raznoglaz1y/enku/docs/runtime-state-machine.md

# ENKU Reader Runtime & State Machine

This document defines the baseline runtime behavior for opening books, navigating pages, changing reader settings, sleeping, waking and recovering from errors.

The goal is deterministic behavior: the same event in the same state should produce the same state transition and the same visible result.

## 1. Runtime principle

The Reader runtime is event-driven.

User input and system events update application state first. Rendering follows only when visible state changes.

Conceptually:

```text
Input/System Event
→ Event Queue
→ State Transition
→ Reader/Layout Work
→ Render Plan
→ Refresh Manager
→ Display
```

## 2. Top-level application states

ENKU uses a small set of product-level states:

- **Boot**
- **Library**
- **Book Opening**
- **Reading**
- **Reader Overlay**
- **Search**
- **Settings**
- **Import/Transfer**
- **Sleep**
- **Error/Recovery**

These are logical runtime states, not necessarily one-to-one UI screens.

## 3. Reader sub-state

When Reading is active, the runtime keeps:

- current `book_id`;
- current semantic reading position;
- current laid-out page;
- previous/next page anchors when available;
- effective typography;
- orientation;
- active bookmark state;
- visible reader chrome state;
- pending progress save state.

The displayed page is disposable. The semantic position is authoritative.

## 4. Opening a book

Canonical flow:

```text
Library
→ OpenBookRequested
→ Book Opening
→ loader validates Library/storage and opens ReaderSession
→ BookOpened
→ synchronize AppState from current Reader page
→ render first/current page
→ Reading
```

If book loading fails, `BookOpenFailed` closes any partial session and returns safely to Library with the requested book focused.

If no saved position exists, reading begins at the first valid content position.

If a saved anchor can no longer be resolved exactly, the Reader Engine should restore the nearest safe logical position.

## 5. Page Next

When the user requests Next:

1. ignore/reject duplicate input while the current page transition is not ready;
2. ask ReaderSession to advance using the current page's next semantic anchor;
3. reuse prefetched next page or ask Reader Engine to paginate it;
4. update current semantic position;
5. mark progress as dirty;
6. render the new page;
7. schedule persistence independently from display refresh.

The UI must not advance stored progress before a valid next page exists.

The first concrete implementation of this path is documented in [Reader Runtime Integration MVP](reader-runtime-mvp.md). It updates `AppState.reading_position` / `reading_progress`, marks `progress_dirty`, and emits a PageTurn `RefreshRequest` only after ReaderSession accepts the transition.

## 6. Page Previous

Previous returns to a deterministic prior logical page through ReaderSession.

The current MVP stores page-start semantic anchors actually visited during the session and keeps a disposable previous/current/next working set. If an adjacent page is not cached, it is rebuilt from the stored page-start anchor.

The runtime never approximates Previous by subtracting an arbitrary number of characters.

## 7. End of book

When no next readable content exists:

- do not wrap automatically to the beginning;
- expose the Finished state;
- allow the user to return to Library;
- preserve the final semantic position;
- mark the book Finished only through the defined completion behavior.

On EndOfBook, runtime marks the current book Finished, sets logical progress to 1.0, updates the Library summary and emits a visible status refresh. It does not wrap to the beginning.

Restarting a finished book changes its Library state back to Reading through an explicit product action.

## 8. Reader chrome / overlay

Normal Reading should remain content-first.

Opening Reader Menu or Quick Aa moves into a Reader Overlay state while preserving:

- book;
- semantic position;
- underlying page;
- orientation.

Closing the overlay returns to the exact underlying Reading state.

Opening/closing an overlay must not itself change reading progress.

## 9. Typography change

Canonical transition:

```text
Reading/Overlay
→ TypographyChanged
→ preserve semantic anchor
→ resolve effective settings
→ invalidate incompatible page cache
→ repaginate around anchor
→ render
→ return to Reading/Overlay
```

Manual typography changes switch the effective preset to Custom.

## 10. Orientation change

Canonical transition:

```text
Reading
→ OrientationChanged
→ preserve semantic anchor
→ update viewport
→ invalidate layout cache
→ repaginate
→ render full new layout
→ Reading
```

Pixel coordinates are not persisted.

## 11. Bookmark toggle

Bookmark creation stores:

- `book_id`;
- semantic position;
- optional section/chapter title;
- short text snippet;
- creation order/timestamp.

Toggling a bookmark updates state/persistence, but should only redraw a visible bookmark indicator if such an indicator is currently shown.

## 12. Table of contents navigation

Selecting a ToC entry:

1. resolve its semantic position;
2. preserve the current position as normal history/state;
3. paginate at the target;
4. update current reading position;
5. render;
6. return to Reading.

ToC navigation never depends on rendered page numbers.

## 13. Search flow

Canonical search flow:

```text
Reading
→ SearchOpen
→ query entry
→ normalized-text search
→ results list
→ result selected
→ resolve semantic position
→ paginate
→ highlight semantic match
→ Reading
```

The pre-search reading position should remain available so Back/Cancel can return the user to where search began.

Search highlighting is temporary UI state and does not alter book content.

## 14. Back behavior

Back is deterministic and context-sensitive.

When Back is pressed from Reading, runtime checkpoints dirty semantic position/progress before closing ReaderSession and returning to Library. If checkpointing fails, the Reader remains open so unsaved progress is not silently discarded.

Examples:

- Reading → Library;
- Reader Overlay → Reading;
- Search results → Search query/results context;
- Search canceled from reader → original Reading position;
- nested Settings → previous Settings level;
- recoverable error → previous safe state.

Back must never silently discard a destructive pending action without following the relevant confirmation rule.

## 15. Progress persistence

Progress saving should not block every page turn.

Recommended model:

- update in-memory semantic position immediately;
- mark progress dirty;
- persist after a short safe debounce, on important transitions, and before sleep/power-down where possible.

Important save points include:

- leaving the book;
- entering Sleep;
- explicit Power Off;
- application state checkpoint;
- selected periodic/debounced page progress.

The exact debounce interval remains an implementation detail.

## 16. Sleep

The detailed product/hardware split is defined in [Power, Sleep & Wake Model](power-model.md).

Canonical user-facing Sleep flow:

```text
active state
→ SleepRequested
→ finish/abort unsafe operation according to subsystem rules
→ persist dirty reader/app state
→ stop Wi-Fi / quiesce peripherals
→ prepare static sleep screen
→ final display update
→ e-paper sleep
→ enter verified system suspend mechanism
```

Panel-only sleep is not considered full ENKU Sleep.

No animation or live clock is maintained in Sleep.

Writes/imports/transfers may temporarily block automatic sleep.

## 17. Wake

Wake should restore the previous logical context when safe.

Typical flow:

```text
Sleep
→ Wake
→ restore application state
→ validate storage/book availability
→ restore current screen/book semantic position
→ repaginate if required
→ render
```

If the current book is unavailable, ENKU falls back to Library with a recoverable error notice rather than entering a broken Reading state.

## 18. Hard power-off / reboot recovery

Persistent state must be sufficient to recover without relying on the framebuffer.

After reboot:

- follow the staged startup sequence defined in [Boot & Startup Architecture](boot-model.md);
- validate settings/state version;
- recover or clean incomplete transactions;
- evaluate boot-loop / Recovery Mode before automatic restore;
- load Library index;
- restore last safe product state when appropriate;
- restore semantic reading position, not rendered page;
- regenerate any disposable layout/cache.

The exact hard power-off mechanism remains hardware-dependent.

## 19. Import/transfer interaction

Reading and Library state must remain logically independent from transfer progress.

During an active write/import:

- automatic sleep is suspended;
- destructive storage actions are serialized;
- display updates for progress are throttled;
- failed import does not alter existing valid books.

Manual reading may remain available only if storage access can be safely coordinated; this is an implementation choice to verify on hardware.

## 20. Error model

Errors are divided into:

- **recoverable** — user can return to the previous safe state;
- **book-specific** — one book cannot open/render;
- **storage-specific** — media unavailable or inconsistent;
- **system-level** — critical runtime failure.

Examples:

- corrupt book → Library remains available;
- missing current book after wake → return to Library;
- parser/layout failure → preserve last valid semantic position;
- failed import → existing Library remains unchanged.

Raw diagnostics belong in logs, not as primary user-facing copy.

The full error classification, logging and Recovery/Safe Mode behavior is defined in [Errors, Logging & Diagnostics](diagnostics-model.md).

## 21. Input locking and repeated actions

Physical controls can generate repeated or rapid events.

The runtime should:

- debounce hardware input;
- avoid overlapping page-layout operations;
- coalesce redundant navigation where safe;
- never start two display refreshes concurrently;
- prevent double activation of destructive actions.

Long-press behavior is defined at the input/action layer, not separately inside every screen.

## 22. State history

ENKU should keep only the navigation history needed for predictable Back behavior.

History is logical, not framebuffer-based.

It may include:

- previous screen/context;
- pre-search reading anchor;
- overlay parent;
- focused Library item;
- relevant scroll/focus state.

It should not grow without bound.

## 23. Persistence vs transient state

Persistent examples:

- current book;
- semantic reading position;
- Library view/filter/sort;
- reading settings;
- bookmarks;
- selected language;
- orientation;
- trusted Wi-Fi information.

Transient examples:

- active render plan;
- dirty rectangles;
- current display list;
- temporary search highlight;
- open animation-equivalent transition state;
- page cache.

Transient state can be rebuilt after reboot.

## 24. State transition table

| Current state | Event | Next state | Key action |
| --- | --- | --- | --- |
| Library | OpenBook | Book Opening | Resolve metadata/state and paginate |
| Book Opening | Success | Reading | Render first/current page |
| Book Opening | Failure | Error/Recovery | Return safely to Library |
| Reading | Next | Reading | Paginate next semantic position |
| Reading | Previous | Reading | Resolve deterministic previous page |
| Reading | OpenMenu | Reader Overlay | Preserve underlying page |
| Reader Overlay | Close | Reading | Restore underlying page |
| Reading | Search | Search | Preserve pre-search anchor |
| Search | OpenResult | Reading | Jump to semantic match |
| Reading | OrientationChanged | Reading | Repaginate around anchor |
| Reading | TypographyChanged | Reading | Repaginate around anchor |
| Any safe state | SleepRequested | Sleep | Persist state and sleep |
| Sleep | Wake | Previous safe state | Rebuild transient layout |
| Any | RecoverableError | Error/Recovery | Preserve valid state |
| Error/Recovery | Back/Recover | Previous safe state | Resume without corruption |

## 25. Decisions fixed by this document

- Reader runtime is event-driven.
- Semantic position is authoritative at every transition.
- Page turns update progress only after valid layout exists.
- Back behavior is deterministic and context-aware.
- Reader overlays do not alter reading position.
- Search preserves the pre-search reading position.
- Sleep persists state before entering low power where possible.
- Wake reconstructs transient layout rather than restoring framebuffer state.
- Progress writes are debounced/checkpointed rather than blocking every page turn.
- Display/layout work is serialized.
- Errors must return to a safe usable state without corrupting book/library data.

## Refresh back-pressure

The detailed refresh queue and e-paper update policy are defined in [Refresh Manager & E-Paper Update Policy](refresh-model.md).

Runtime rules:

- only one physical display update executes at a time;
- stale queued render work may be discarded when newer full-screen state supersedes it;
- page-turn input cannot create an unbounded refresh queue;
- display failure does not roll back authoritative AppState;
- hidden state changes do not produce display work.

## 26. Persisted safe runtime context

Successful transition into Reading persists `Reading + book_id` through `AppContextService`.

Back from Reading persists `Library` before destroying the active ReaderSession. If that context write fails, Back is aborted so the previously safe Reading state is not silently discarded.

At cold boot, `BootRestoreCoordinator` reuses the ordinary `OpenBookRequested` runtime path rather than creating a second special-purpose reader-opening implementation. Therefore automatic restore uses the same Library lookup, checkpoint restore, parser, ReaderSession and failure behavior as a user-initiated open.

## 27. Sleep and fast Wake

`SleepWakeCoordinator` owns the product-level Sleep transition without embedding hardware-specific PMU/deep-sleep logic in ReaderRuntime.

When Sleeping from Reading, the semantic position is checkpointed even if the normal page-turn debounce has not fired yet. This makes Sleep an explicit persistence boundary.

Fast Wake does not create a special reader-opening path. It calls the same persisted-context restore logic used by cold boot, which in turn uses `OpenBookRequested`, checkpoint restore and `ReaderBookLoader`. The difference is that Wake skips the full storage transaction scan when the suspended runtime still has mounted/valid storage.

## 28. Graceful Power Off

Power Off is a separate runtime lifecycle from Sleep.

`PowerOffCoordinator` treats shutdown as a persistence boundary: Reading position, Library summary and last-safe app context must commit before `PowerService::requestPowerOff()` is called. Network is disconnected only after those writes succeed.

The next boot restores through the normal cold-boot path, so a powered-off device does not depend on retained RAM or framebuffer state.

## 29. Library and import runtime

The first concrete Library controller is now `LibraryRuntimeController`.

Canonical Library path:

```text
LibraryRefreshRequested
→ LibraryService::query()
→ bounded LibraryPage
→ normalize focus by book_id
→ RefreshService
```

Filter, sort and search events update typed `AppState.library` query state before re-running the query.

Opening a focused item does not duplicate Reader logic:

```text
OpenFocusedBookRequested
→ focused book_id
→ ReaderRuntimeController(OpenBookRequested)
→ normal Reader open/checkpoint/context flow
```

Import path:

```text
ImportRequested
→ import_active = true
→ StagedBookImportService
→ success / duplicate / failure
→ import_active = false
→ on success reload Library + focus imported book
```

This connects the import activity flag already consumed by Sleep and Power Off policy to a real runtime operation rather than leaving it as a passive field.

## 30. Delete focused book

Library runtime now accepts `DeleteFocusedBookRequested` only while the Library screen is active and no import transaction is running.

```text
DeleteFocusedBookRequested
→ BookDeleteService
→ remove Library/source/checkpoint/context safely
→ re-run active Library query
→ normalize focus by book_id
→ refresh Library
```

A failed delete returns `LibraryRuntimeResult::DeleteFailed` and does not masquerade as an empty Library or successful removal.

## 31. Physical input dispatch

Input now has three explicit layers:

```text
ESP-IDF GPIO polling
→ PhysicalInputEvent
→ InputActionMapper
→ LogicalAction
→ InputDispatcher
→ Library / Reader / Sleep-Wake / Power-Off runtime
```

This prevents board GPIO semantics from leaking into application controllers and makes the same runtime path testable with synthetic physical events on the host.

## 32. Concrete e-paper refresh service

The first physical `RefreshService` implementation is now `EpaperRefreshService`.

Its input remains the framework-neutral `RefreshRequest`.

Policy:

```text
RefreshClass::Full
→ true SSD1677 full refresh

RefreshClass::Region + valid small dirty_region + established base frame
→ partial refresh

RefreshClass::Region + missing/invalid/large dirty_region
→ escalate to fast full-screen refresh

RefreshClass::Deferred
→ fast full-screen refresh
```

A region larger than one third of the panel area is currently escalated.

The service also tracks:

- total requests;
- region refreshes;
- full-screen refreshes;
- escalations;
- coalesced generations;
- obsolete generations;
- failures.

`cancelObsolete(min_generation)` does not interrupt an in-flight physical panel transaction; it prevents older queued/subsequent requests from being applied.

## 33. Mono framebuffer boundary

`MonoFramebufferSource` separates rendering from display transport.

The e-paper service only knows:

- framebuffer dimensions;
- full 1-bit buffer;
- extraction of a dirty region.

`OwnedMonoFramebuffer` is the first concrete implementation and supports byte-aligned region extraction for SSD1677 partial windows.

The eventual Library/Reader renderer can write into this buffer without depending on ESP-IDF or SSD1677 APIs.

## 34. Application storage runtime composition

`ApplicationStorageRuntime` is now the first framework-neutral application composition layer above a pair of filesystem adapters.

It owns:

```text
AppState
CborSettingsService
SettingsRuntimeController
CborLibraryService
BookImportService
StagedBookImportService
CborReaderCheckpointService
CborAppContextService
CborBootLoopService
BookDeleteService
StoredBookSourceService
StorageStartupCoordinator
```

Construction requires only:

```text
StateFileStore
BookFileStore
```

This means the same composition is exercised with POSIX stores in host tests and with the ESP-IDF SD/FAT stores on the real board target.

The Reader controller graph is intentionally not owned here yet. Its remaining concrete dependency is a real `TextMeasurer`/render pipeline; introducing a fake device-side measurer would hide the actual integration work still required.

## 35. Real Reader font measurement and rasterization

The ESP-IDF target now has a concrete `FreeTypeTextRenderer`.

It serves two roles from the same Noto Sans face:

```text
TextMeasurer
→ exact FreeType advance/kerning metrics for pagination

Page renderer
→ FreeType monochrome glyph rasterization into OwnedMonoFramebuffer
```

The default Reader font path is:

```text
/sdcard/system/fonts/NotoSans-Regular.ttf
```

The font is intentionally loaded from the FAT filesystem rather than hidden behind a compile-time substitute. If the file is missing, initialization returns `FontNotFound`; ENKU does not silently replace Noto Sans with a different typeface.

Measurements support UTF-8 code points and FreeType kerning. Line height uses the face's actual size metrics multiplied by the current Reader line-spacing setting.

Rendering uses `FT_RENDER_MODE_MONO` and writes the resulting 1-bit glyph bitmaps directly into the existing 1-bit ENKU framebuffer.

This aligns pagination and rendering: the same font engine and size determine both where lines wrap and where glyphs are drawn.

## 36. Application Reader runtime composition

`ApplicationReaderRuntime` now composes the first complete Library/Reader controller graph above `ApplicationStorageRuntime`.

It owns:

```text
ReaderBookLoader
ReaderRuntimeController
LibraryRuntimeController
BootRestoreCoordinator
```

Dependencies are explicit:

```text
ApplicationStorageRuntime
RefreshService
TextMeasurer
ReaderPageRenderer
LibraryPageRenderer
TypographySettings
Viewport
```

On ESP-IDF, one `FreeTypeTextRenderer` supplies all three text/render roles: measurement, Reader page rendering and Library rendering.

## 37. Render-before-refresh contract

Both Reading and Library now update the framebuffer before submitting a physical refresh.

Reader:

```text
ReaderSession page transition
→ update semantic state
→ ReaderPageRenderer
→ RefreshService
```

Library:

```text
query/focus/view state change
→ LibraryPageRenderer
→ RefreshService
```

A renderer failure is surfaced explicitly (`RenderFailed`) rather than allowing runtime state to claim that an unrendered frame became visible.

The first ESP-IDF Library renderer is intentionally simple but real: Noto Sans header, title/author/progress rows and a focus outline.

## 38. ESP-IDF DeviceRuntime

`EspIdfDeviceRuntime` is the first board-specific application composition root above `EspIdfPlatform`.

It connects:

```text
EspIdfPlatform
→ ApplicationStorageRuntime
→ FreeTypeTextRenderer
→ ApplicationReaderRuntime
→ SleepWakeCoordinator
→ PowerOffCoordinator
→ InputDispatcher
```

Boot sequence:

```text
platform begin
→ font availability / FreeType init
→ storage/settings/library startup
→ boot-loop/context restore
→ restore Reading or settle Library
→ apply Wi-Fi policy
→ synchronize network/power state
→ render initial Library when needed
→ enter application loop
```

A missing Noto Sans asset is treated as a provisioning state, not silently substituted with another font.

## 39. Persistent application loop

The normal ESP-IDF execution path no longer ends after a finite input smoke test.

After successful DeviceRuntime initialization, firmware continuously polls the board controls at the configured 5 ms cadence and dispatches events through the real application graph.

Hardware smoke tests remain available behind `CONFIG_ENKU_BRINGUP_SMOKE_TESTS` while physical validation is in progress.

The current persistent loop is intentionally synchronous: page layout, rendering and e-paper refresh complete before the next visible transition is accepted. This favors deterministic e-paper behavior over premature concurrency; later profiling may introduce task separation where measured benefit justifies it.

## 40. Orientation-aware pagination and rendering

Orientation is now a real layout/rendering input rather than a persisted flag only.

The Reader derives the logical viewport from the native panel geometry:

```text
Portrait  = short side × long side
Landscape = long side × short side
```

For the current 800×480 panel:

```text
Portrait  = 480×800
Landscape = 800×480
```

Reader pagination always works in logical coordinates.

The ESP-IDF FreeType renderer then maps logical pixels into the controller-native 800×480 framebuffer. Portrait currently uses a clockwise 90° transform; the exact physical rotation direction remains easy to swap after enclosure/orientation validation without changing Reader pagination semantics.

### Live orientation reflow

`ApplicationReaderRuntime::applyOrientation()` now performs a durable, live orientation transition.

While Reading:

```text
save new Orientation setting
→ preserve current semantic page anchor
→ derive new logical viewport
→ ReaderSession::invalidateLayout()
→ repaginate from the same semantic position
→ render in the new orientation
→ full visible refresh
```

The semantic text offset remains authoritative and is preserved across the reflow.

While Library is visible, the same operation persists the setting and re-renders the Library in the new logical geometry.

If runtime application of the new orientation fails after persistence, ENKU performs a best-effort rollback to the previous durable setting and previous layout.

## Library return-state preservation

Library navigation state is intentionally preserved in-memory while opening and closing a book:

- current query offset remains unchanged;
- the focused book remains selected;
- Grid/List view remains controlled by persisted GlobalSettings;
- returning from Reading refreshes the same Library window instead of resetting to offset 0;
- changing orientation while Library is visible re-renders the current window without resetting offset or focus.

This applies to ordinary Library browsing and keeps the same runtime position across Reader open → Back transitions.

## Library query-state rules

Library query transitions use deterministic navigation rules:

- changing Filter switches to Browse mode, clears active search text, resets offset to 0, and preserves the focused book only when it remains present in the new first window; otherwise focus moves to the first valid item;
- changing Sort or sort direction preserves Browse/Search mode and current search text, resets offset to 0, and keeps the focused book only when it is present in the new first window;
- changing Grid/List view does not change offset, focused book, active search text, or query mode;
- orientation changes redraw/reload the current Library window without resetting offset or focus.

## Library mutation pagination rules

Library mutations keep pagination valid and deterministic:

- deleting the last visible book on the last query window clamps offset to the last valid window and focuses a valid remaining book;
- deleting the final book in the Library leaves an empty page with no focused book;
- successful import exits Search mode and clears the active search text;
- after import, the runtime reveals and focuses the imported book in whatever query window contains it, including Recently Added with ascending order;
- import reveal respects the current page limit and sort direction instead of assuming the imported book is in the first window.

## Book Details runtime

Book Details is a dedicated runtime screen opened for the currently focused Library book.

Semantic content is identical in portrait and landscape; orientation changes layout only.

Primary action is derived from canonical reading state:

- New -> Start;
- Reading -> Continue;
- Finished -> Read again.

Read again always enters the approved restart confirmation first. Confirmation defaults to Cancel. A confirmed restart erases the saved reading checkpoint, resets summary progress to 0, transitions the book to Reading, preserves the source book and other per-book domains, then opens the book from the beginning.

Delete Book enters a separate destructive confirmation with Cancel as the default focus. Confirmed deletion uses the transactional BookDeleteService and returns to Library with pagination/focus normalized.

Back from a confirmation cancels the confirmation without changing book data. Back from Book Details returns to the same Library context.
