raznoglaz1y/enku/docs/screens.md

# Screen inventory

This file indexes the screen assets currently stored in the repository.

The **Figma design system is the current visual source of truth** for active UI work. Existing RU PNG boards remain valuable historical/reference material, while EN boards in the repository may be drafts or incomplete until they pass the review workflow.

Current design-state rules:

- English is the canonical/source UI language.
- Approved final review boards are PNG.
- Temporary EN SVG screen compositions are intermediate artifacts only.
- Figma component work currently includes Foundations, Statusbar, Header and Primary Button; Universal Row is in progress.
- A board is not implementation-ready merely because a historical file exists in this index.
- Implementation readiness is defined by [UI audit](ui-audit.md), [UI specification](ui-spec.md) and [UI revision plan](ui-revision-plan.md).

The table below is therefore an **asset inventory**, not a statement that each listed board is current or approved.

| Board | Available file | English |
| --- | --- | --- |
| ENKU_about_device | [PNG](../design/screens/ru/ENKU_about_device_v1.png) | pending |
| ENKU_add_book | [PNG](../design/screens/ru/ENKU_add_book_v1.png) | pending |
| ENKU_book_details | [PNG](../design/screens/ru/ENKU_book_details_v1.png) | pending |
| ENKU_book_error | [PNG](../design/screens/ru/ENKU_book_error_v2.png) | pending |
| ENKU_book_finished | [PNG](../design/screens/ru/ENKU_book_finished_v1.png) | pending |
| ENKU_book_validation | [PNG](../design/screens/ru/ENKU_book_validation_v1.png) | pending |
| ENKU_cancel_transfer | [PNG](../design/screens/ru/ENKU_cancel_transfer_v1.png) | pending |
| ENKU_contents_bookmarks | [PNG](../design/screens/ru/ENKU_contents_bookmarks_v3.png) | pending |
| ENKU_delete_book | [PNG](../design/screens/ru/ENKU_delete_book_v2.png) | pending |
| ENKU_display_settings | [PNG](../design/screens/ru/ENKU_display_settings_v1.png) | pending |
| ENKU_empty_bookmarks | [PNG](../design/screens/ru/ENKU_empty_bookmarks_v1.png) | pending |
| ENKU_empty_filter | [PNG](../design/screens/ru/ENKU_empty_filter_v1.png) | pending |
| ENKU_empty_library | [PNG](../design/screens/ru/ENKU_empty_library_v1.png) | pending |
| ENKU_empty_networks | [PNG](../design/screens/ru/ENKU_empty_networks_v1.png) | pending |
| ENKU_english_check | [PNG](../design/screens/en/ENKU_english_check_v1.png) | sample only |
| ENKU_file_browser | [PNG](../design/screens/ru/ENKU_file_browser_v1.png) | pending |
| ENKU_filter_sort | [PNG](../design/screens/ru/ENKU_filter_sort_v1.png) | pending |
| ENKU_first_start_controls | [PNG](../design/screens/ru/ENKU_first_start_controls_v1.png) | pending |
| ENKU_first_start_language | [PNG](../design/screens/ru/ENKU_first_start_language_v1.png) | pending |
| ENKU_first_start_orientation | [PNG](../design/screens/ru/ENKU_first_start_orientation_v1.png) | pending |
| ENKU_focus_states | [PNG](../design/screens/ru/ENKU_focus_states_v1.png) | pending |
| ENKU_forget_network | [PNG](../design/screens/ru/ENKU_forget_network_v1.png) | pending |
| ENKU_import_complete | [PNG](../design/screens/ru/ENKU_import_complete_v1.png) | pending |
| ENKU_import_methods | [PNG](../design/screens/ru/ENKU_import_methods_v1.png) | pending |
| ENKU_import_summary | [PNG](../design/screens/ru/ENKU_import_summary_v1.png) | pending |
| ENKU_language | [PNG](../design/screens/ru/ENKU_language_v1.png) | pending |
| ENKU_library | [PNG](../design/screens/ru/ENKU_library_v1.png) | pending |
| ENKU_library_list | [PNG](../design/screens/ru/ENKU_library_list_v1.png) | pending |
| ENKU_library_search | [PNG](../design/screens/ru/ENKU_library_search_v1.png) | pending |
| ENKU_long_text_check | [PNG](../design/screens/ru/ENKU_long_text_check_v1.png) | pending |
| ENKU_low_battery | [PNG](../design/screens/ru/ENKU_low_battery_v1.png) | pending |
| ENKU_memory_card_error | [PNG](../design/screens/ru/ENKU_memory_card_error_v1.png) | pending |
| ENKU_navigation_status | [PNG](../design/screens/ru/ENKU_navigation_status_v2.png) | pending |
| ENKU_no_contents | [PNG](../design/screens/ru/ENKU_no_contents_v1.png) | pending |
| ENKU_no_memory_card | [PNG](../design/screens/ru/ENKU_no_memory_card_v1.png) | pending |
| ENKU_no_search_results | [PNG](../design/screens/ru/ENKU_no_search_results_v1.png) | pending |
| ENKU_not_enough_space | [PNG](../design/screens/ru/ENKU_not_enough_space_v1.png) | pending |
| ENKU_portrait_orientation | [PNG](../design/screens/ru/ENKU_portrait_orientation_v2.png) | pending |
| ENKU_power_off | [PNG](../design/screens/ru/ENKU_power_off_v1.png) | pending |
| ENKU_quick_aa_preview | [PNG](../design/screens/ru/ENKU_quick_aa_preview_v3.png) | pending |
| ENKU_reading_menu | [PNG](../design/screens/ru/ENKU_reading_menu_v2.png) | pending |
| ENKU_replace_book | [PNG](../design/screens/ru/ENKU_replace_book_v1.png) | pending |
| ENKU_restart_reading | [PNG](../design/screens/ru/ENKU_restart_reading_v1.png) | pending |
| ENKU_saved_networks | [PNG](../design/screens/ru/ENKU_saved_networks_v1.png) | pending |
| ENKU_search_in_book | [PNG](../design/screens/ru/ENKU_search_in_book_v1.png) | pending |
| ENKU_search_match | [PNG](../design/screens/ru/ENKU_search_match_v1.png) | pending |
| ENKU_settings | [PNG](../design/screens/ru/ENKU_settings_v1.png) | pending |
| ENKU_sleep_cover | [PNG](../design/screens/ru/ENKU_sleep_cover_v1.png) | pending |
| ENKU_sleep_screen | [PNG](../design/screens/ru/ENKU_sleep_screen_v1.png) | pending |
| ENKU_sleep_settings | [PNG](../design/screens/ru/ENKU_sleep_settings_v1.png) | pending |
| ENKU_storage_import | [PNG](../design/screens/ru/ENKU_storage_import_v1.png) | pending |
| ENKU_transfer_interrupted | [PNG](../design/screens/ru/ENKU_transfer_interrupted_v1.png) | pending |
| ENKU_transfer_progress | [PNG](../design/screens/ru/ENKU_transfer_progress_v2.png) | pending |
| ENKU_typography | [PNG](../design/screens/ru/ENKU_typography_v1.png) | pending |
| ENKU_ui_kit_core | [PNG](../design/screens/ru/ENKU_ui_kit_core_v1.png) | pending |
| ENKU_usb_transfer | [PNG](../design/screens/ru/ENKU_usb_transfer_v2.png) | pending |
| ENKU_wifi | [PNG](../design/screens/ru/ENKU_wifi_v1.png) | pending |
| ENKU_wifi_password | [PNG](../design/screens/ru/ENKU_wifi_password_v3.png) | pending |
| ENKU_wifi_transfer | [PNG](../design/screens/ru/ENKU_wifi_transfer_v1.png) | pending |
