raznoglaz1y/enku/design/screens/ru/ENKU_about_device_v1.png

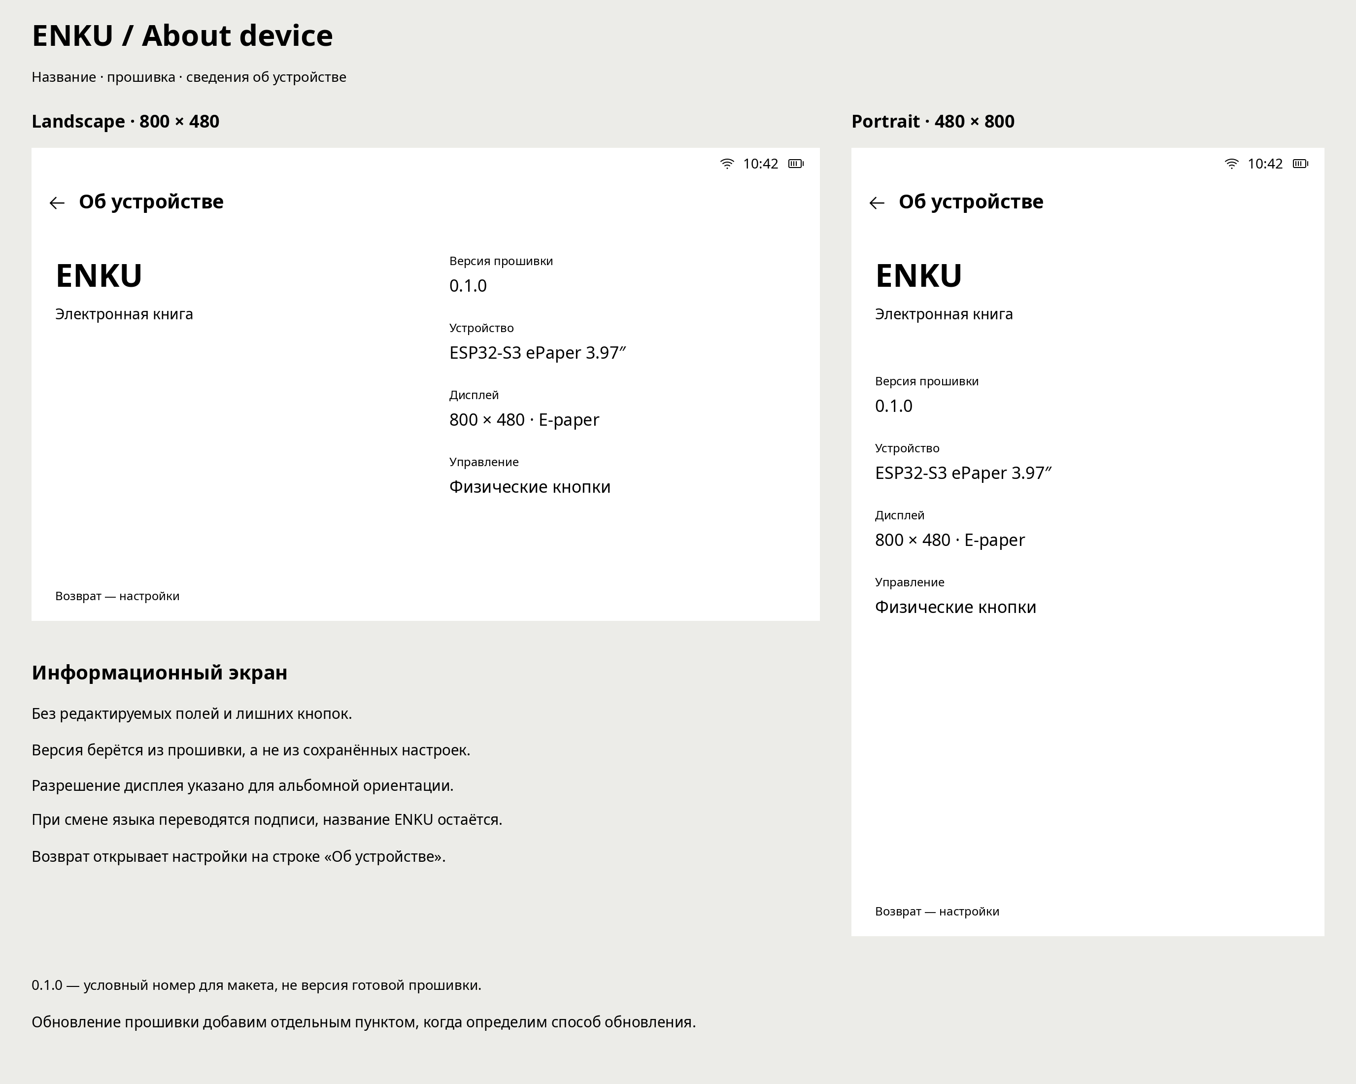
design/screens/ru/ENKU_about_device_v1.png
