raznoglaz1y/enku/design/screens/ru/ENKU_add_book_v1.png

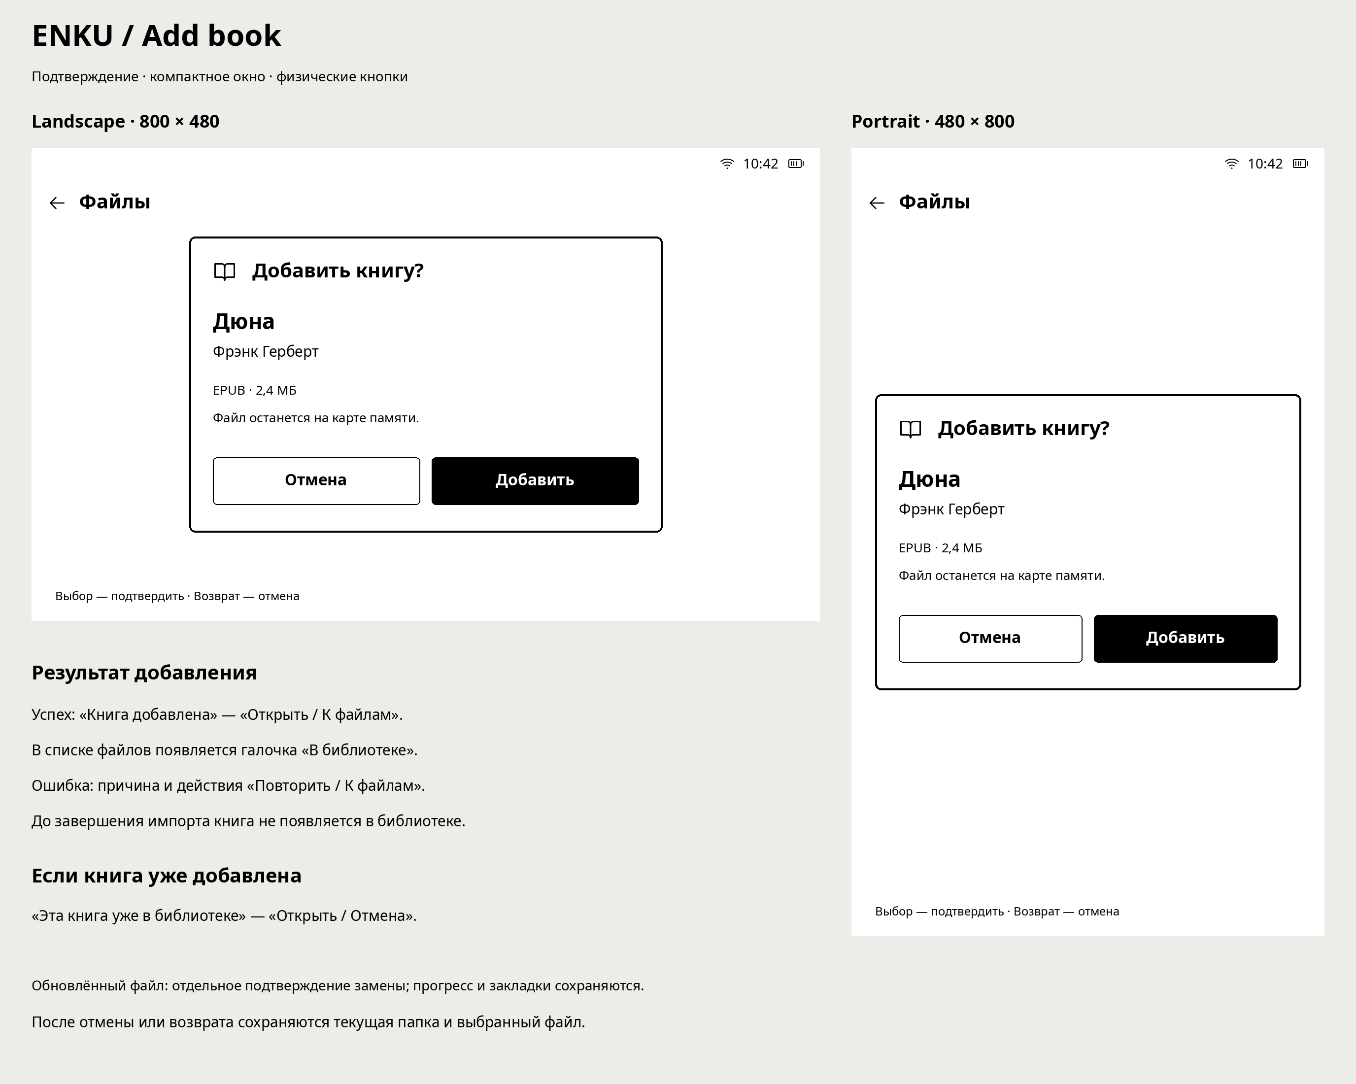
design/screens/ru/ENKU_add_book_v1.png
