raznoglaz1y/enku/design/screens/ru/ENKU_book_details_v1.png

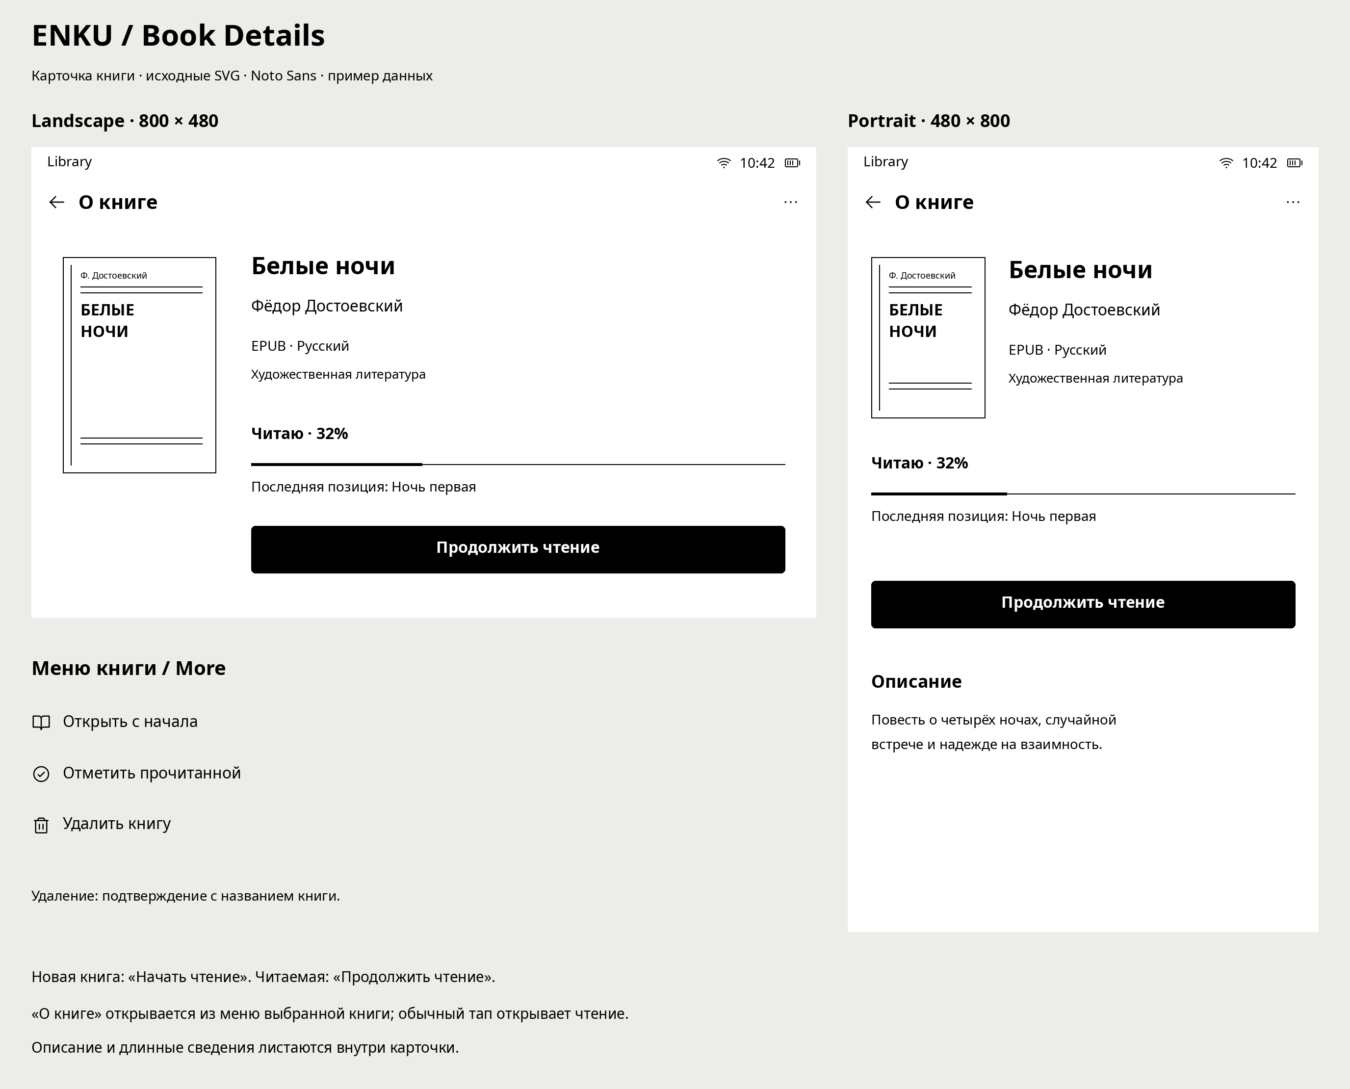
design/screens/ru/ENKU_book_details_v1.png
