raznoglaz1y/enku/design/screens/ru/ENKU_book_error_v2.png

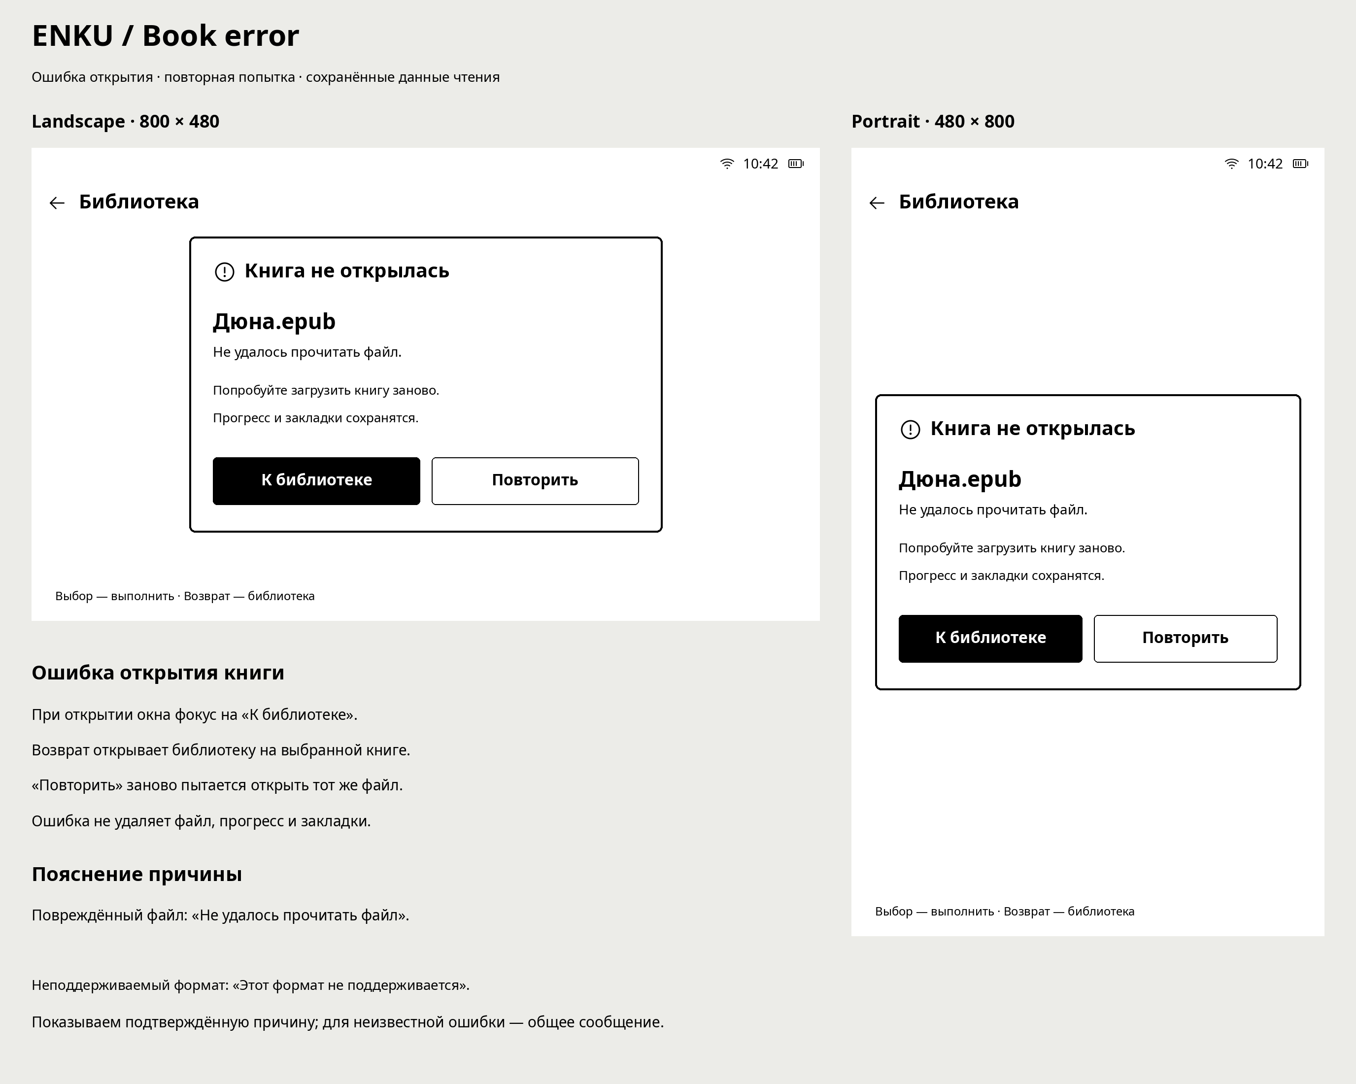
design/screens/ru/ENKU_book_error_v2.png
