raznoglaz1y/enku/design/screens/ru/ENKU_book_finished_v1.png

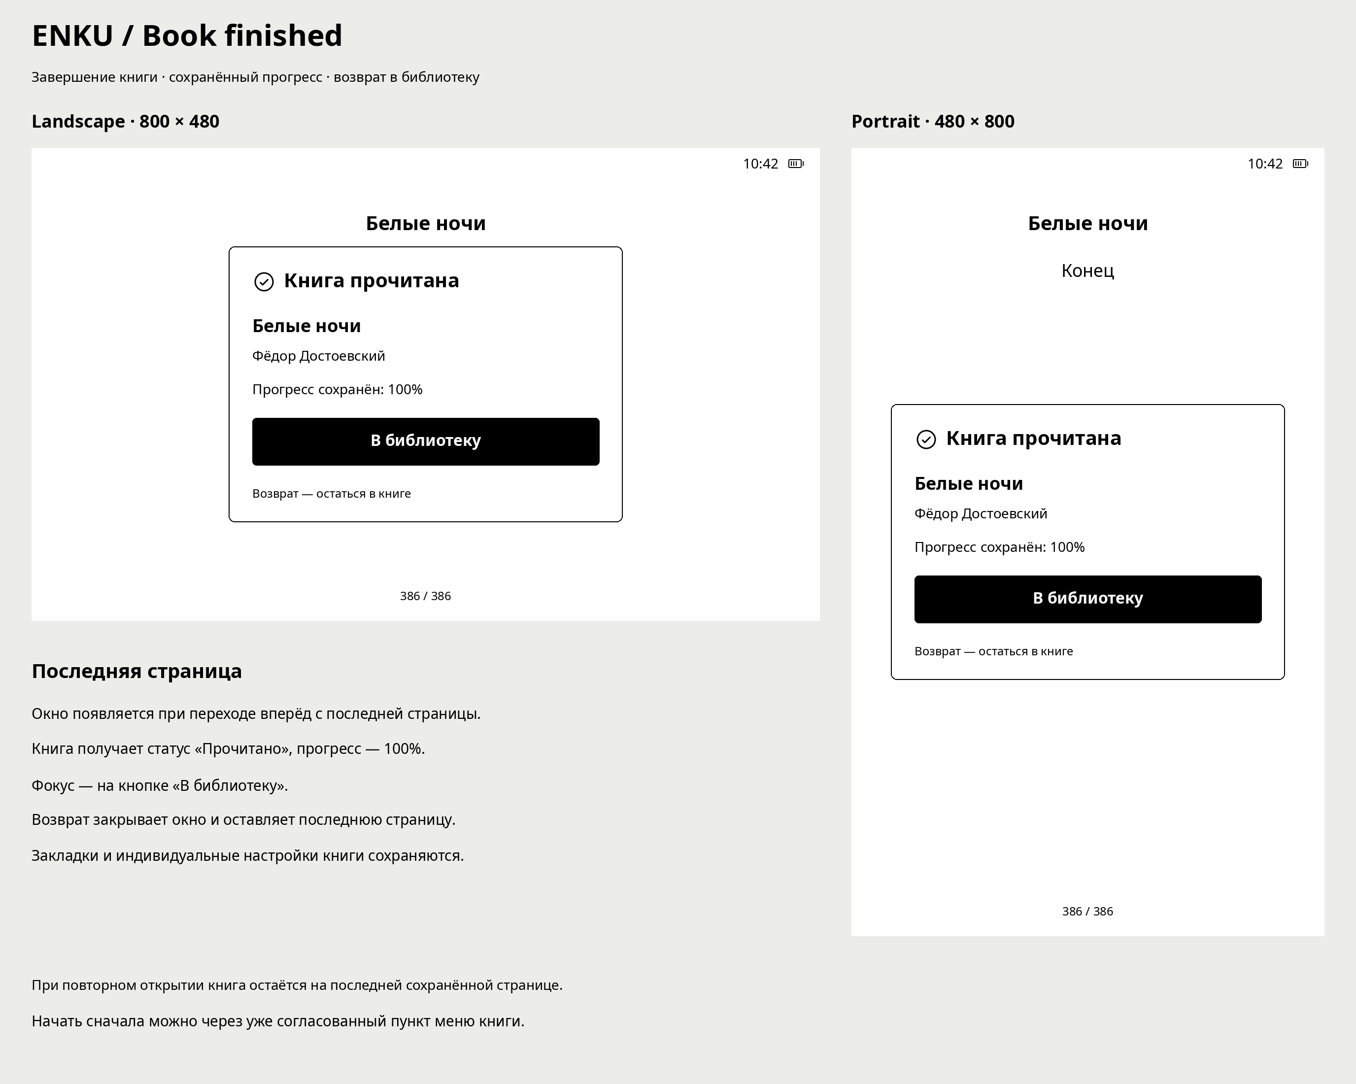
design/screens/ru/ENKU_book_finished_v1.png
