raznoglaz1y/enku/design/screens/ru/ENKU_cancel_transfer_v1.png

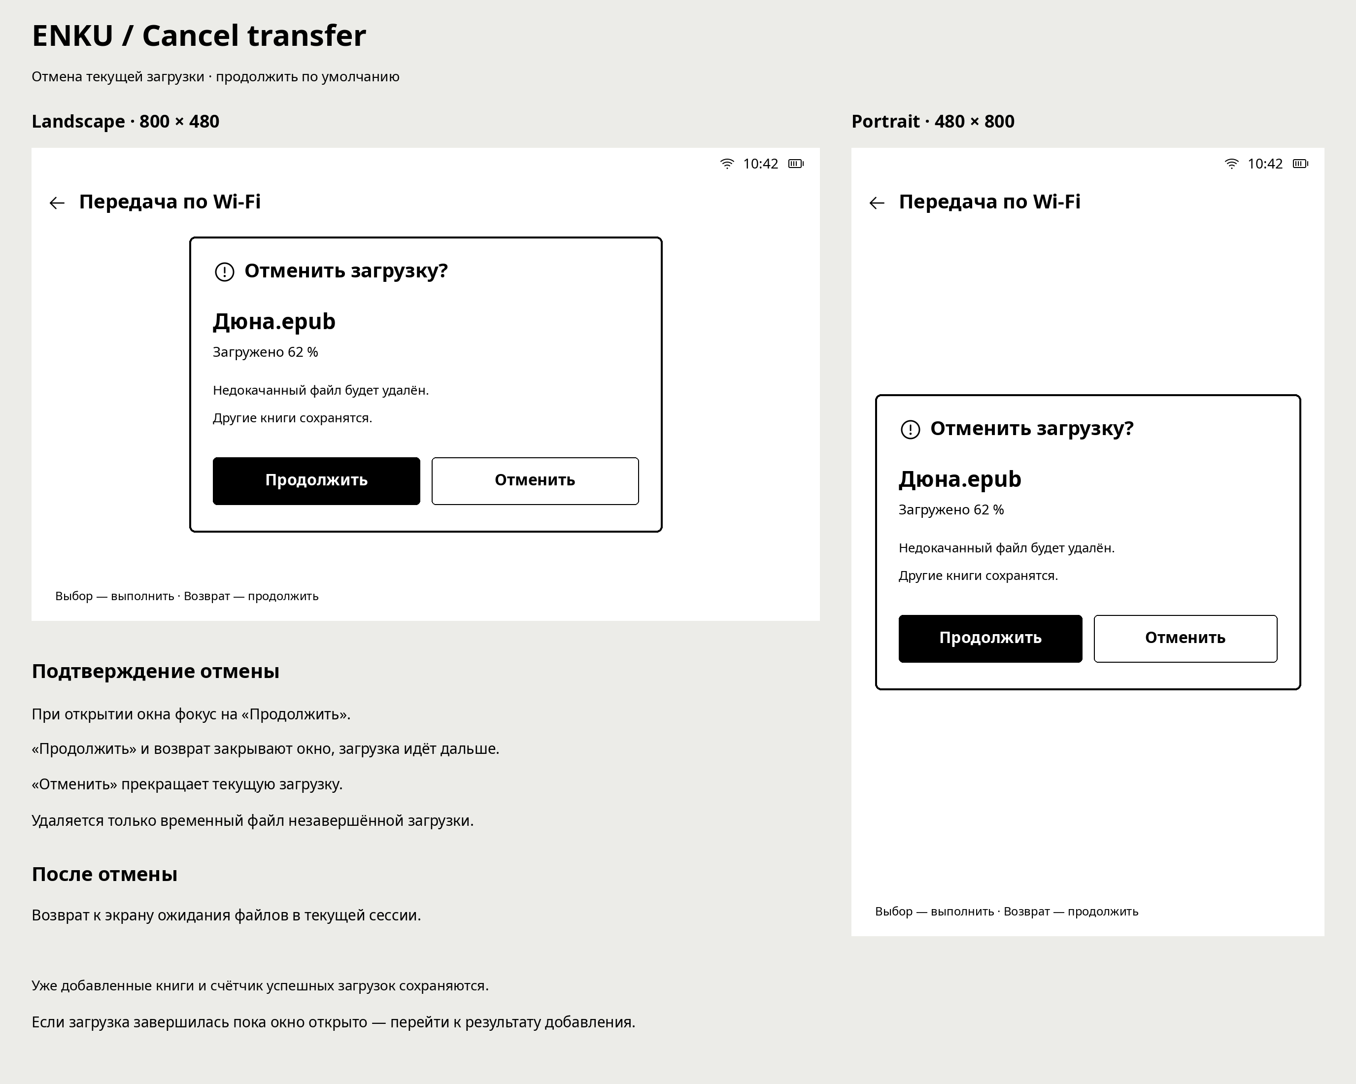
design/screens/ru/ENKU_cancel_transfer_v1.png
