raznoglaz1y/enku/design/screens/ru/ENKU_contents_bookmarks_v3.png

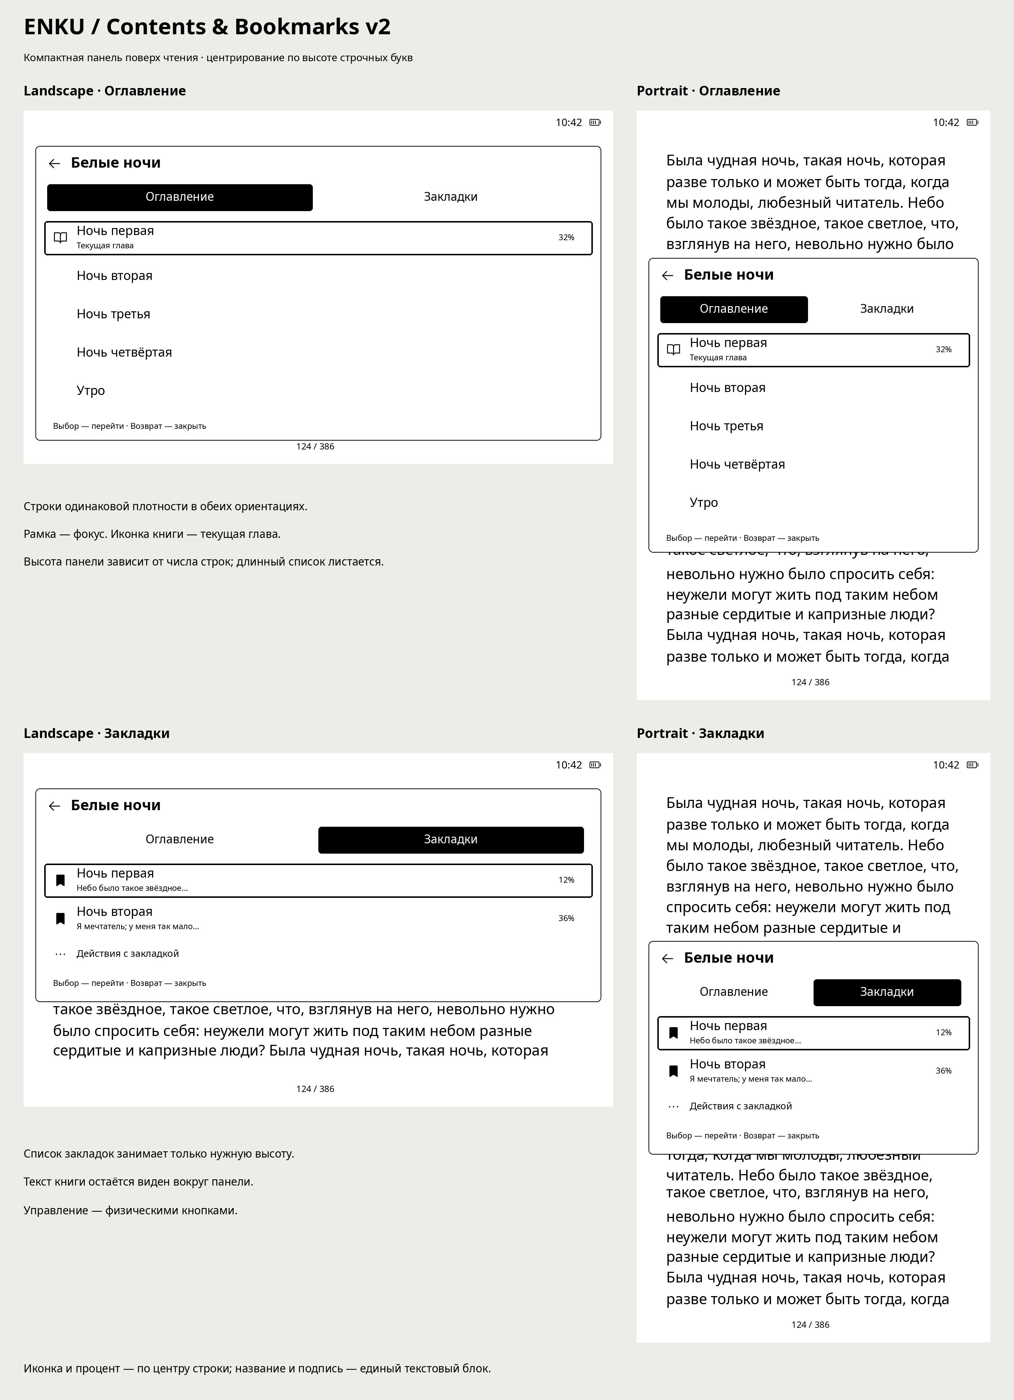
design/screens/ru/ENKU_contents_bookmarks_v3.png
