raznoglaz1y/enku/design/screens/ru/ENKU_delete_book_v2.png

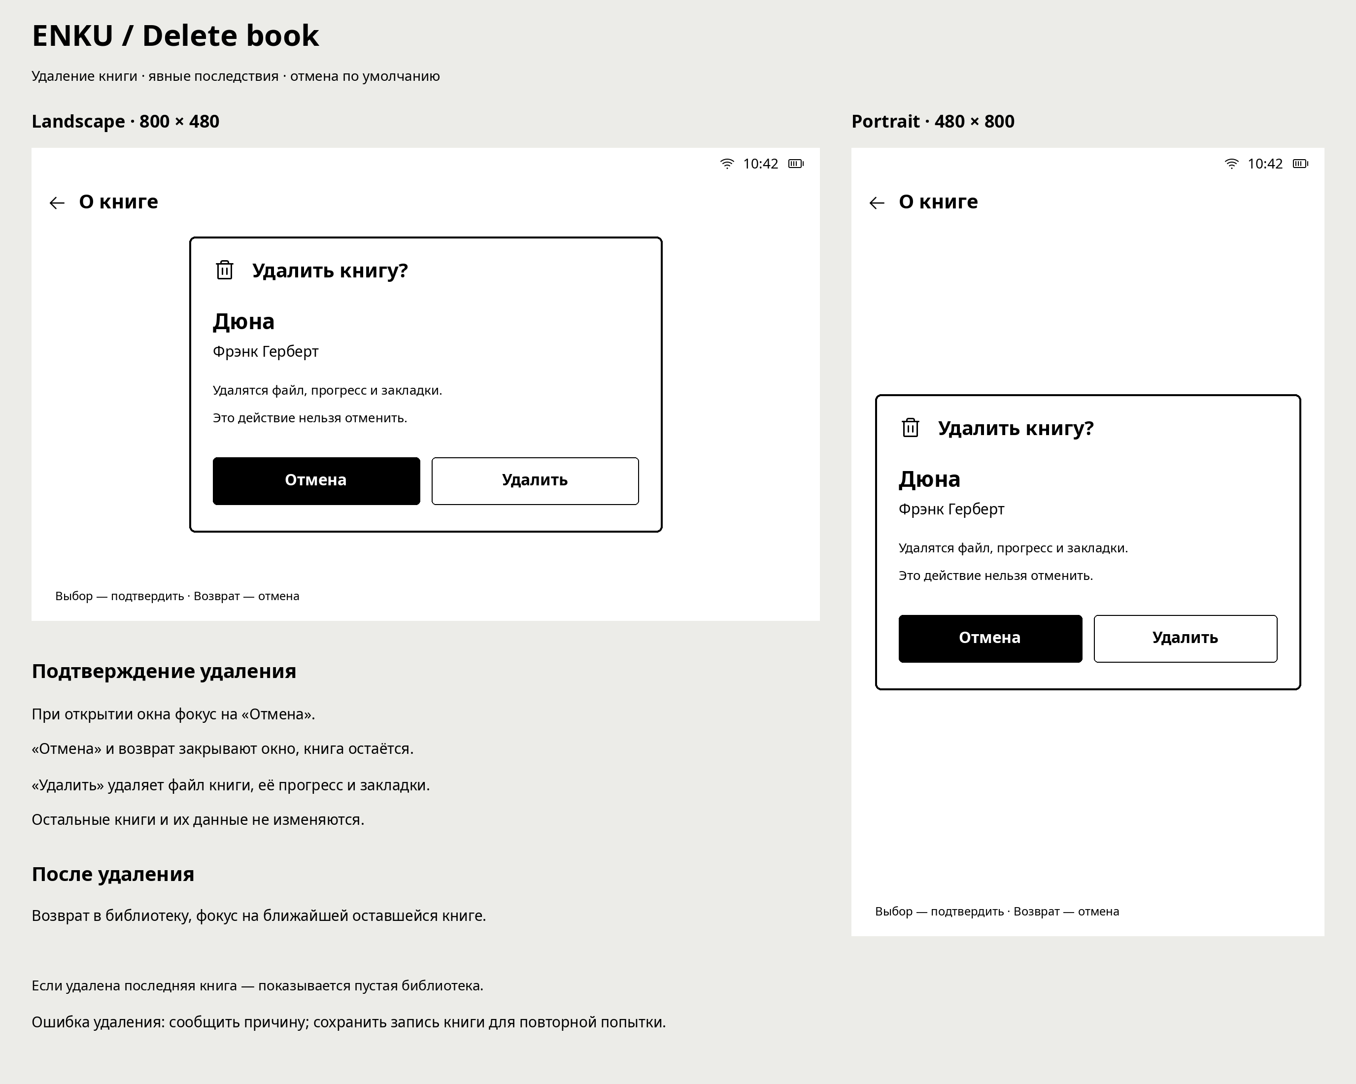
design/screens/ru/ENKU_delete_book_v2.png
