raznoglaz1y/enku/design/screens/ru/ENKU_display_settings_v1.png

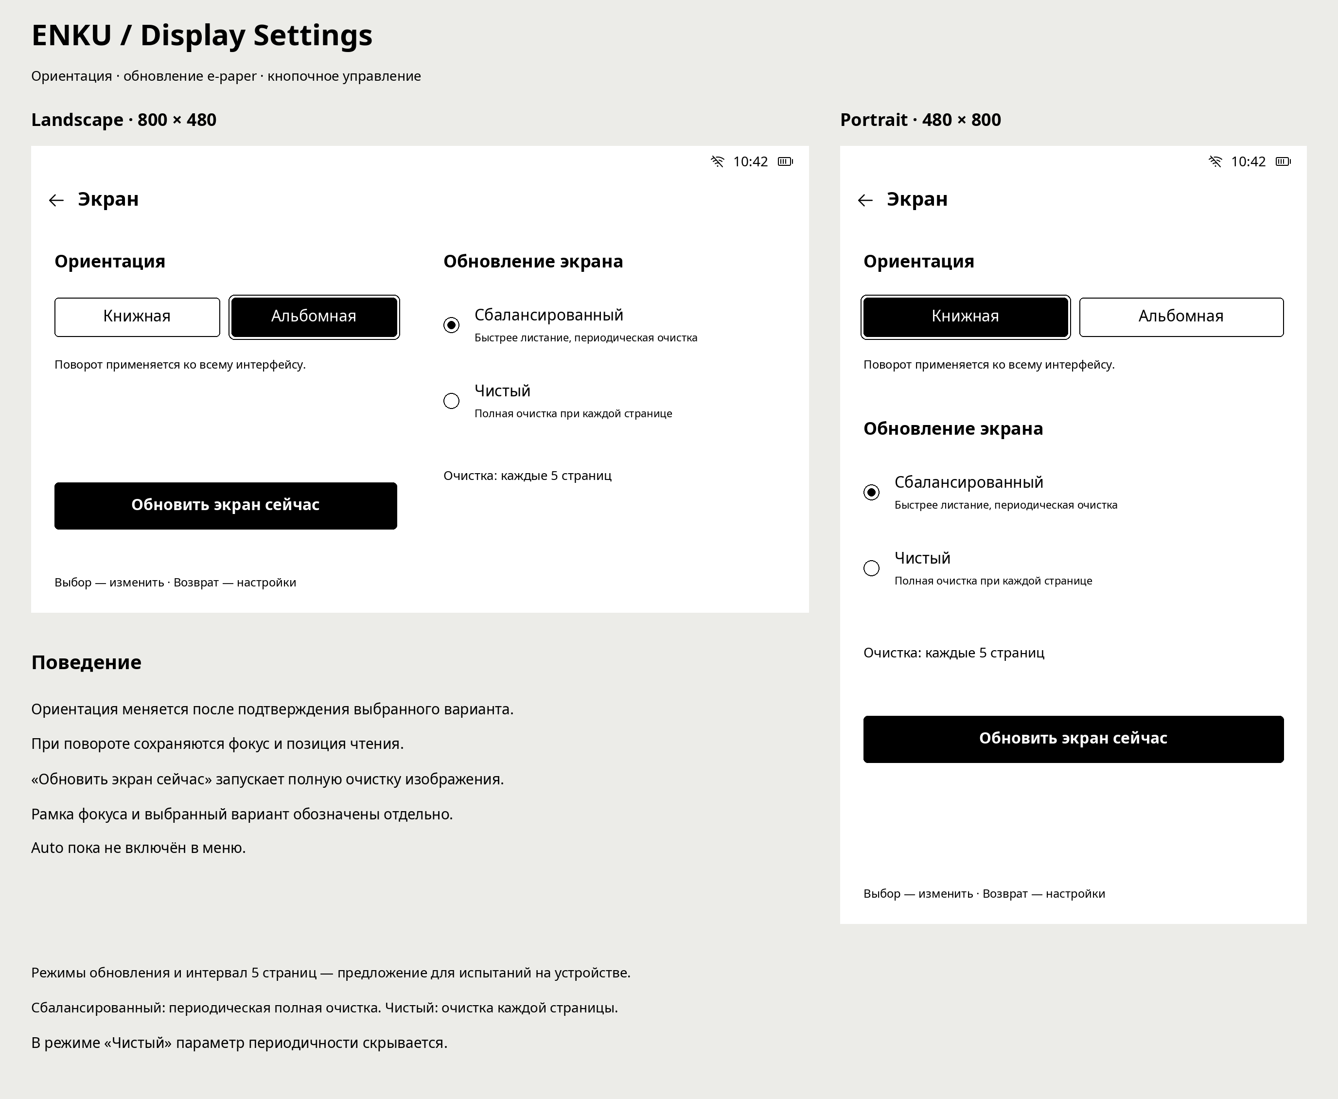
design/screens/ru/ENKU_display_settings_v1.png
