raznoglaz1y/enku/design/screens/ru/ENKU_empty_bookmarks_v1.png

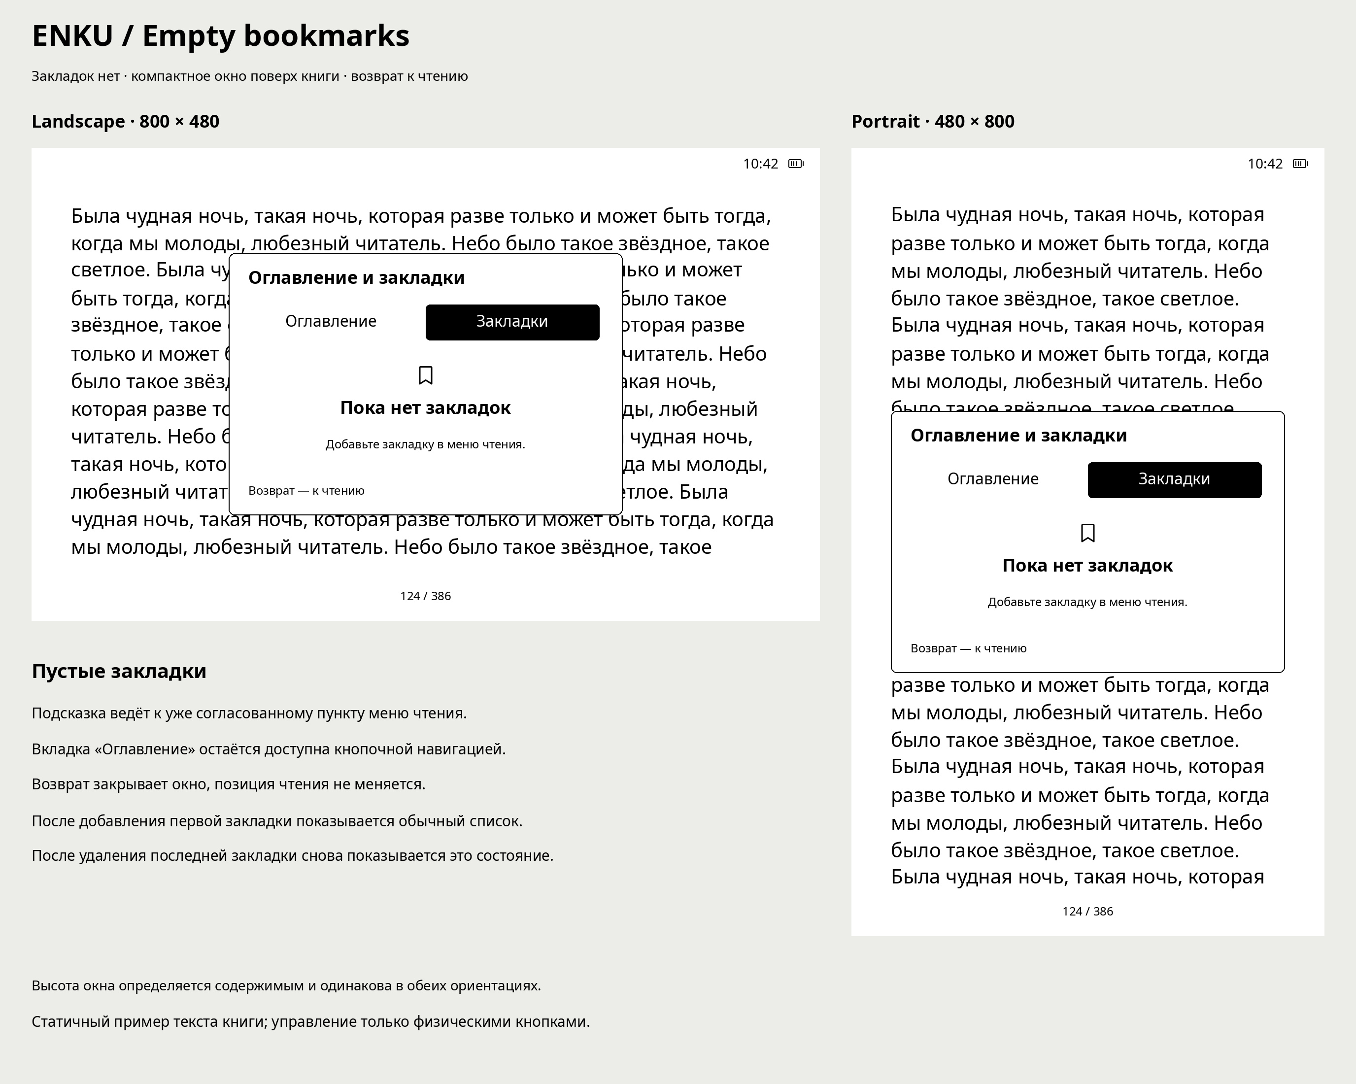
design/screens/ru/ENKU_empty_bookmarks_v1.png
