raznoglaz1y/enku/design/screens/ru/ENKU_file_browser_v1.png

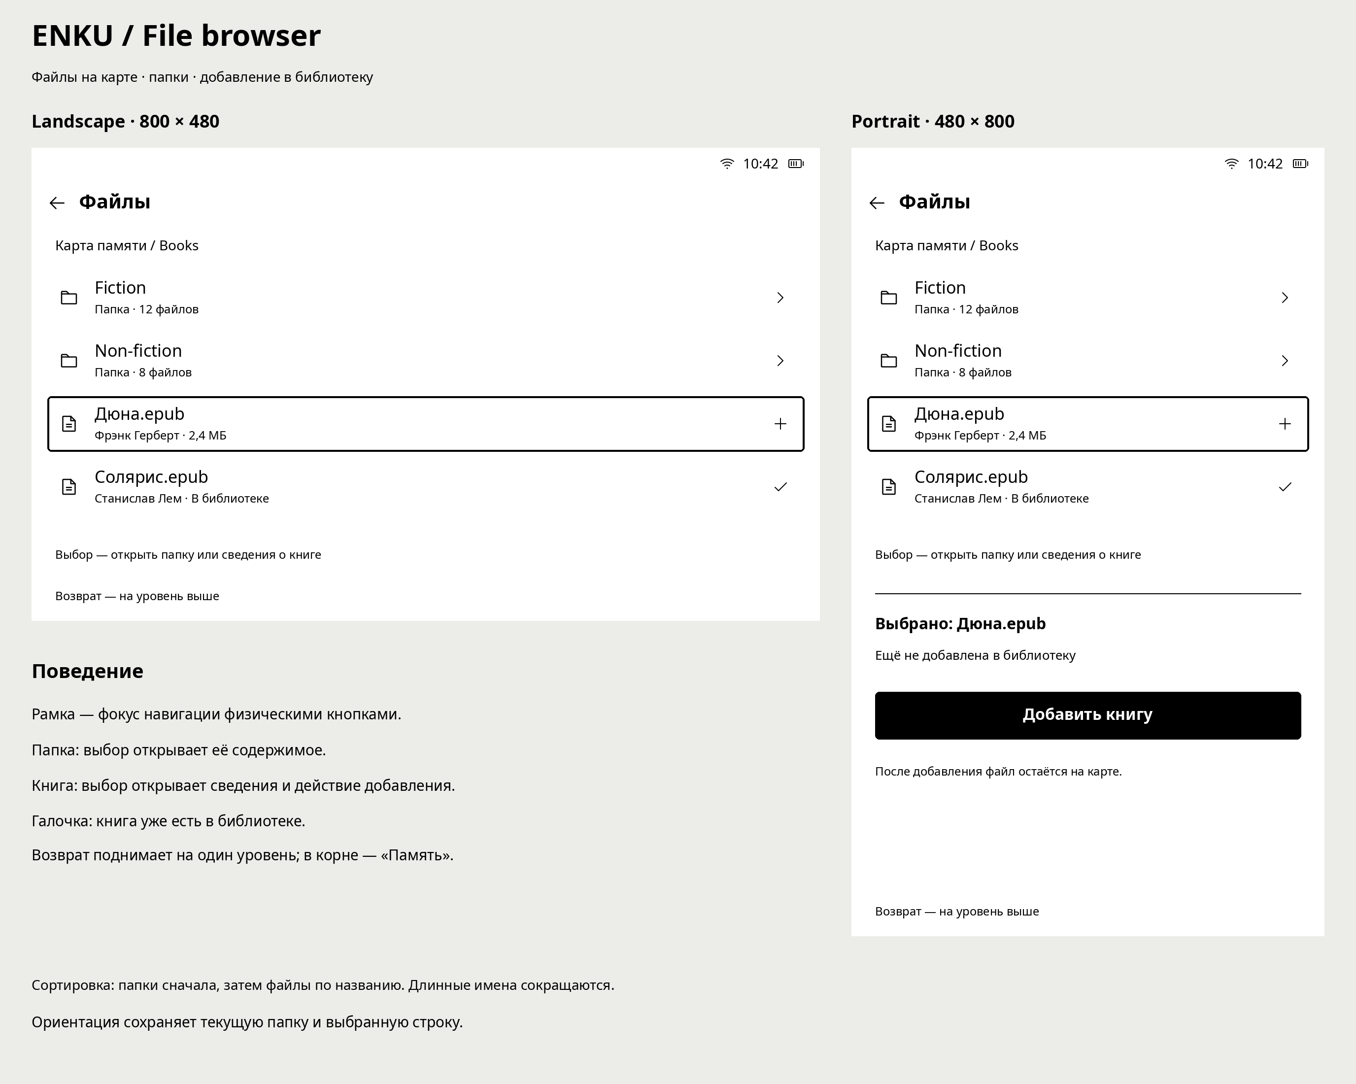
design/screens/ru/ENKU_file_browser_v1.png
