raznoglaz1y/enku/design/screens/ru/ENKU_filter_sort_v1.png

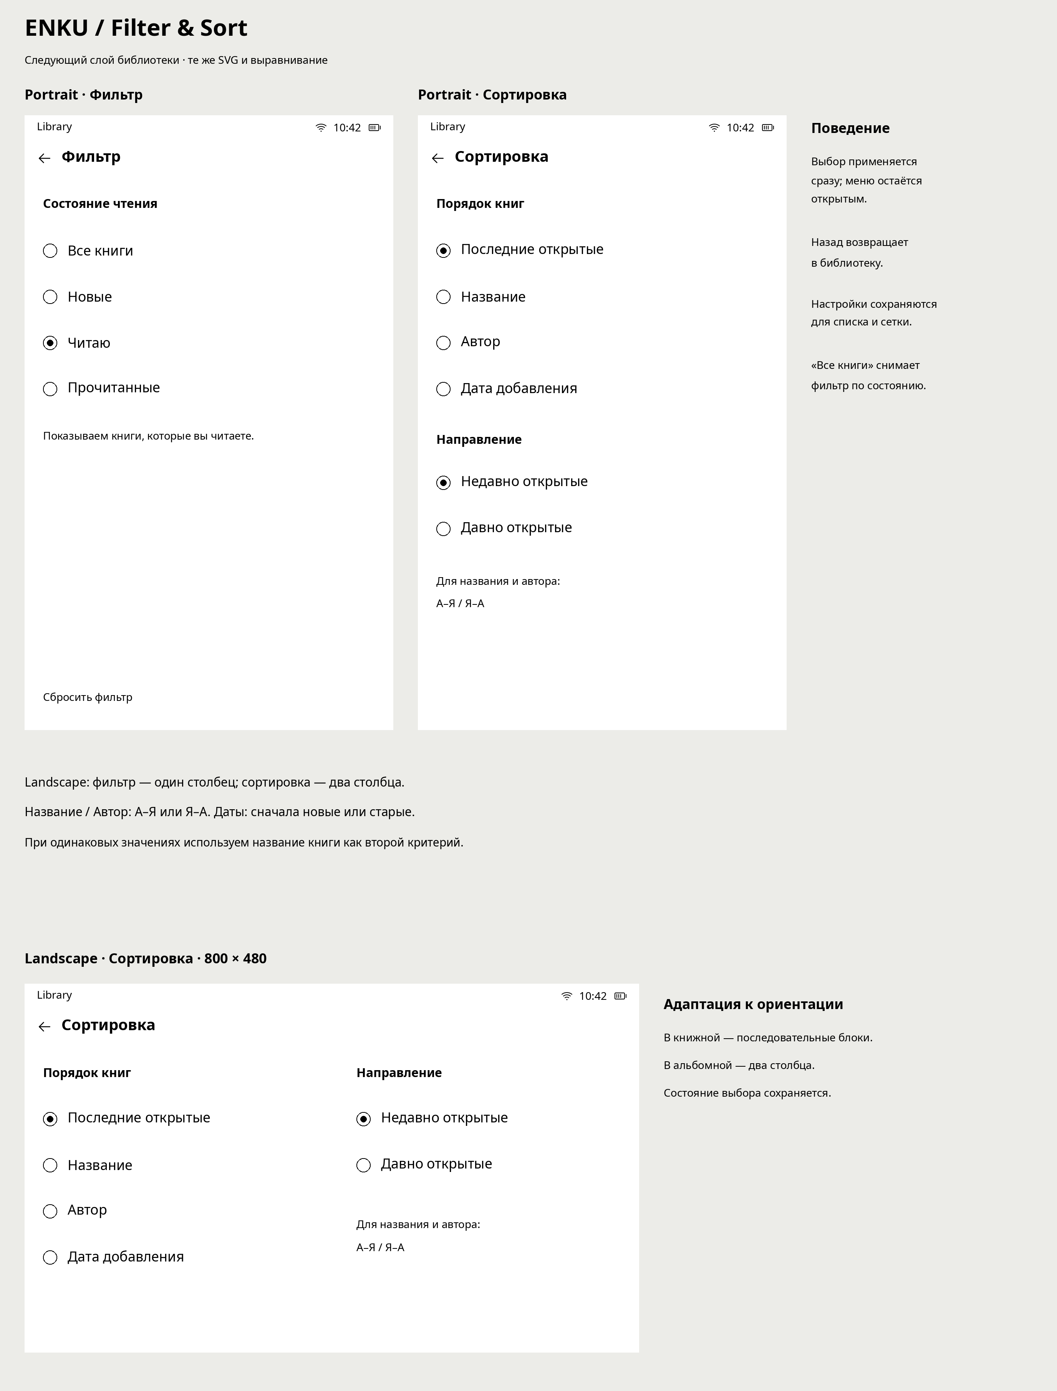
design/screens/ru/ENKU_filter_sort_v1.png
