raznoglaz1y/enku/design/screens/ru/ENKU_first_start_controls_v1.png

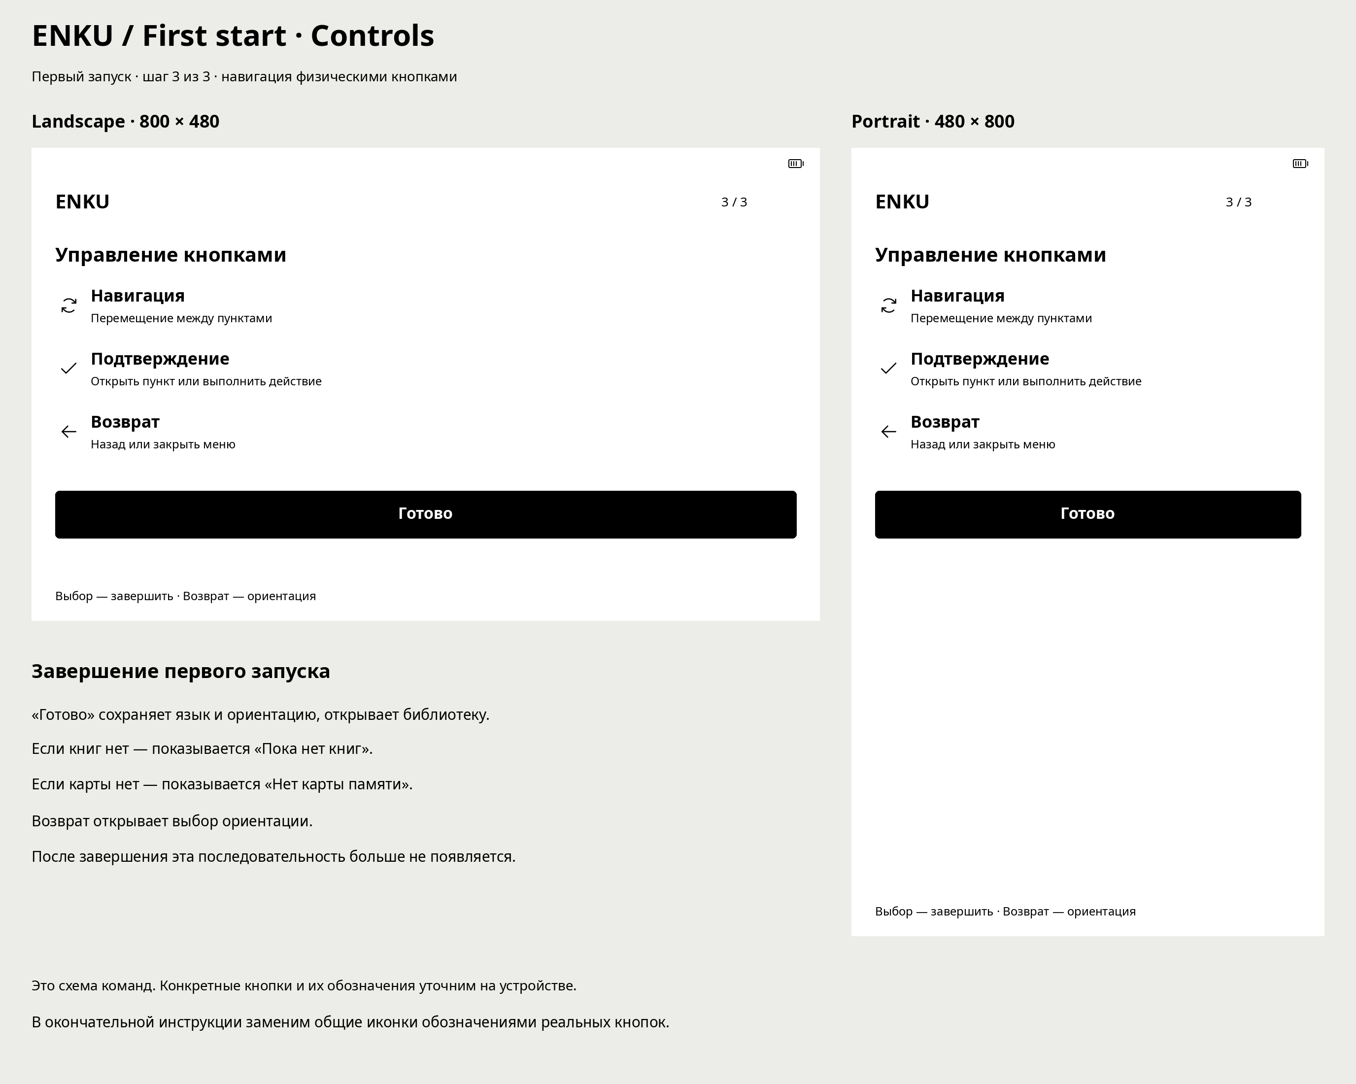
design/screens/ru/ENKU_first_start_controls_v1.png
