raznoglaz1y/enku/design/screens/ru/ENKU_first_start_language_v1.png

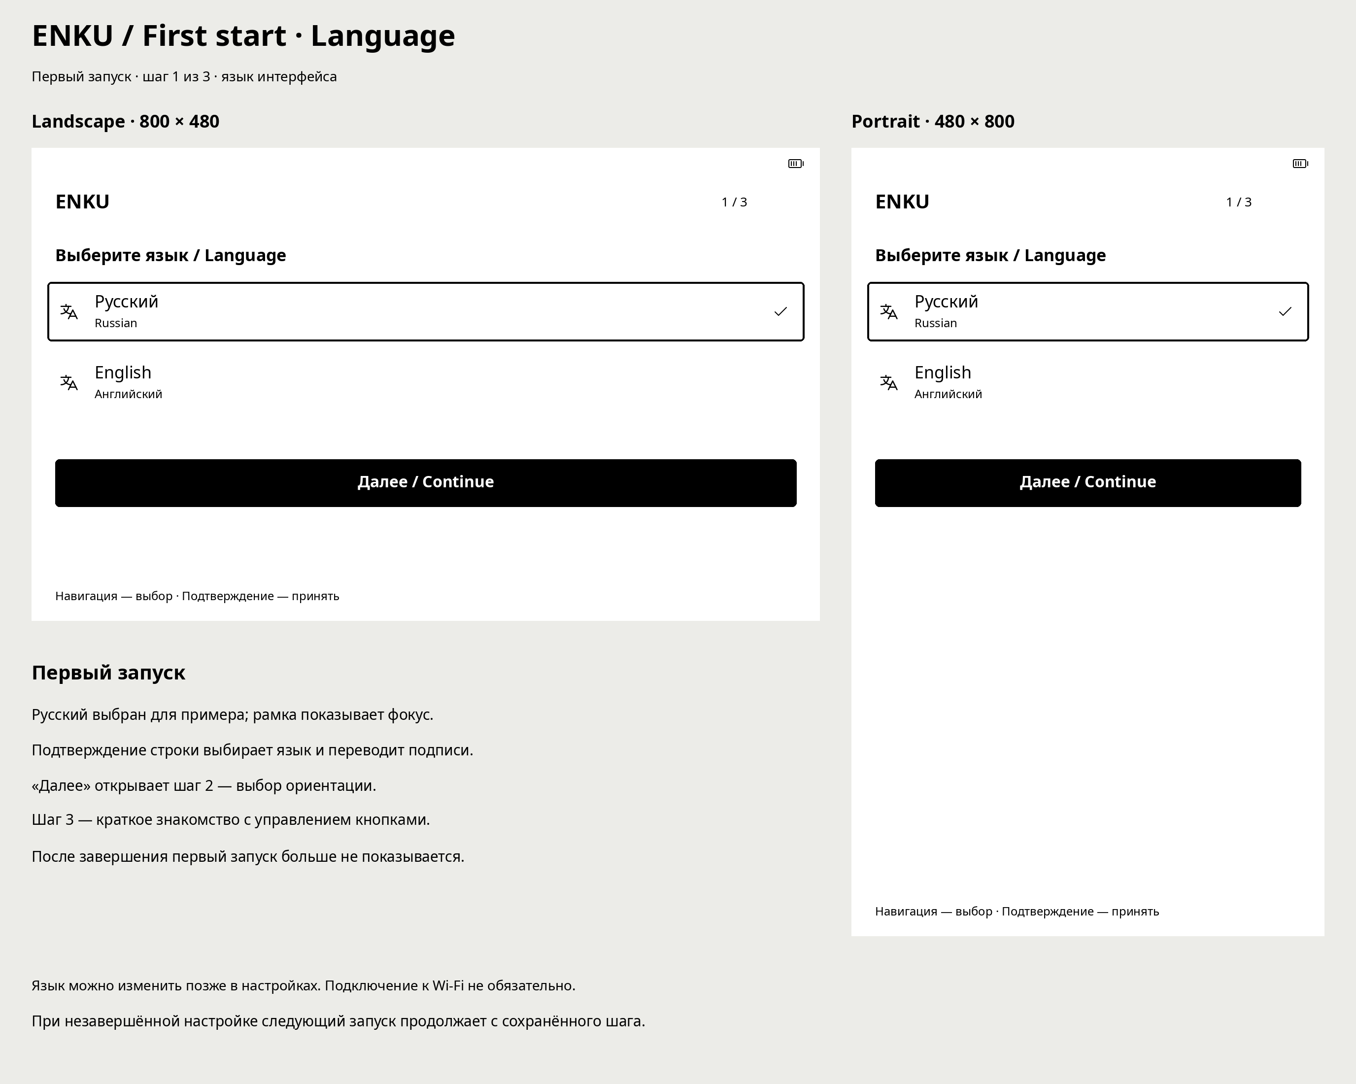
design/screens/ru/ENKU_first_start_language_v1.png
