raznoglaz1y/enku/design/screens/ru/ENKU_focus_states_v1.png

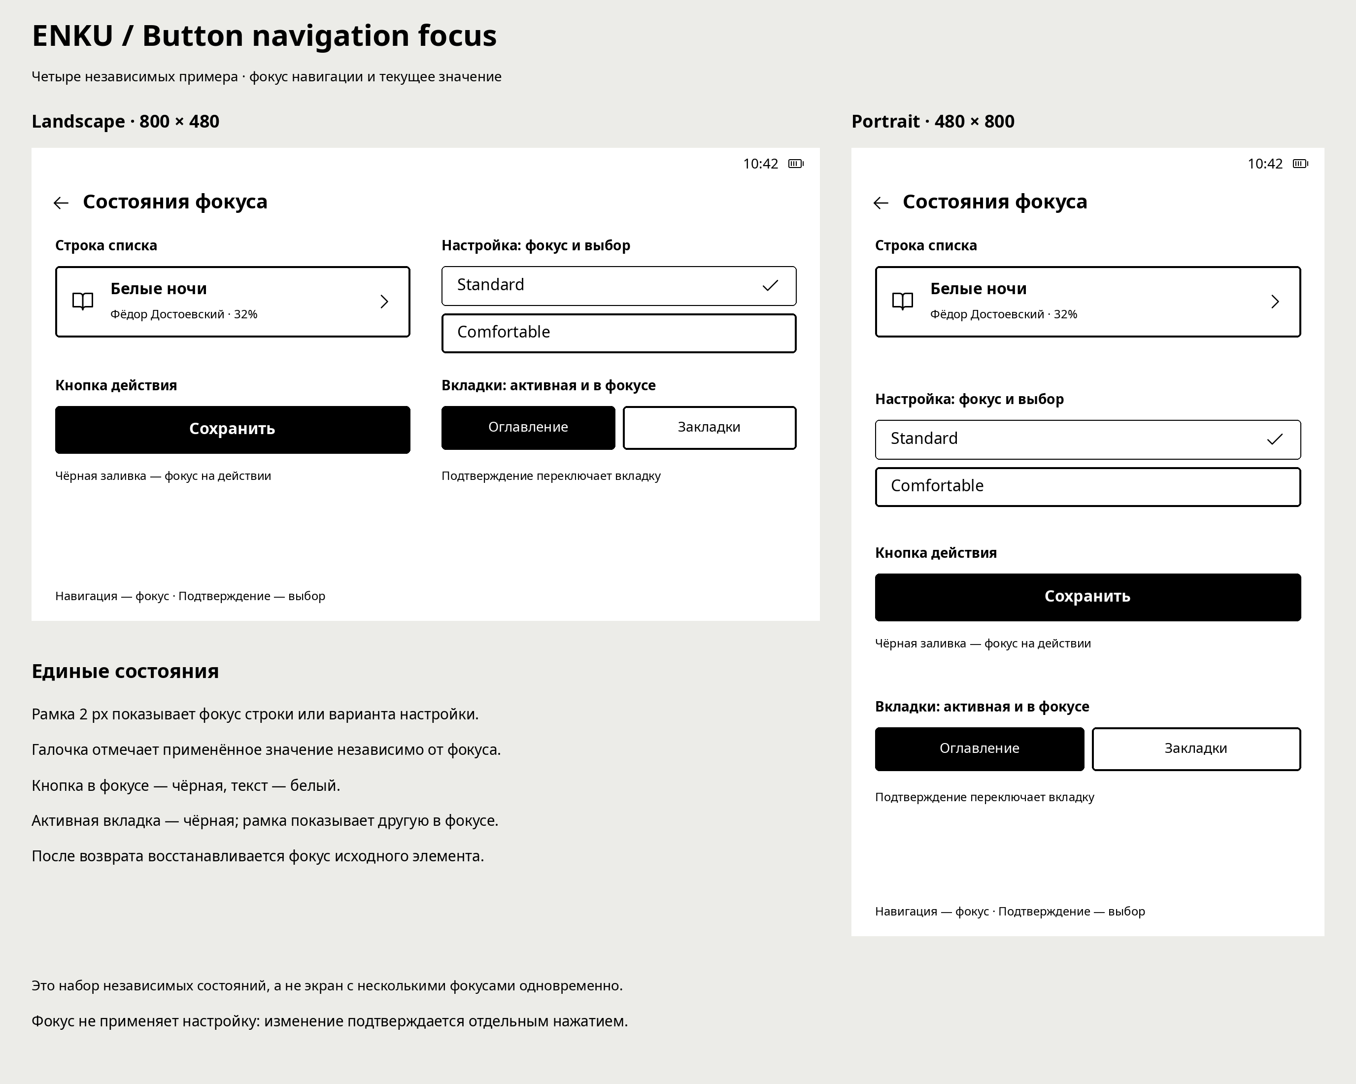
design/screens/ru/ENKU_focus_states_v1.png
