raznoglaz1y/enku/design/screens/ru/ENKU_forget_network_v1.png

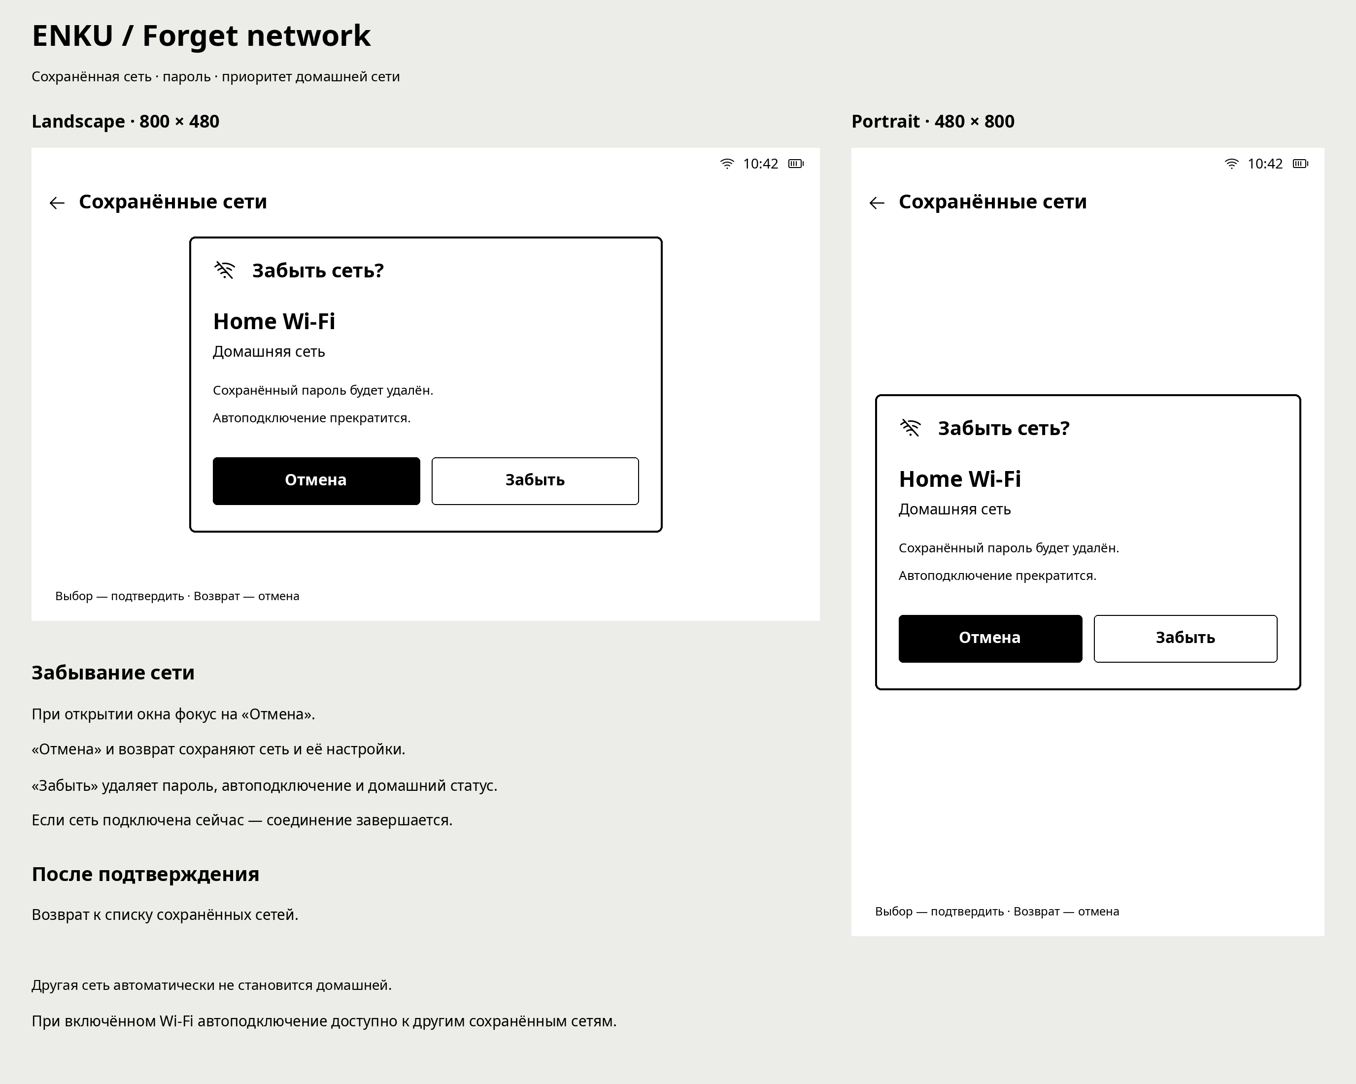
design/screens/ru/ENKU_forget_network_v1.png
