raznoglaz1y/enku/design/screens/ru/ENKU_import_methods_v1.png

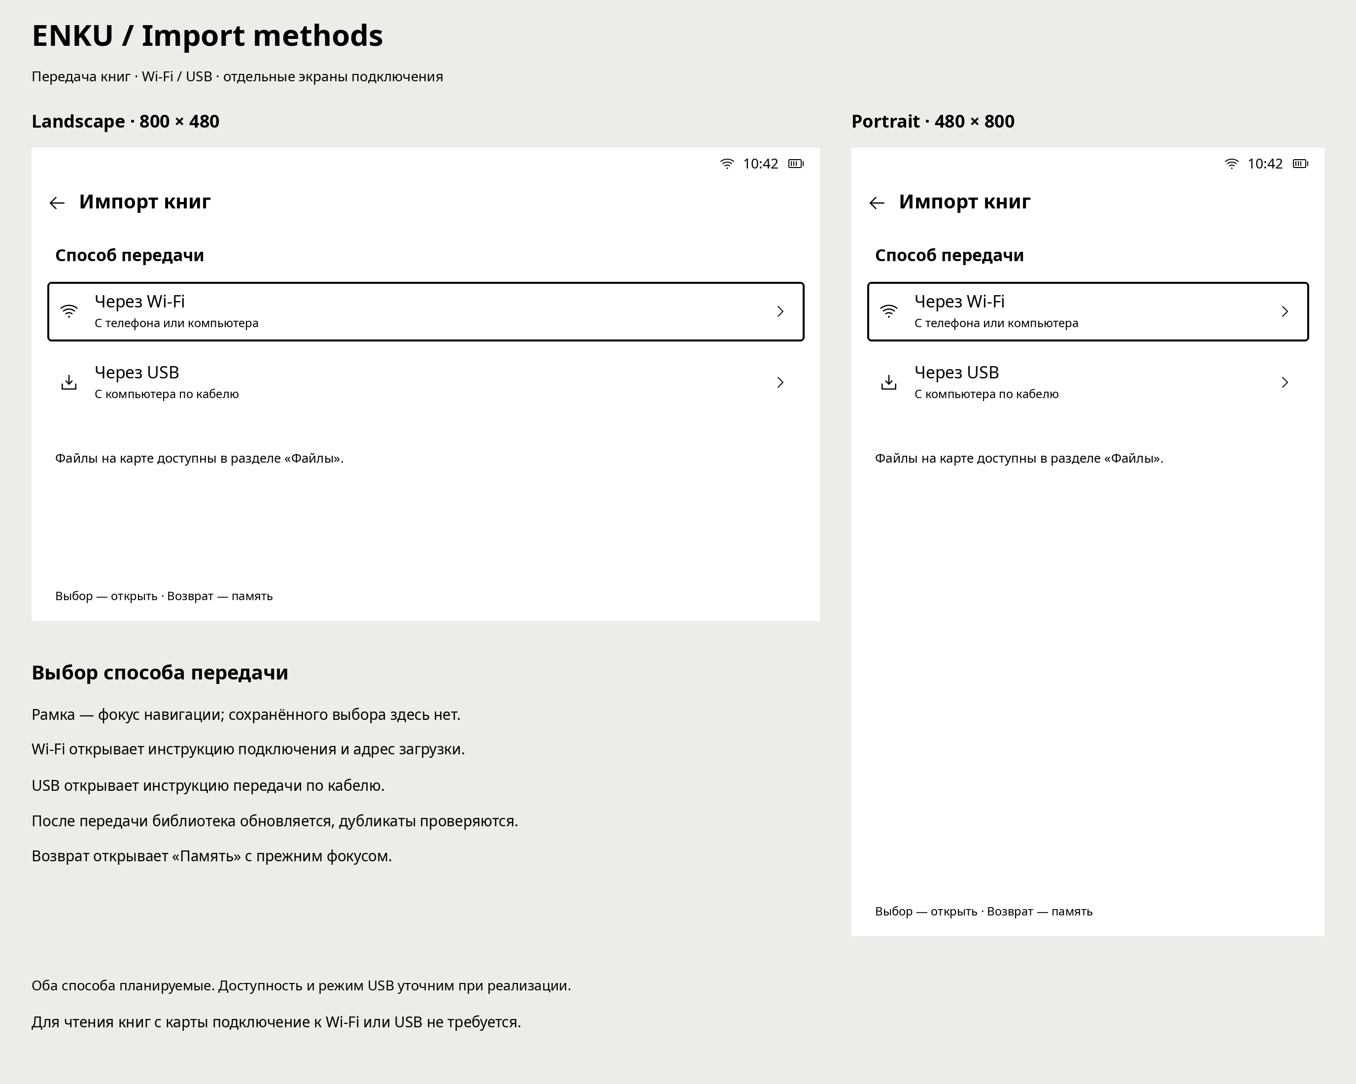
design/screens/ru/ENKU_import_methods_v1.png
