raznoglaz1y/enku/design/screens/ru/ENKU_library_search_v1.png

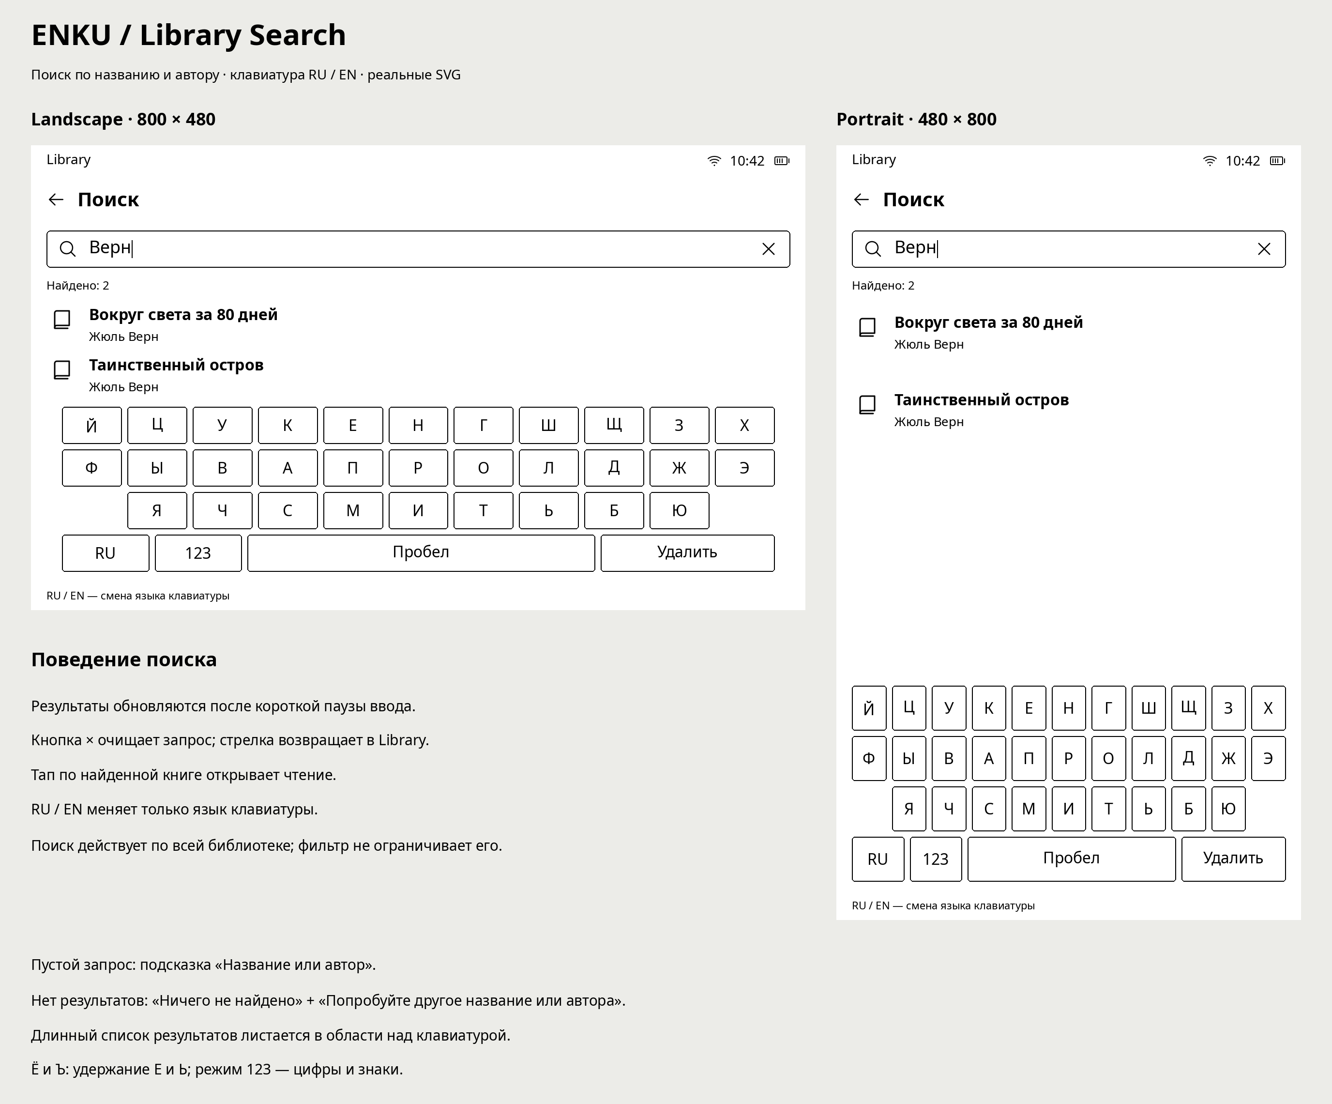
design/screens/ru/ENKU_library_search_v1.png
