raznoglaz1y/enku/design/screens/ru/ENKU_library_v1.png

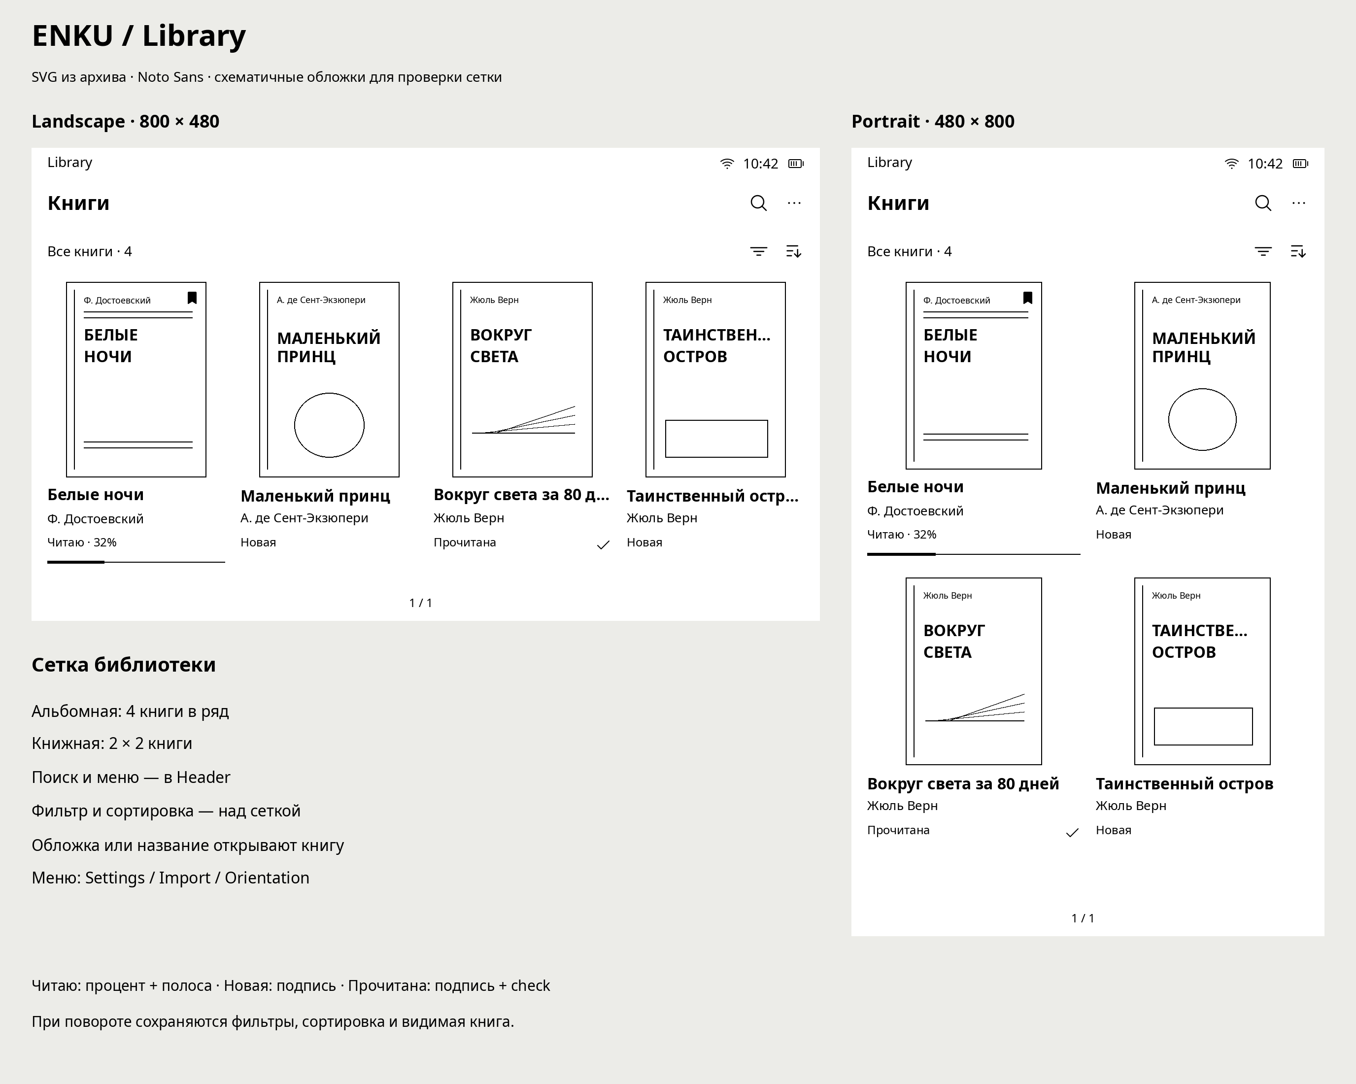
design/screens/ru/ENKU_library_v1.png
