raznoglaz1y/enku/design/screens/ru/ENKU_long_text_check_v1.png

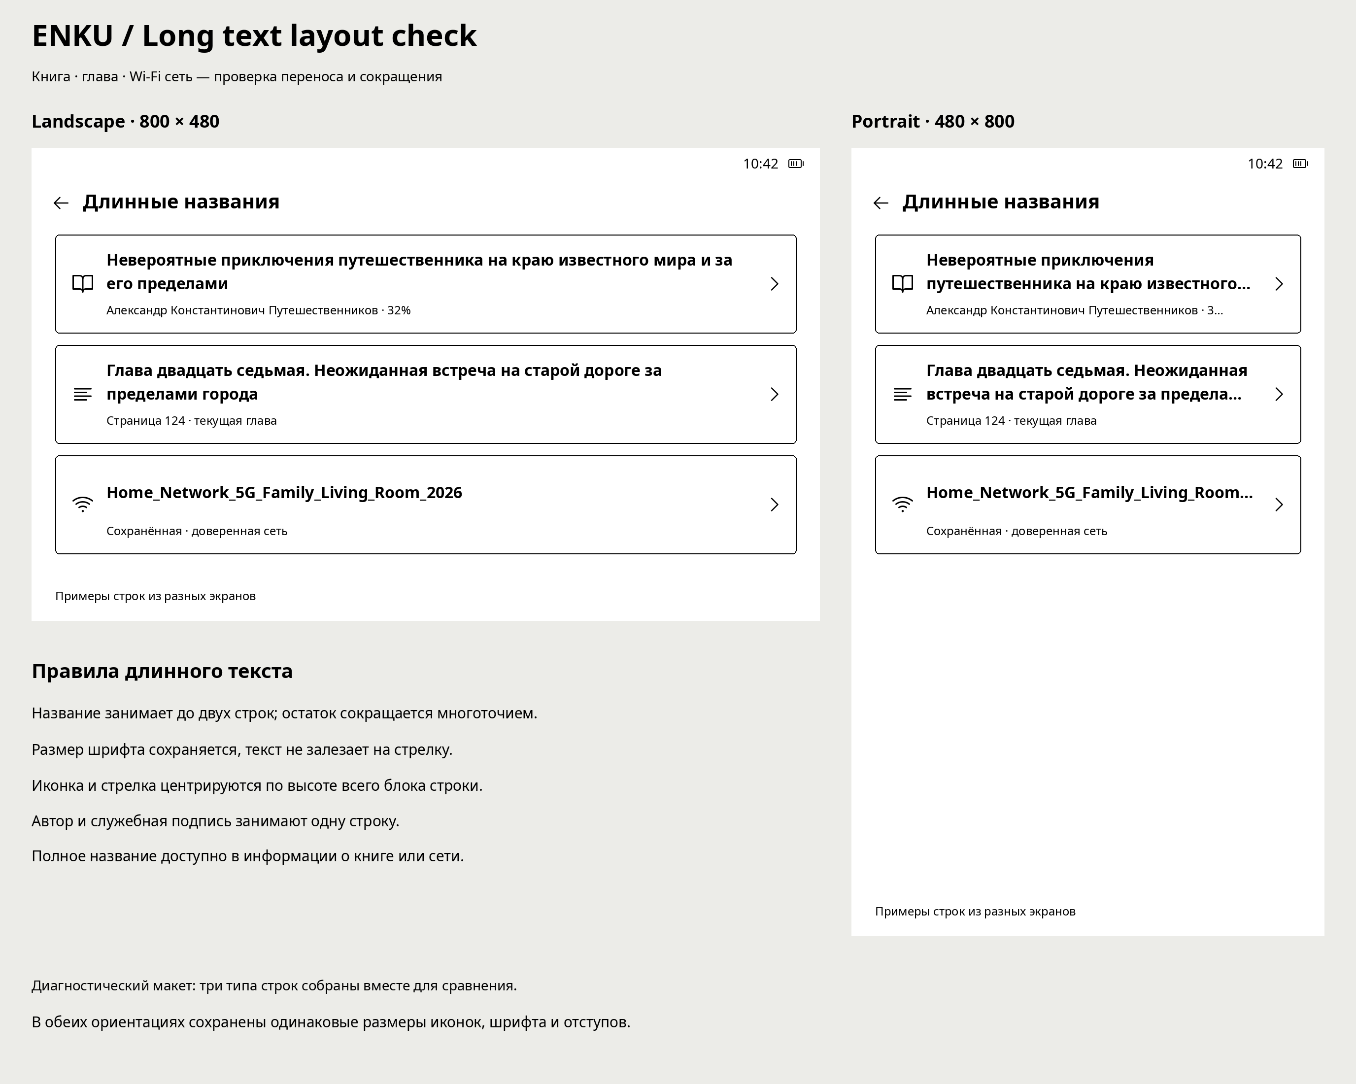
design/screens/ru/ENKU_long_text_check_v1.png
