raznoglaz1y/enku/design/screens/ru/ENKU_navigation_status_v2.png

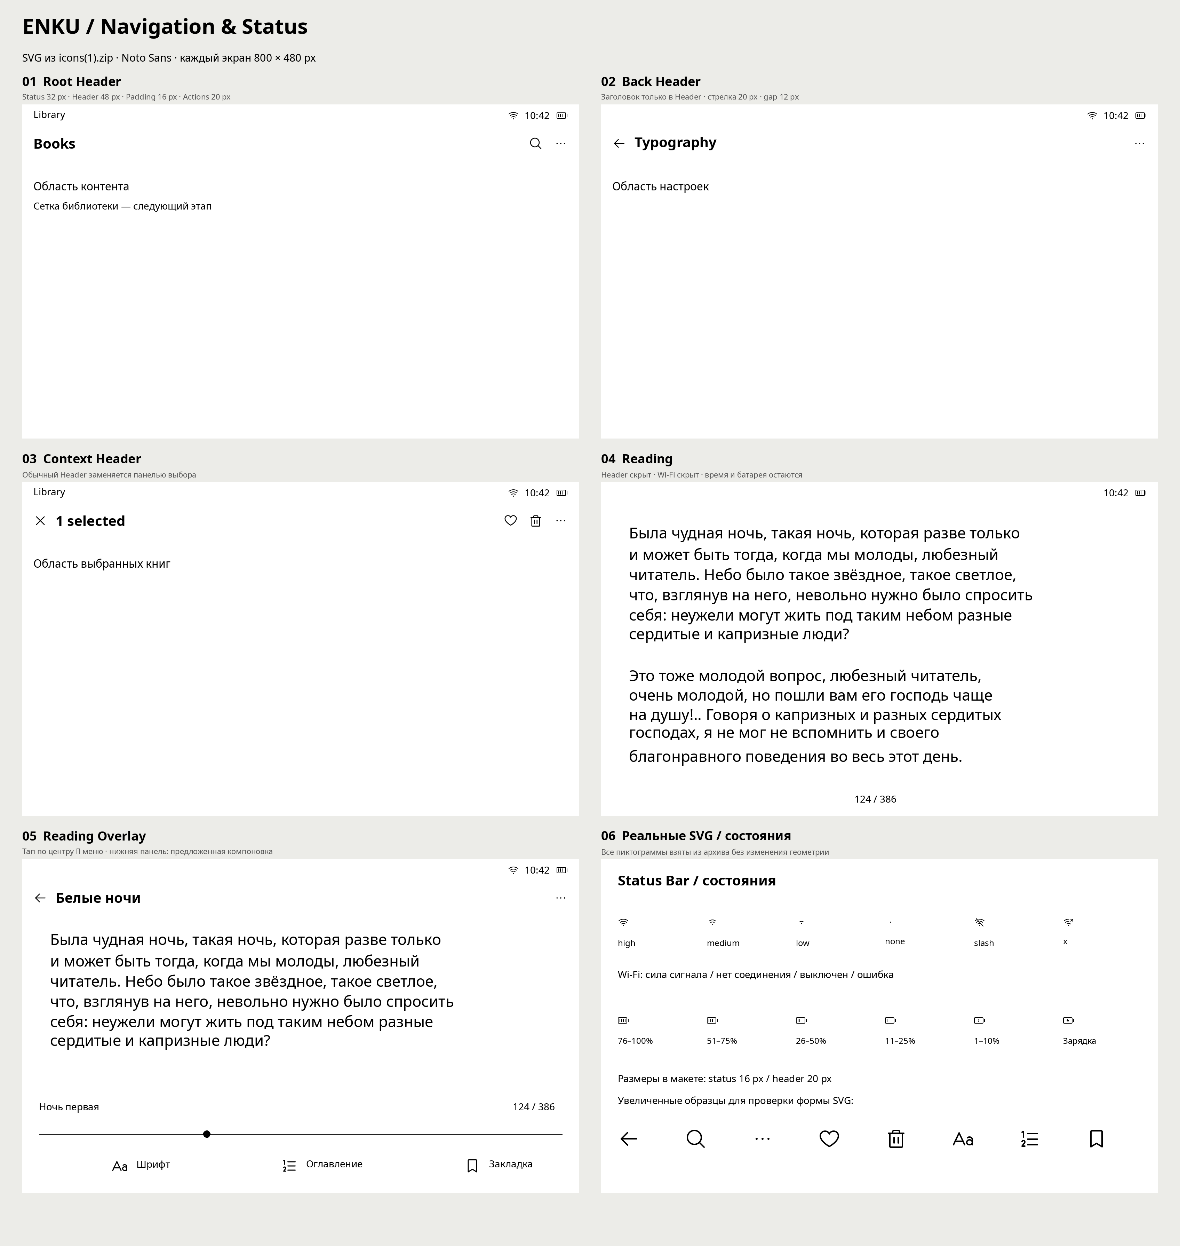
design/screens/ru/ENKU_navigation_status_v2.png
