raznoglaz1y/enku/design/screens/ru/ENKU_no_contents_v1.png

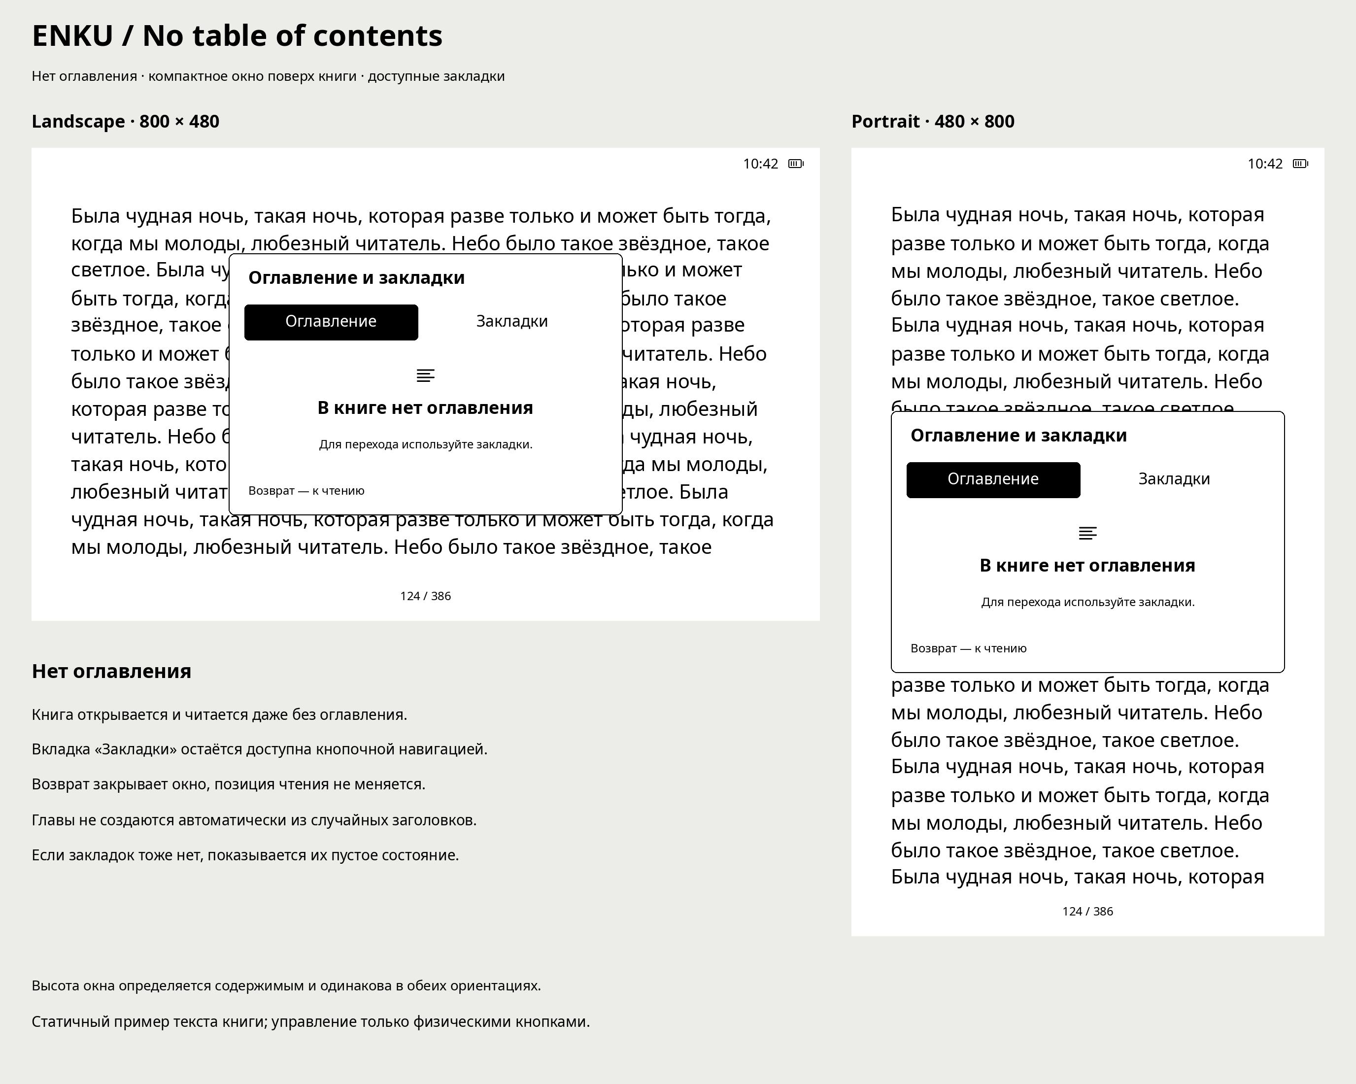
design/screens/ru/ENKU_no_contents_v1.png
