raznoglaz1y/enku/design/screens/ru/ENKU_not_enough_space_v1.png

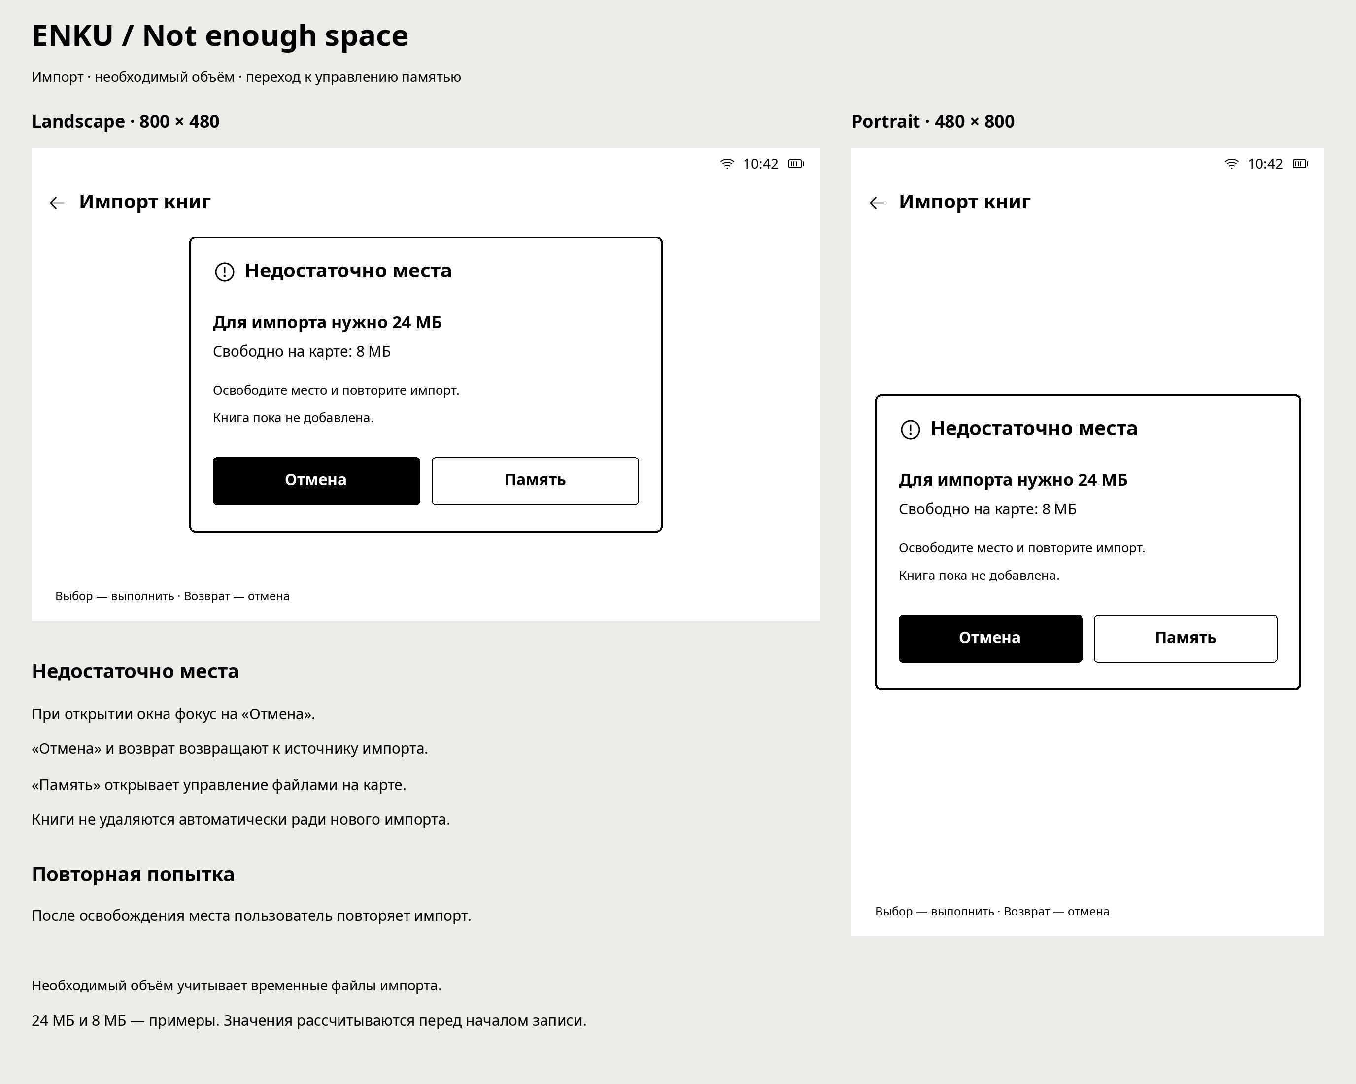
design/screens/ru/ENKU_not_enough_space_v1.png
