raznoglaz1y/enku/design/screens/ru/ENKU_portrait_orientation_v2.png

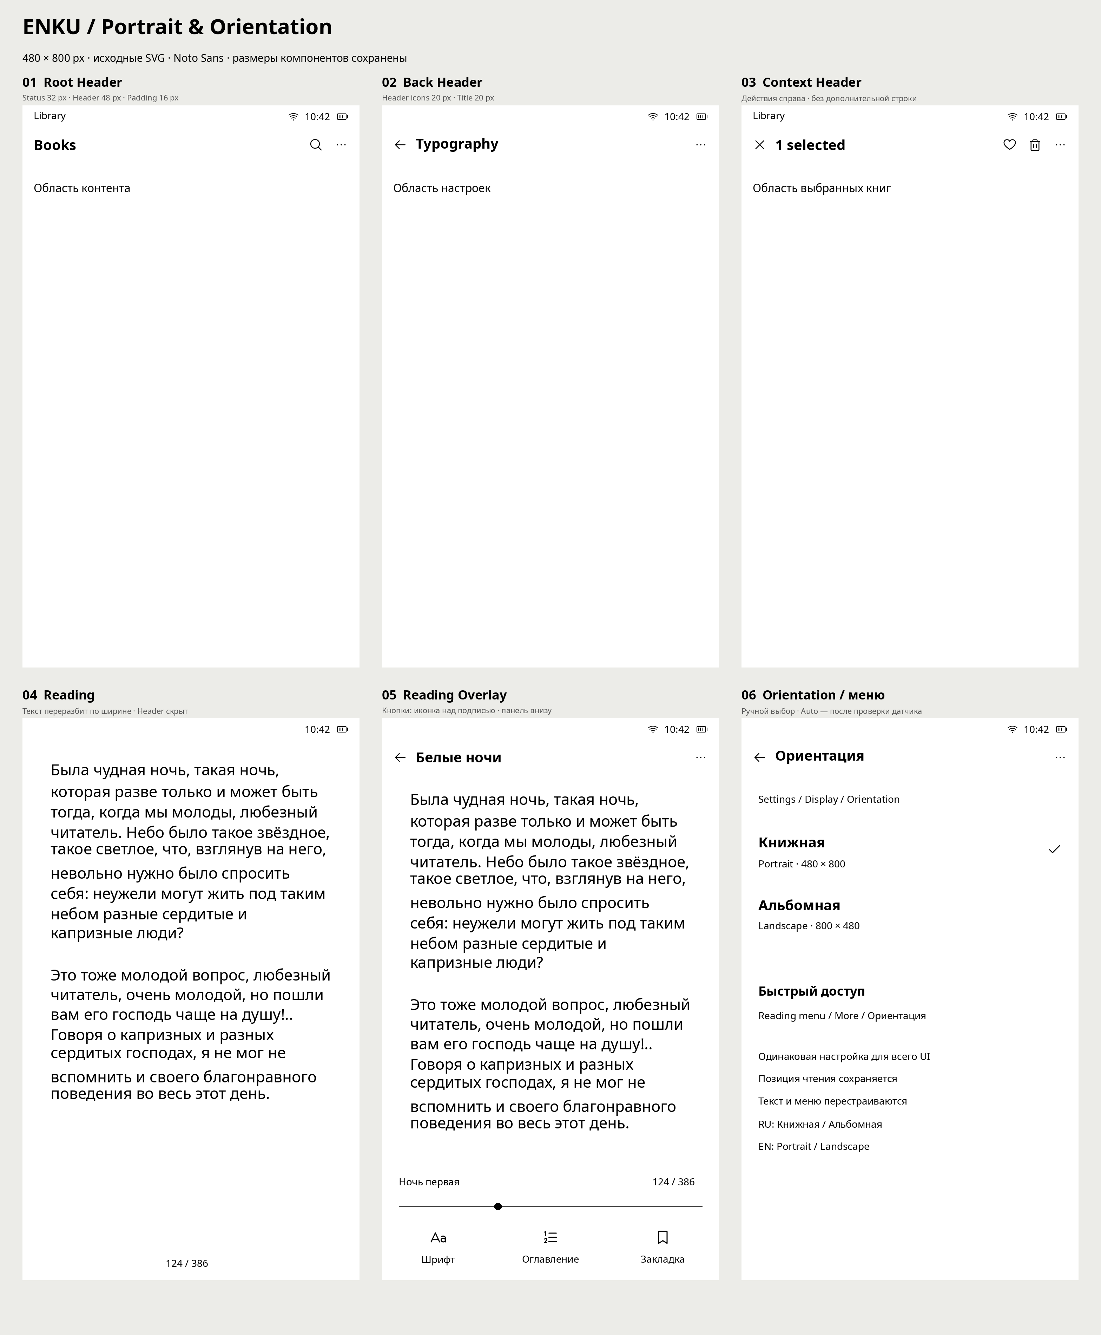
design/screens/ru/ENKU_portrait_orientation_v2.png
