raznoglaz1y/enku/design/screens/ru/ENKU_quick_aa_preview_v3.png

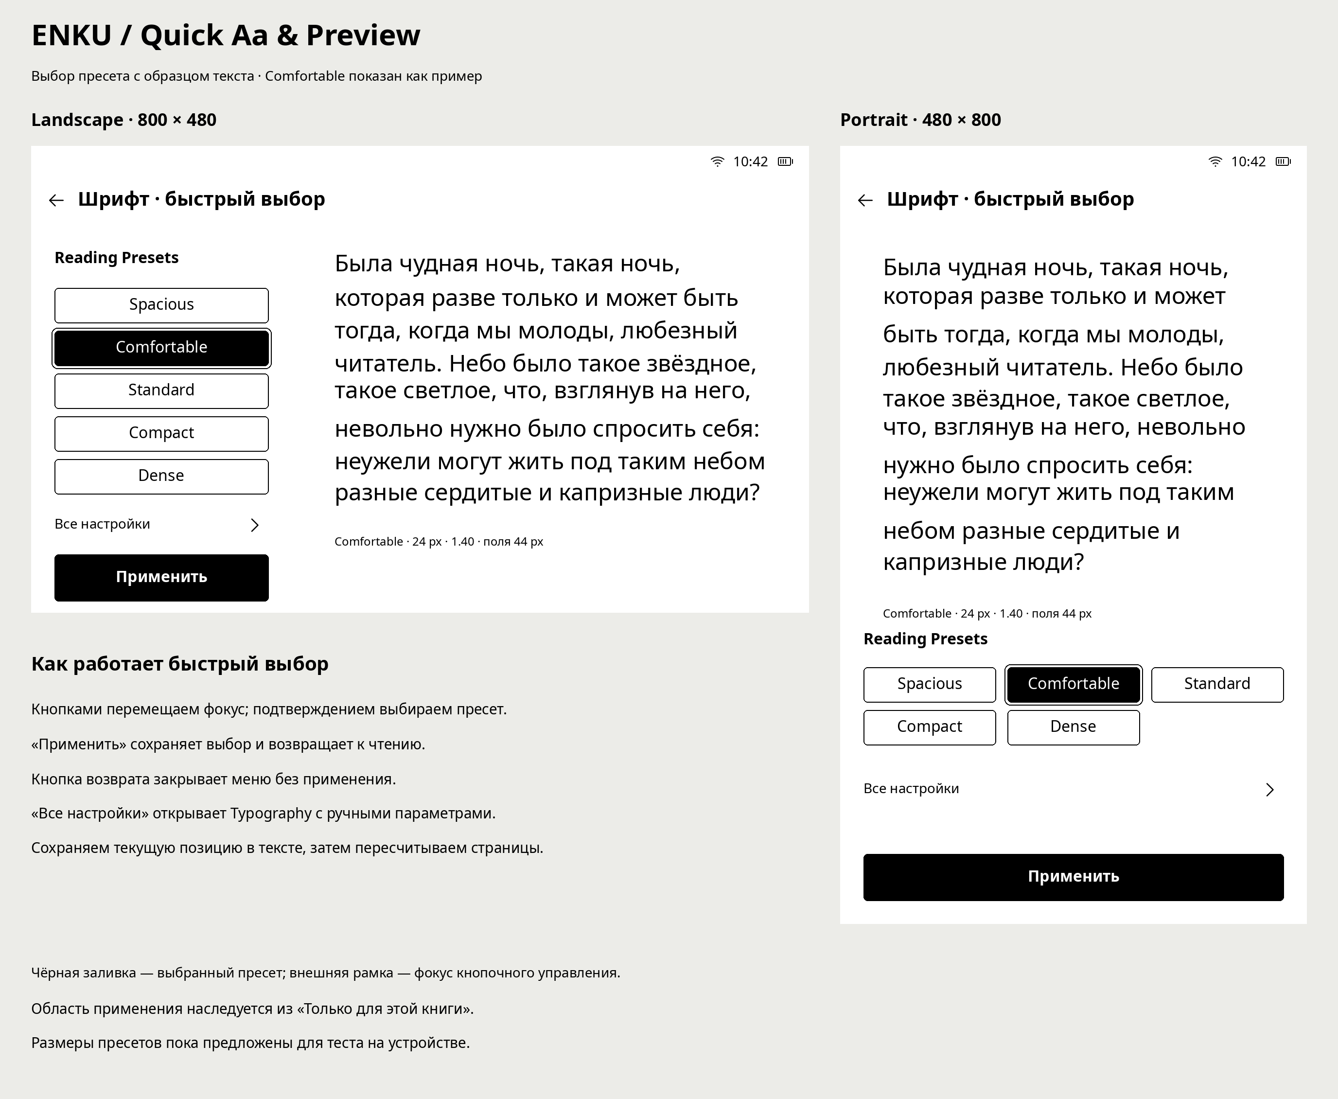
design/screens/ru/ENKU_quick_aa_preview_v3.png
