raznoglaz1y/enku/design/screens/ru/ENKU_restart_reading_v1.png

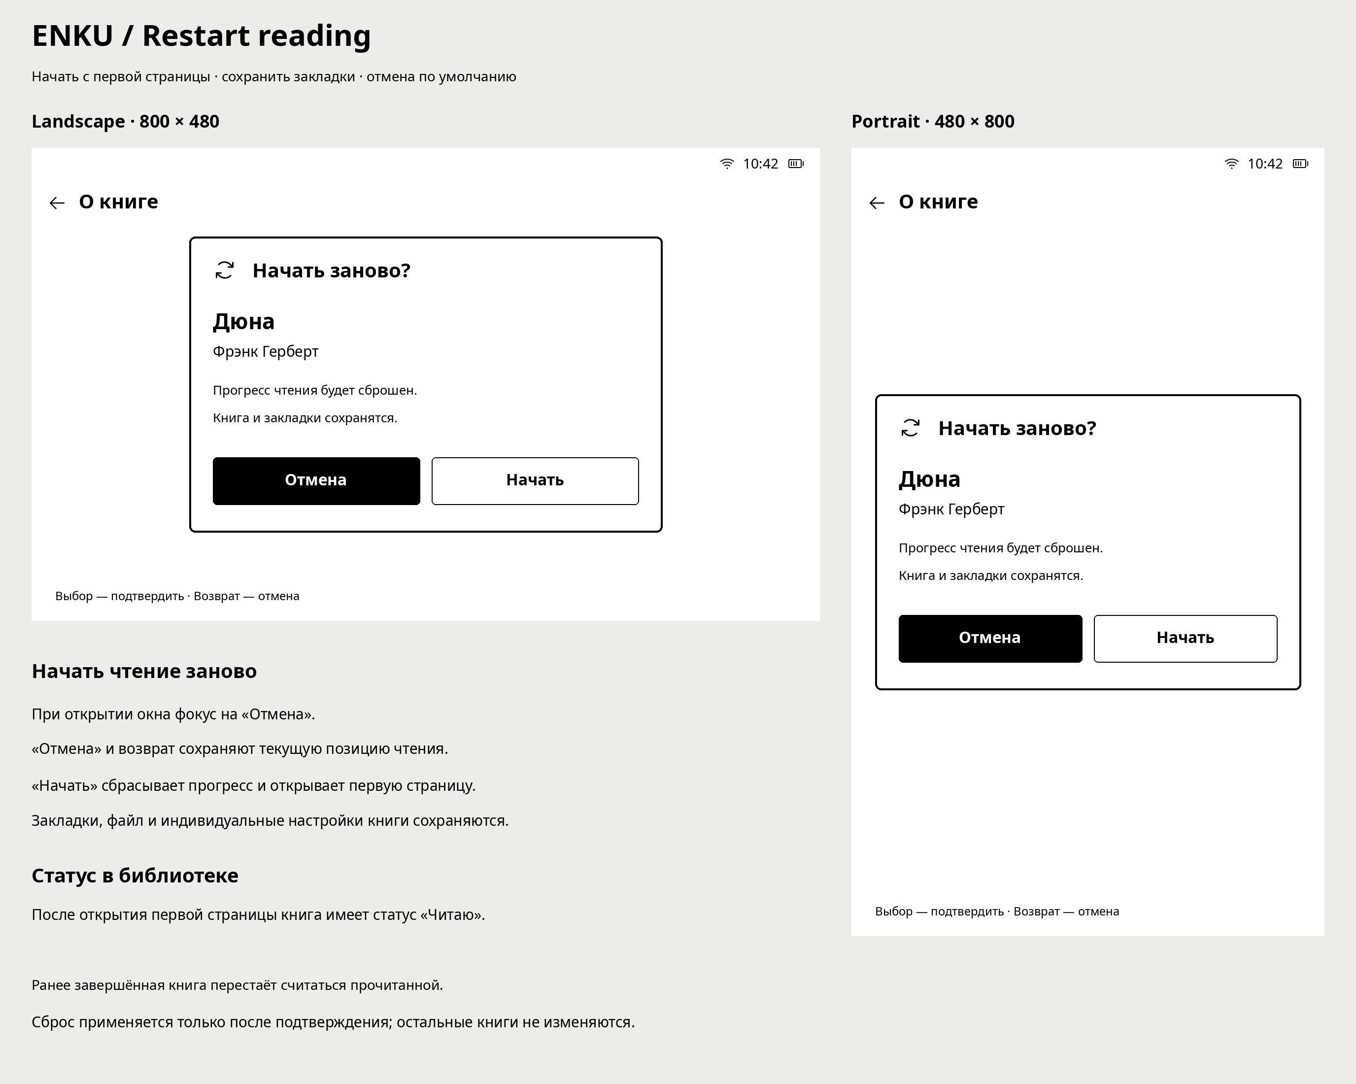
design/screens/ru/ENKU_restart_reading_v1.png
