raznoglaz1y/enku/design/screens/ru/ENKU_saved_networks_v1.png

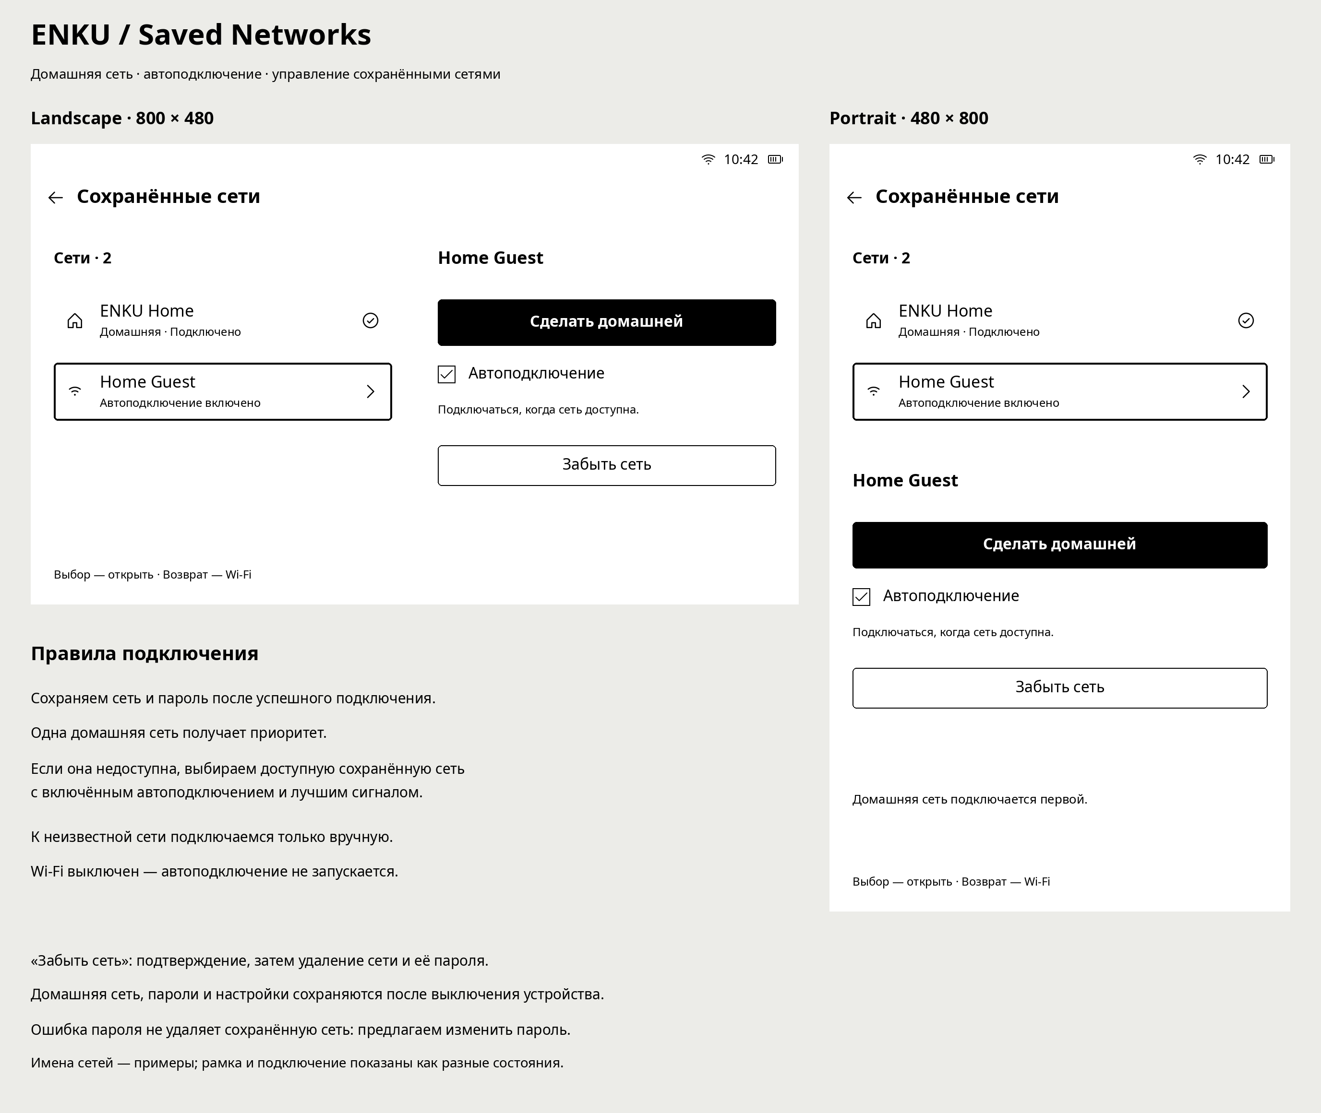
design/screens/ru/ENKU_saved_networks_v1.png
