raznoglaz1y/enku/design/screens/ru/ENKU_search_in_book_v1.png

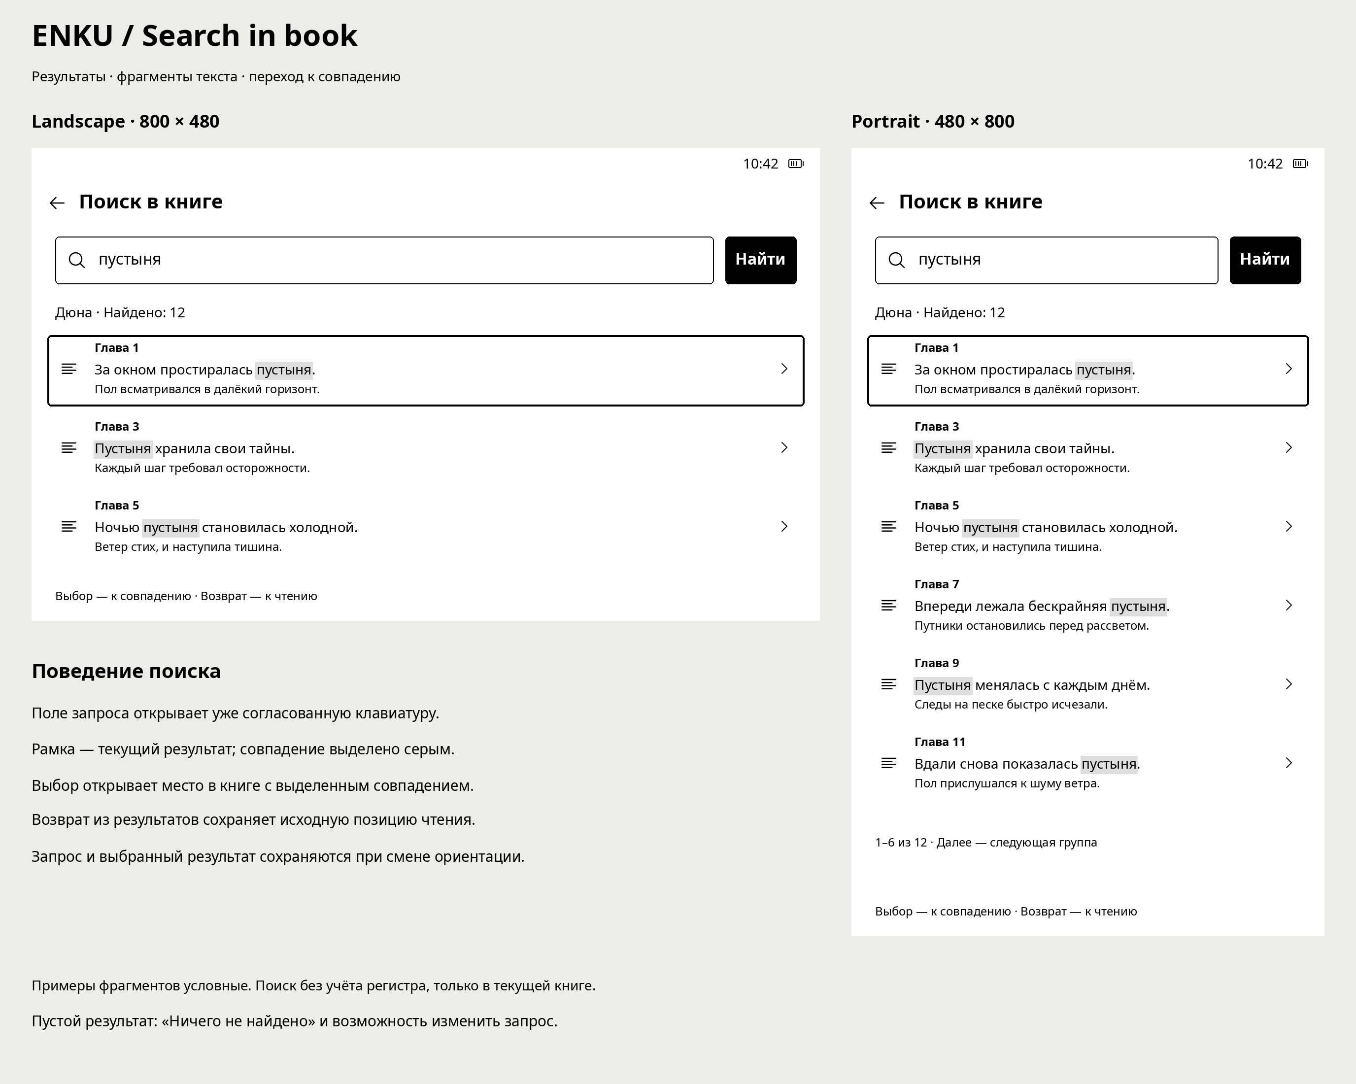
design/screens/ru/ENKU_search_in_book_v1.png
