raznoglaz1y/enku/design/screens/ru/ENKU_search_match_v1.png

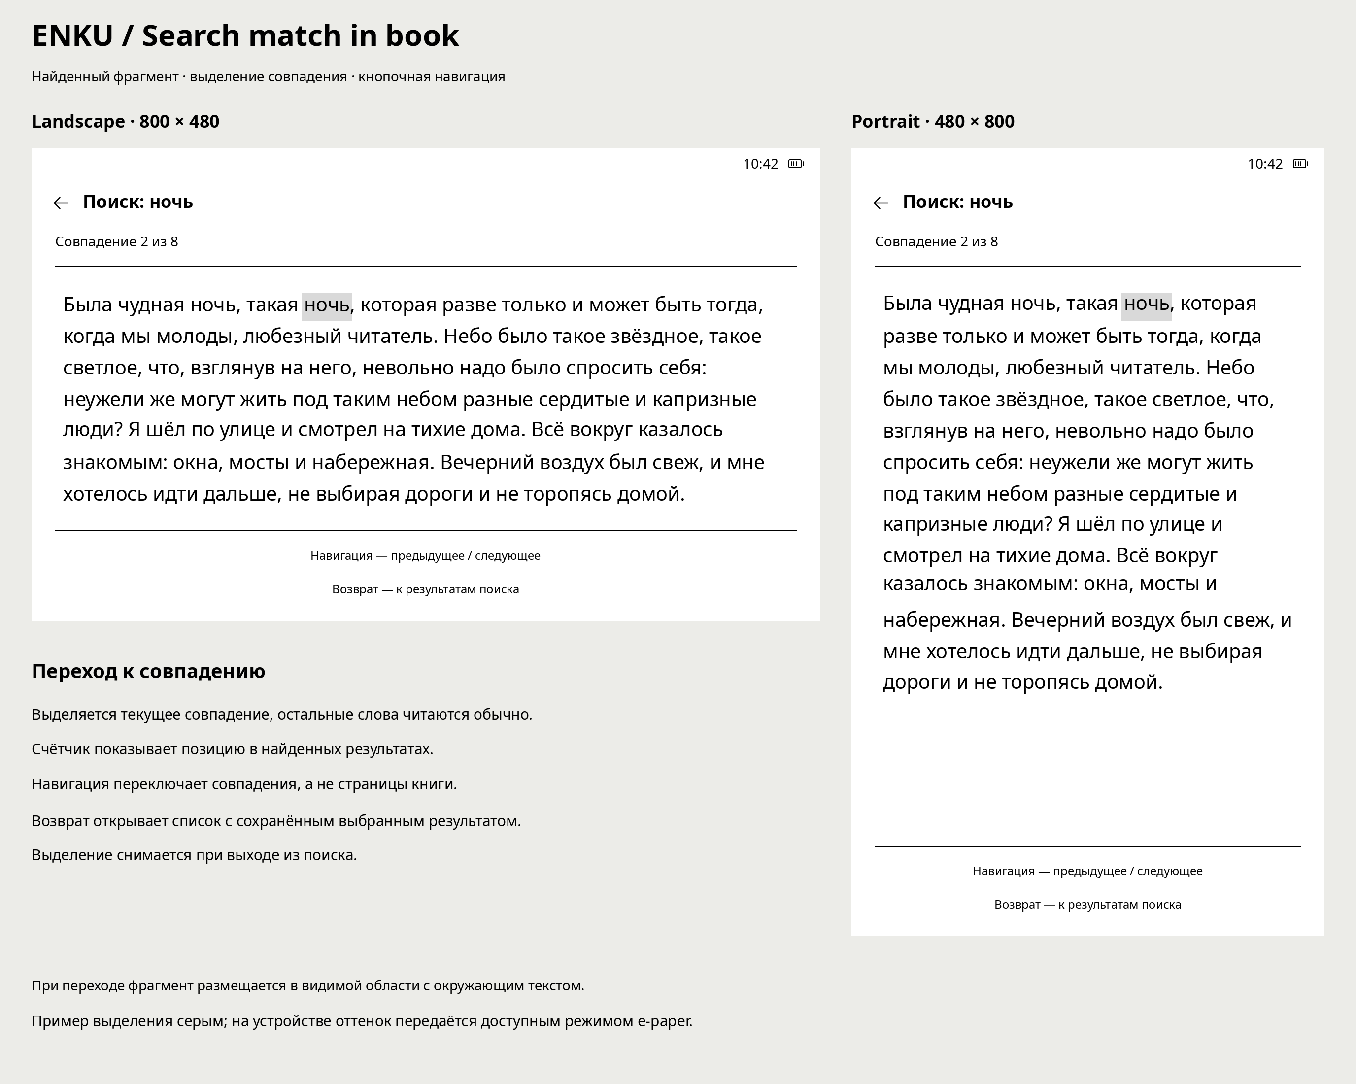
design/screens/ru/ENKU_search_match_v1.png
