raznoglaz1y/enku/design/screens/ru/ENKU_sleep_cover_v1.png

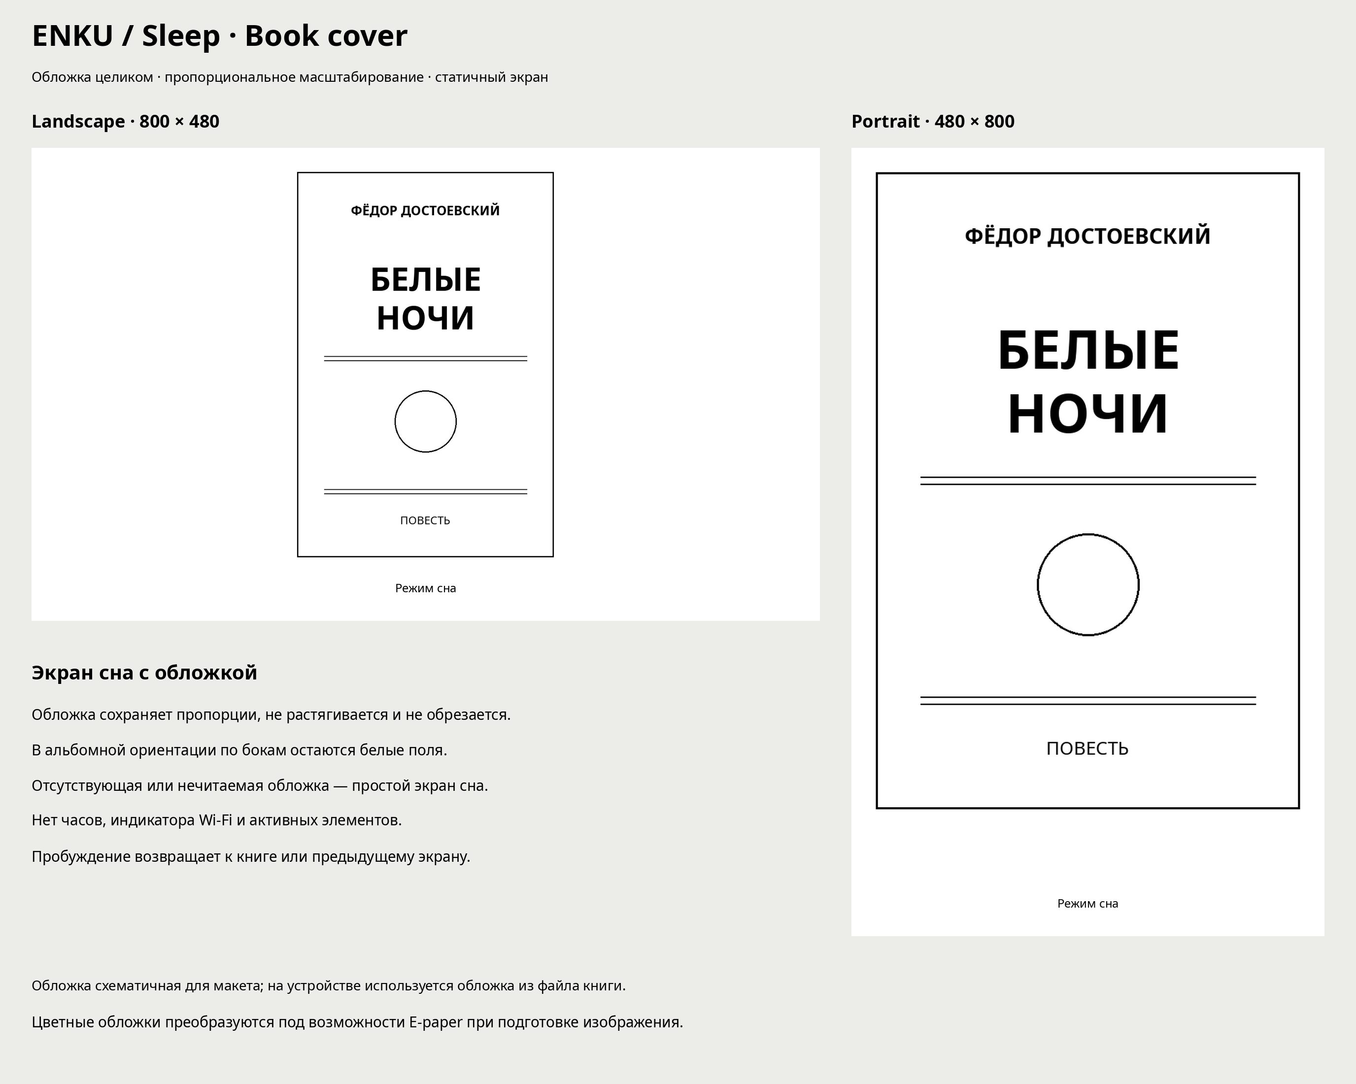
design/screens/ru/ENKU_sleep_cover_v1.png
