raznoglaz1y/enku/design/screens/ru/ENKU_storage_import_v1.png

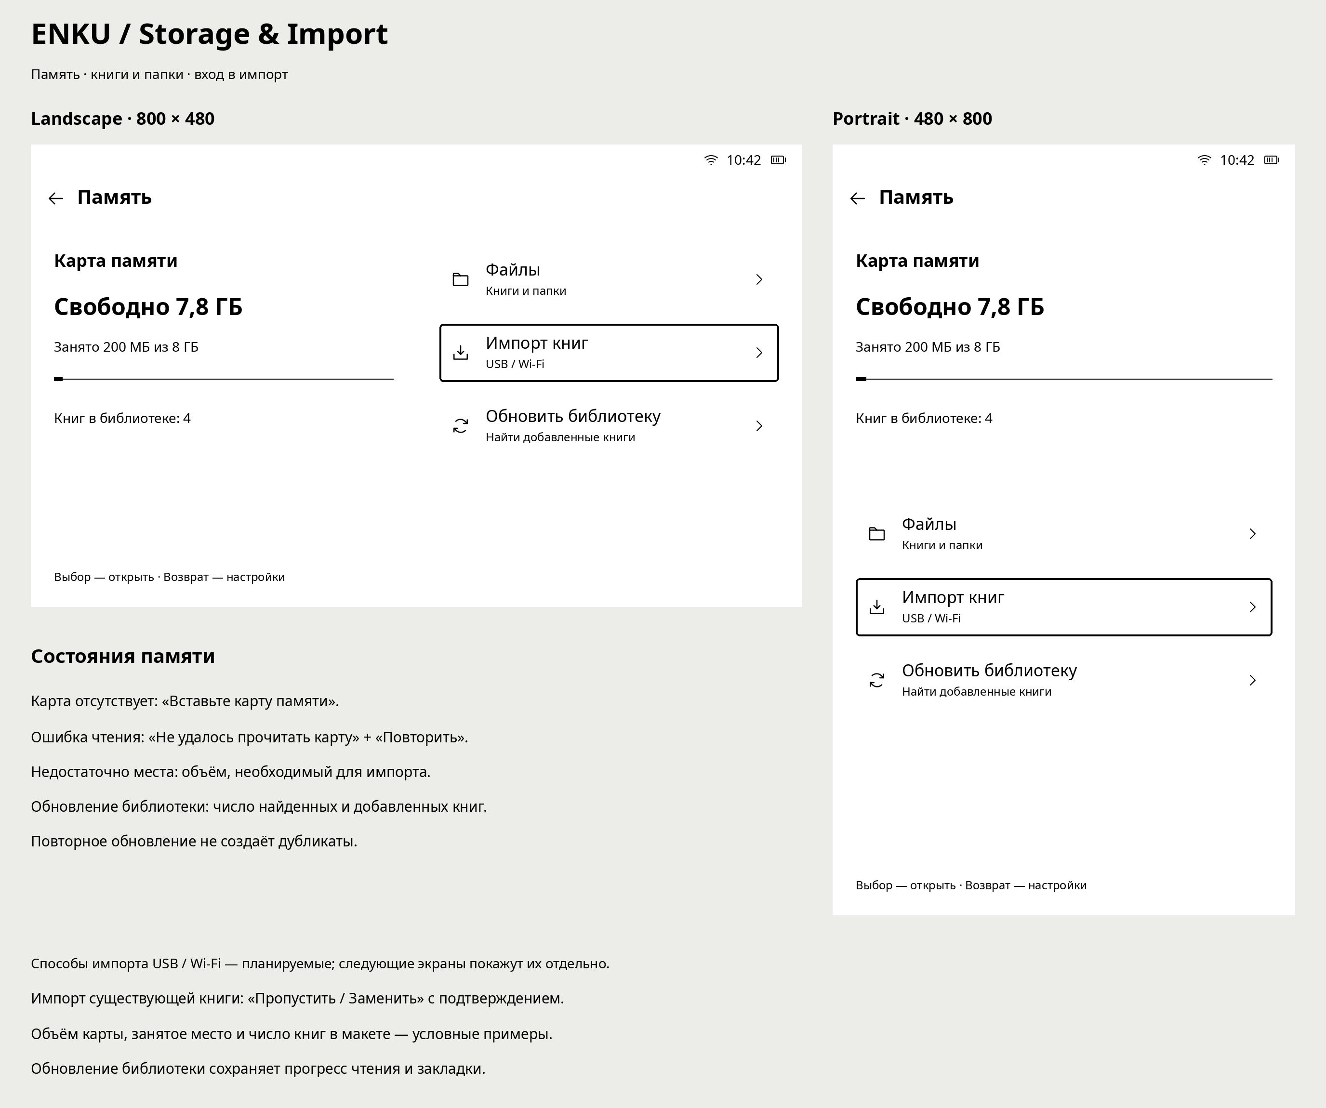
design/screens/ru/ENKU_storage_import_v1.png
