raznoglaz1y/enku/design/screens/ru/ENKU_transfer_progress_v2.png

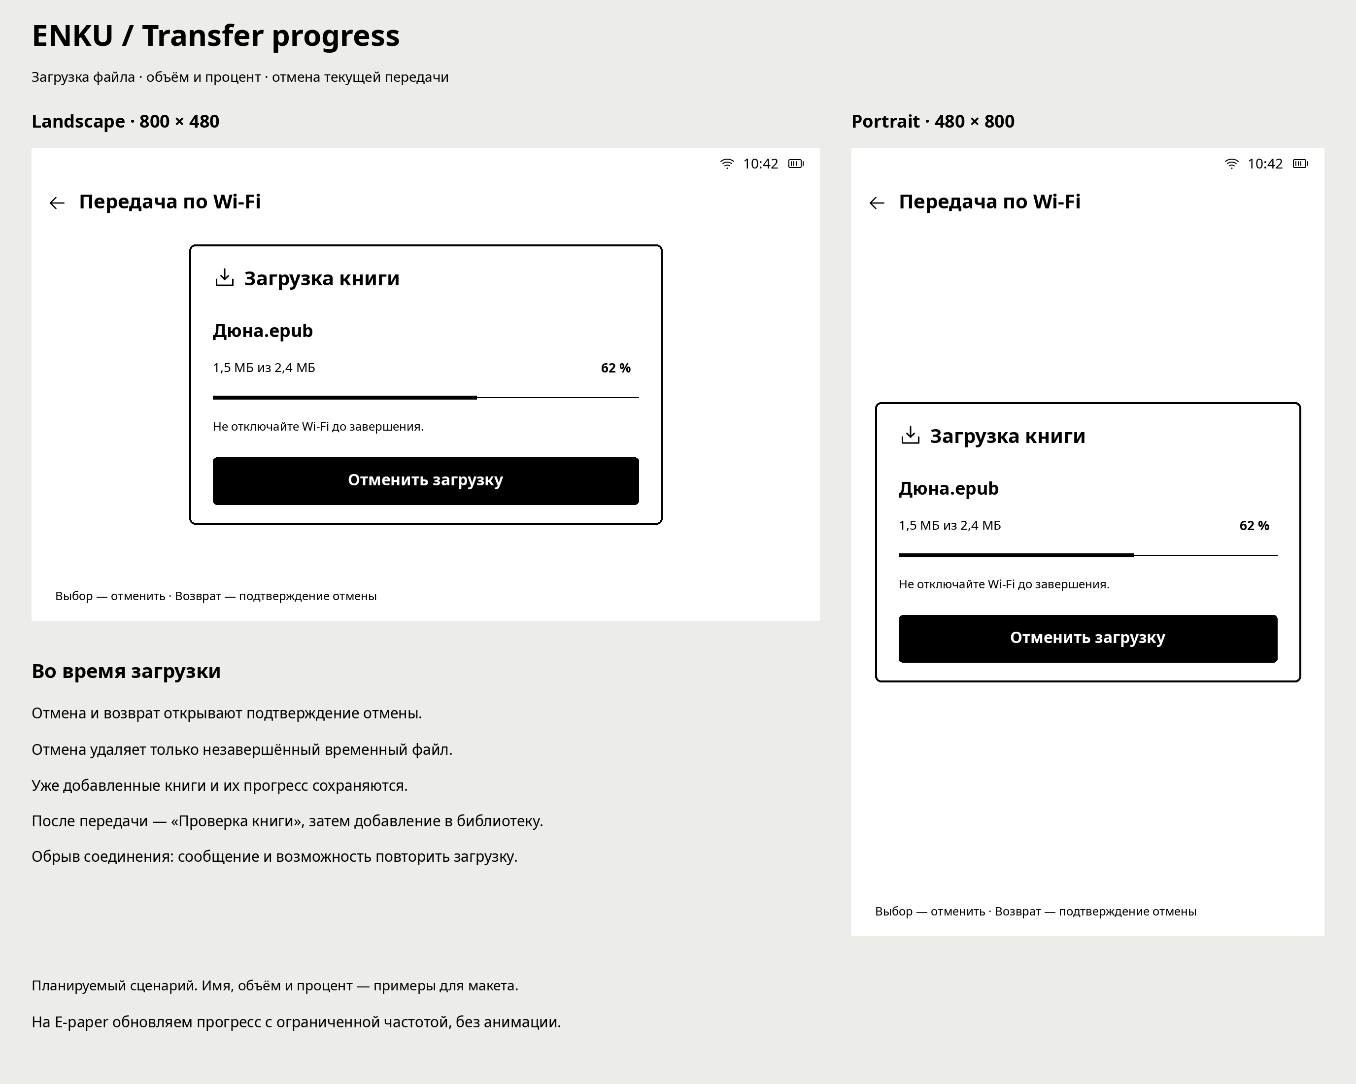
design/screens/ru/ENKU_transfer_progress_v2.png
