raznoglaz1y/enku/design/screens/ru/ENKU_typography_v1.png

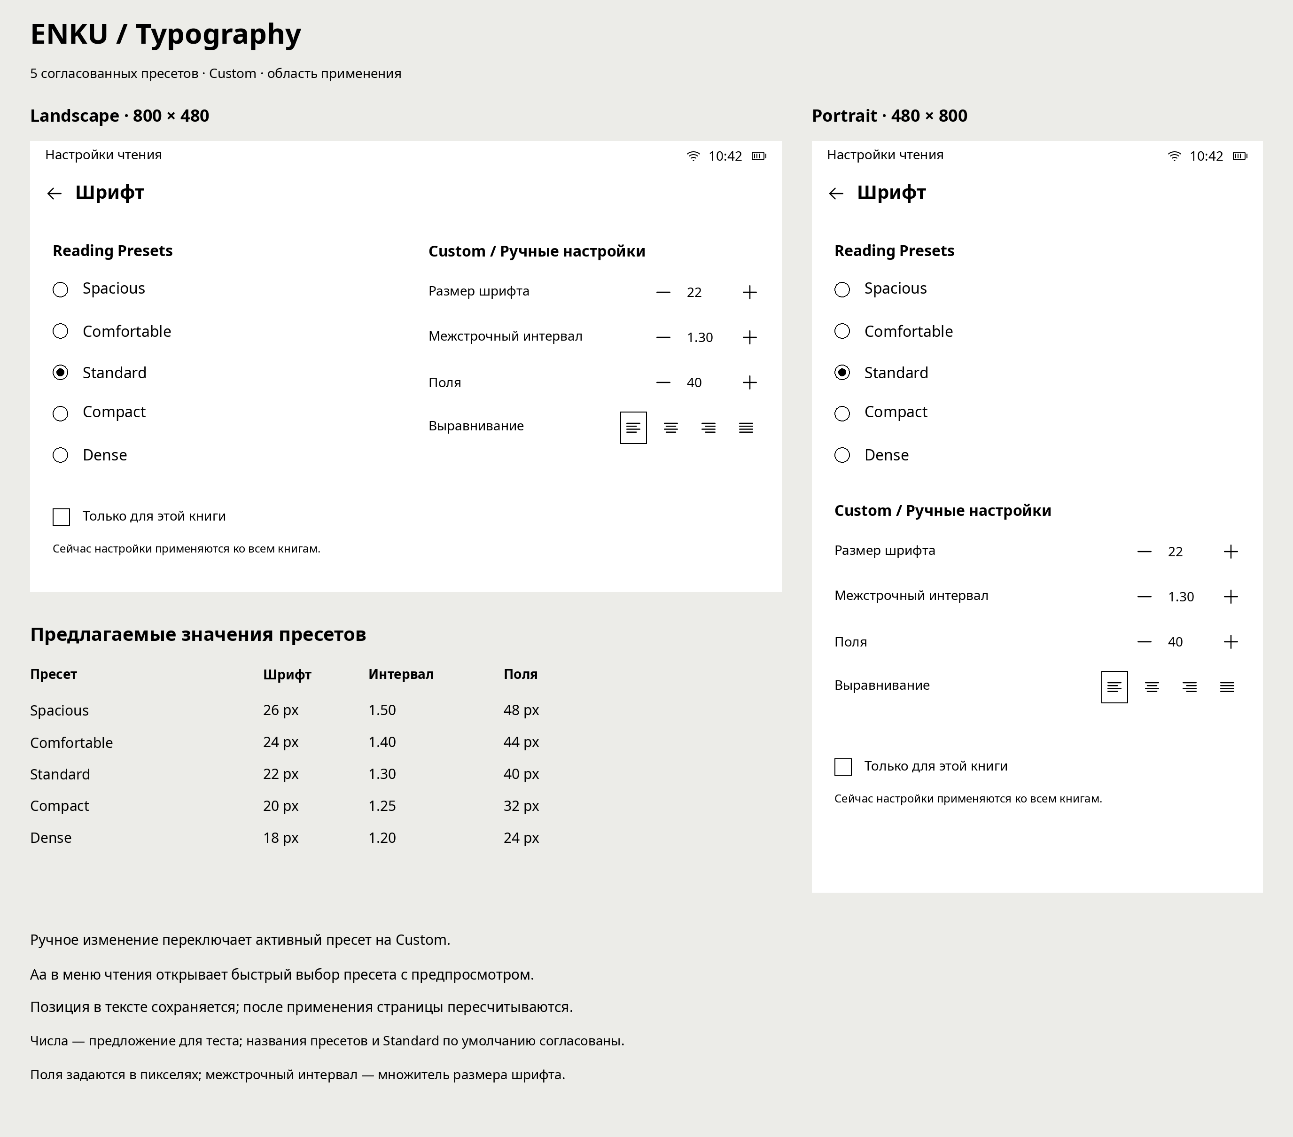
design/screens/ru/ENKU_typography_v1.png
