raznoglaz1y/enku/design/screens/ru/ENKU_ui_kit_core_v1.png

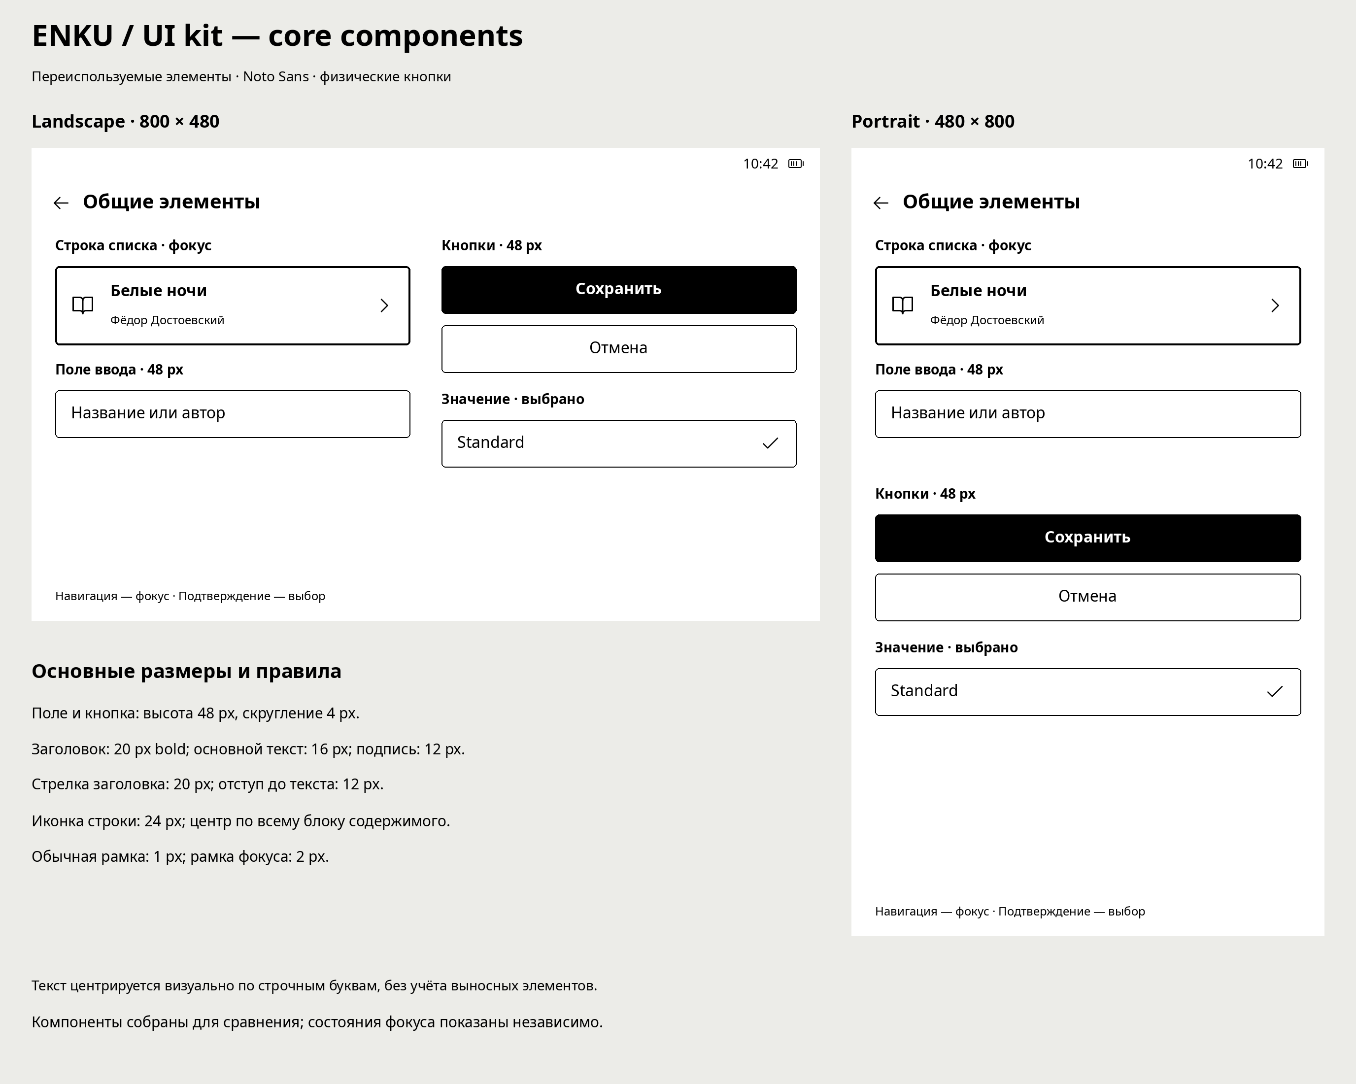
design/screens/ru/ENKU_ui_kit_core_v1.png
