raznoglaz1y/enku/design/screens/ru/ENKU_usb_transfer_v2.png

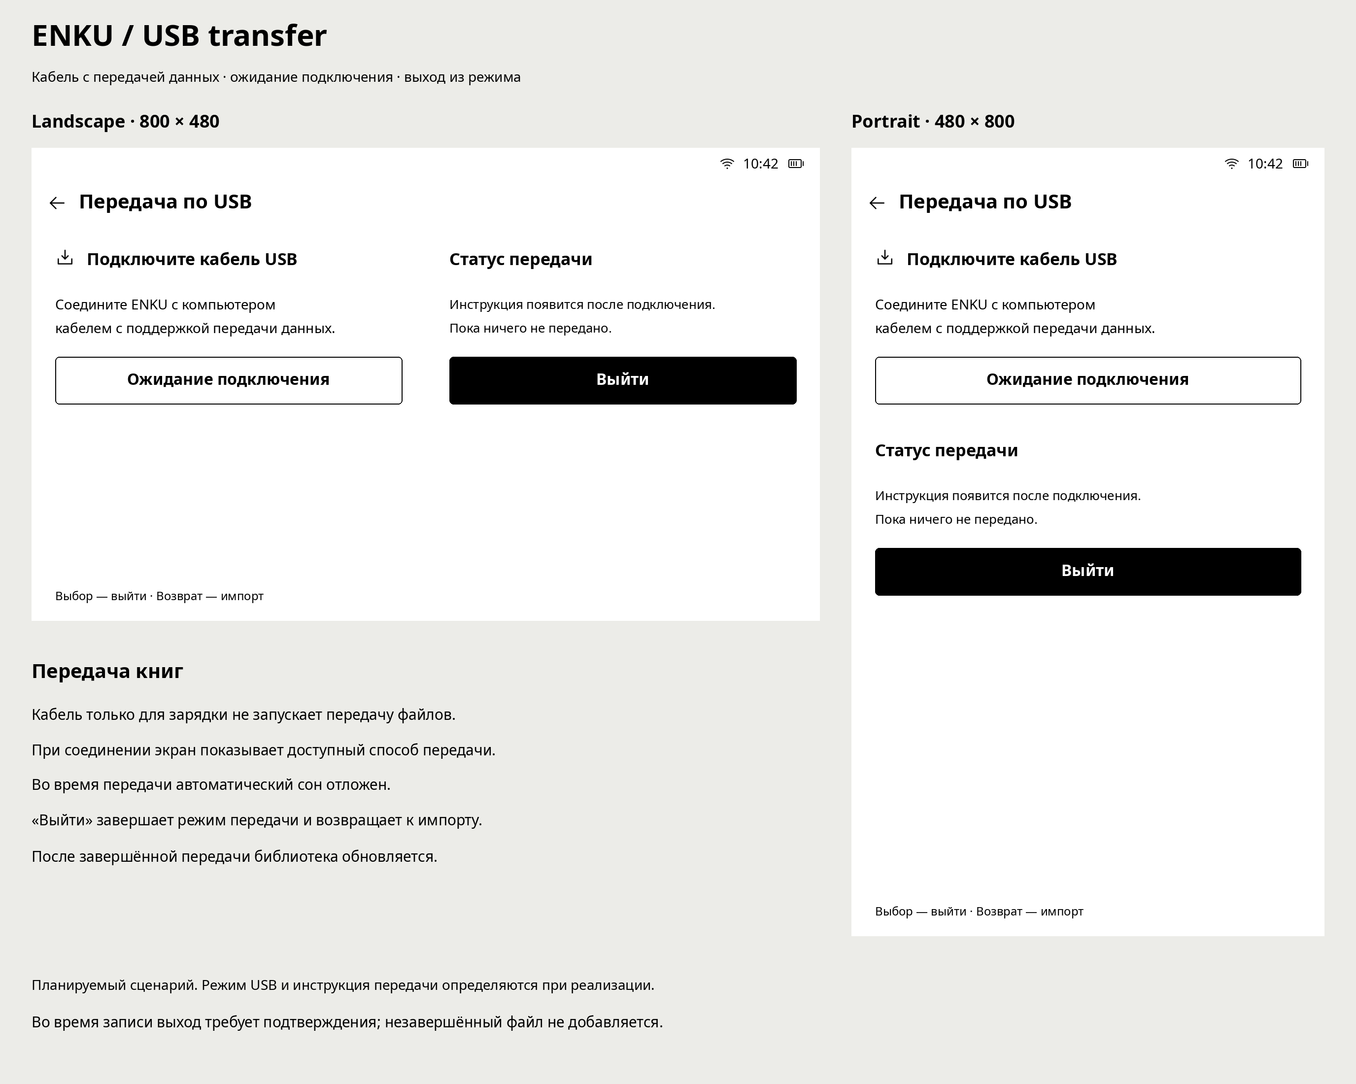
design/screens/ru/ENKU_usb_transfer_v2.png
