raznoglaz1y/enku/design/screens/ru/ENKU_wifi_password_v3.png

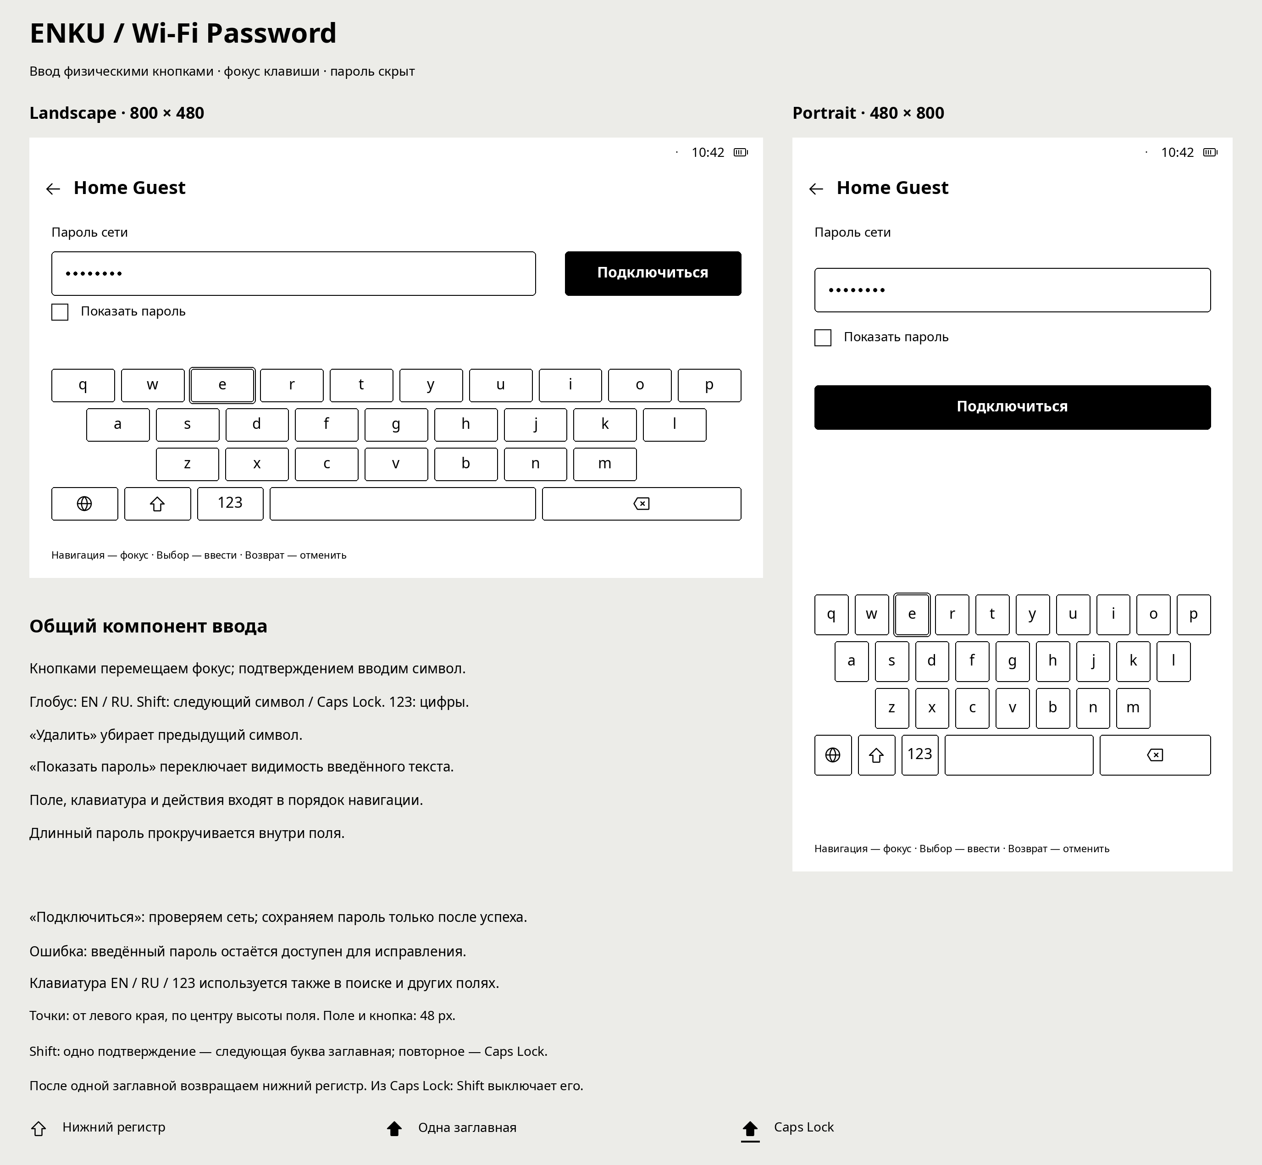
design/screens/ru/ENKU_wifi_password_v3.png
