raznoglaz1y/enku/design/screens/ru/ENKU_wifi_transfer_v1.png

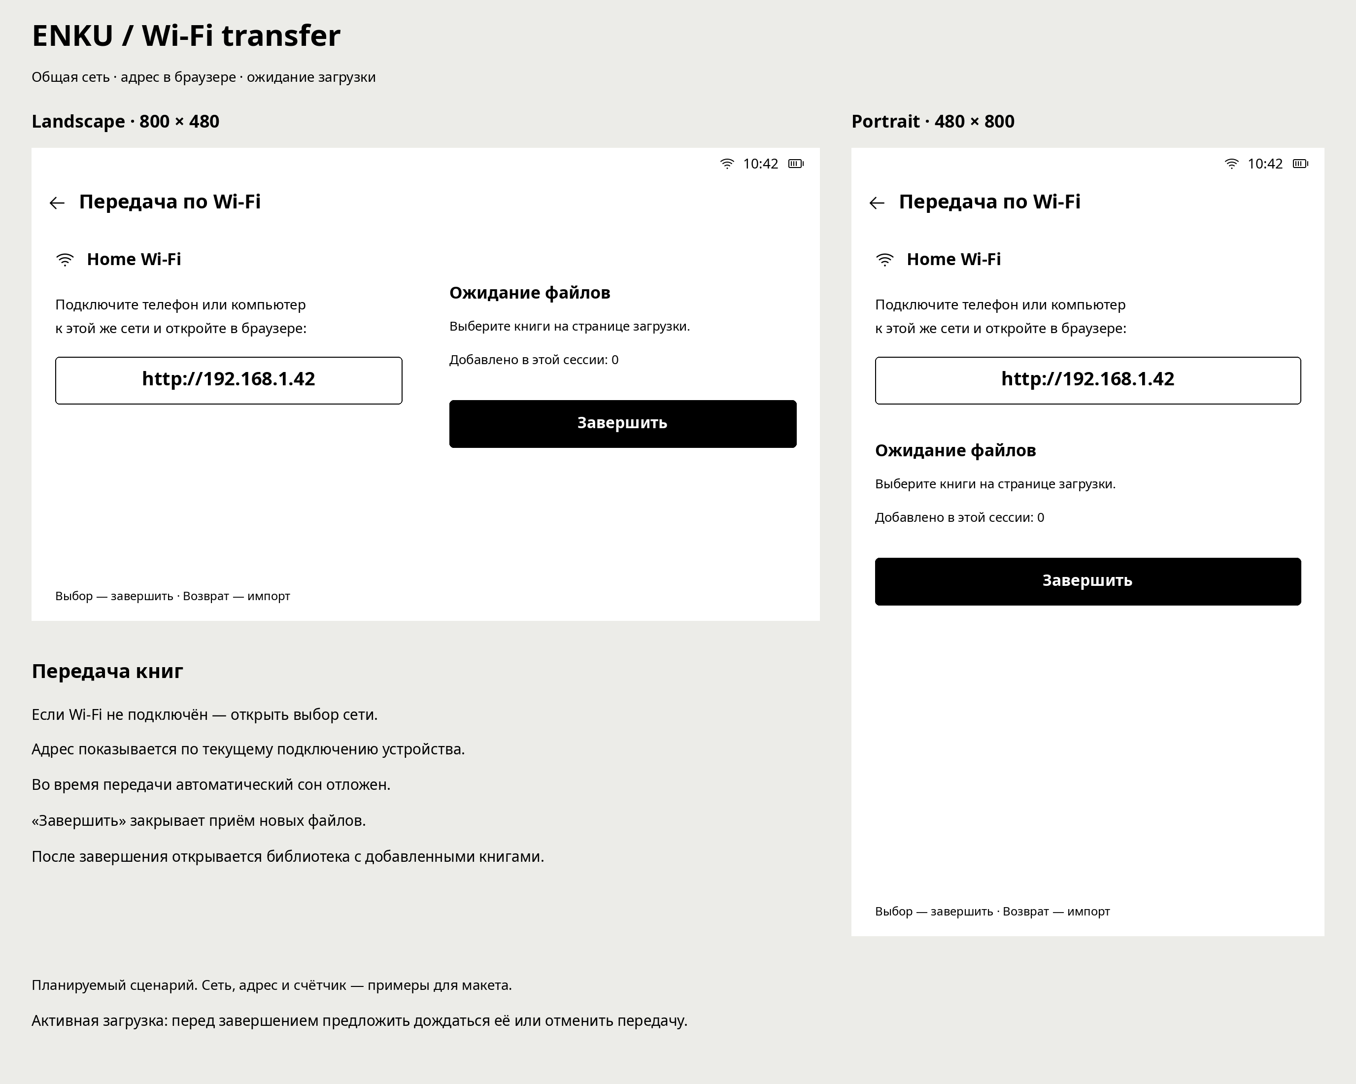
design/screens/ru/ENKU_wifi_transfer_v1.png
