raznoglaz1y/enku/site/assets/enku-reader-approved.webp

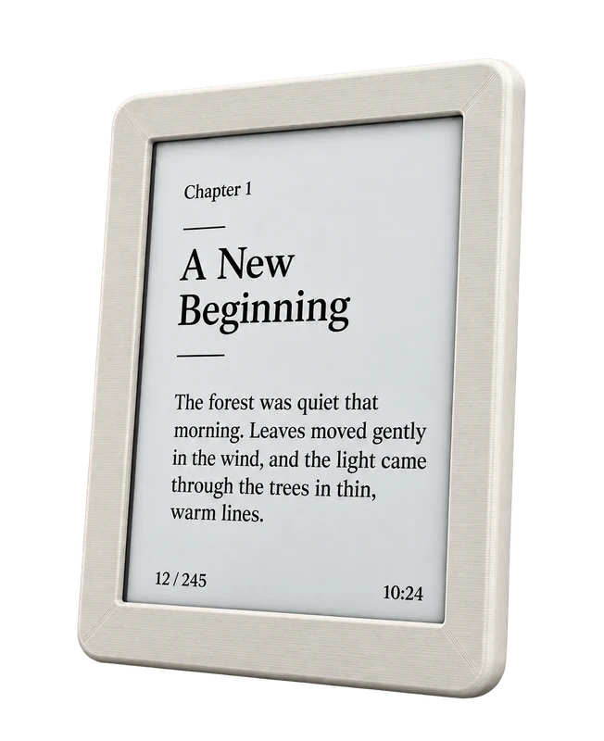
site/assets/enku-reader-approved.webp
