raznoglaz1y/enku/site/assets/og-enku.png

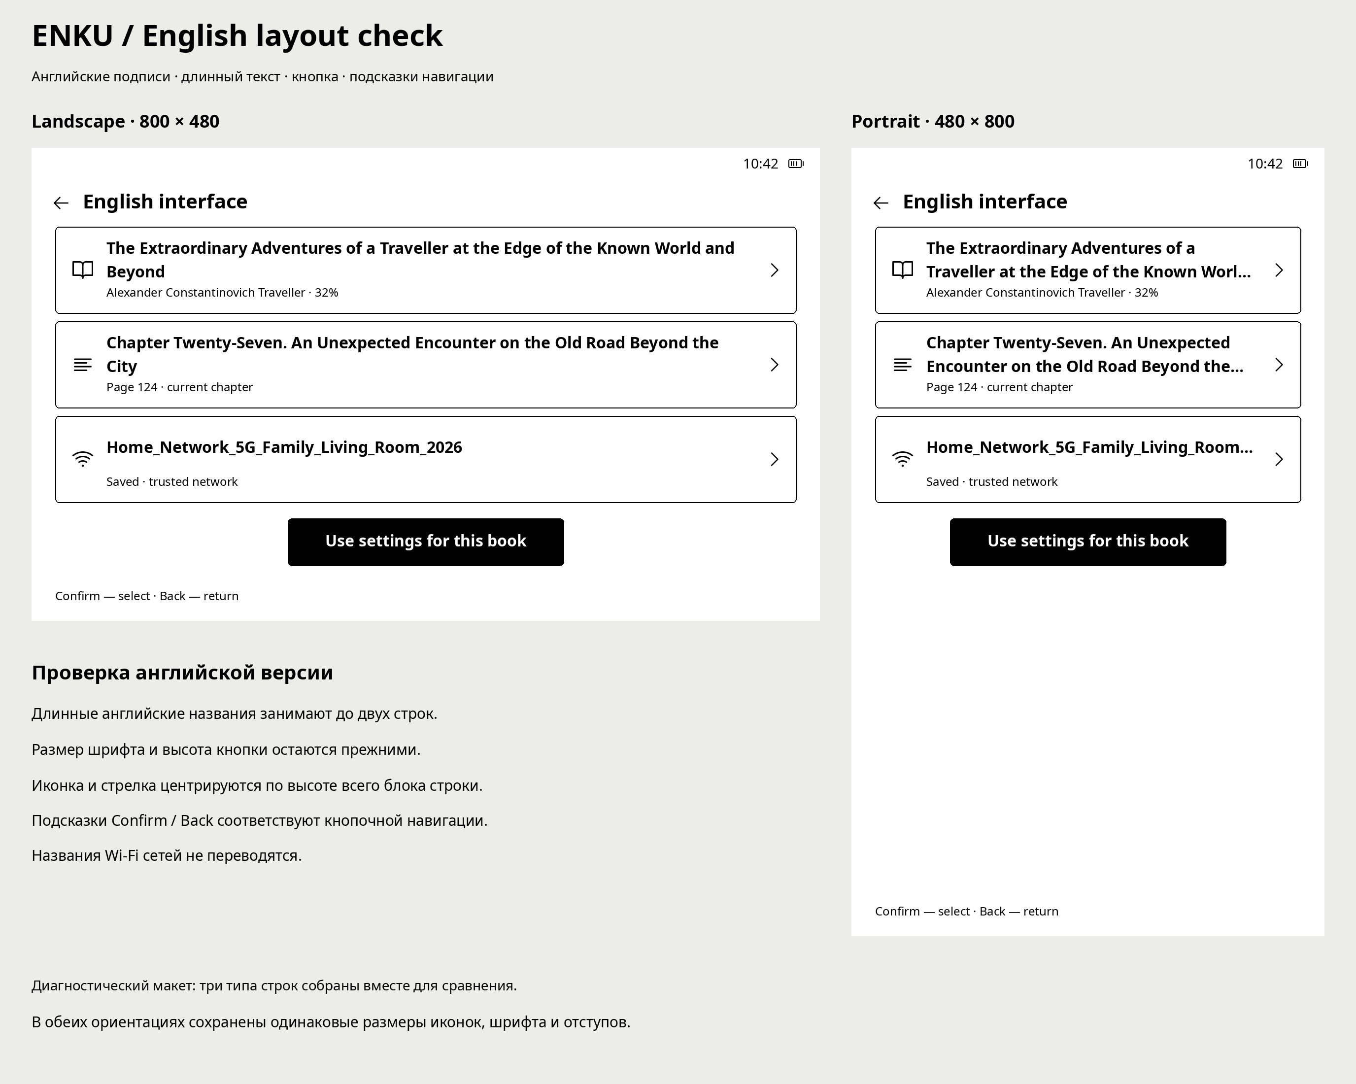
site/assets/og-enku.png
