raznoglaz1y/enku/firmware/platform/esp_idf/src/esp_idf_device_runtime.cpp

#include "enku/platform/esp_idf/esp_idf_device_runtime.hpp"

namespace enku::platform::esp_idf {
namespace {

constexpr std::uint32_t kDiagBoardProfileMismatch = 0x1001U;
constexpr std::uint32_t kDiagFontMissing = 0x1002U;
constexpr std::uint32_t kDiagFontInitFailed = 0x1003U;
constexpr std::uint32_t kDiagBootRecoveryRequired = 0x1004U;
constexpr std::uint32_t kDiagNetworkUnavailable = 0x2001U;
constexpr std::uint32_t kDiagNetworkPolicyFailed = 0x2002U;
constexpr std::uint32_t kDiagStorageLost = 0x3001U;
constexpr std::uint32_t kDiagStorageRecovered = 0x3002U;
constexpr std::uint32_t kDiagRuntimeFailed = 0x4001U;
constexpr std::uint32_t kDiagInputActionFailed = 0x5001U;

AppError fatalError(
    ErrorDomain domain,
    ErrorCode code
) {
    AppError error;
    error.domain = domain;
    error.severity = ErrorSeverity::FatalError;
    error.code = code;
    error.primary_action = RecoveryAction::Reboot;
    return error;
}

} // namespace

EspIdfDeviceRuntime::EspIdfDeviceRuntime(
    EspIdfPlatform& platform,
    TypographySettings typography,
    Viewport viewport
)
    : platform_(platform),
      storage_(
          platform_.stateFiles(),
          platform_.bookFiles()
      ),
      availability_reconciler_(
          storage_.appState(),
          storage_.library(),
          platform_.bookFiles()
      ),
      text_renderer_(
          platform_.framebuffer()
      ),
      reader_(
          storage_,
          platform_.refresh(),
          text_renderer_,
          text_renderer_,
          text_renderer_,
          typography,
          viewport
      ),
      reader_overlay_(
          storage_,
          reader_,
          &text_renderer_,
          &platform_.refresh()
      ),
      search_(
          storage_,
          reader_,
          &text_renderer_,
          &platform_.refresh()
      ),
      library_search_(
          storage_.appState(),
          reader_.library()
      ),
      book_details_(
          storage_.appState(),
          storage_.library(),
          reader_.library(),
          reader_.reader(),
          storage_.checkpoints(),
          storage_.deleteService(),
          &text_renderer_,
          &platform_.refresh()
      ),
      book_finished_(
          storage_.appState(),
          storage_.library(),
          reader_.library(),
          reader_.reader(),
          storage_.checkpoints(),
          &text_renderer_,
          &platform_.refresh()
      ),
      contents_bookmarks_(
          storage_.appState(),
          reader_,
          storage_.bookmarks(),
          &text_renderer_,
          &platform_.refresh()
      ),
      about_book_(
          storage_.appState(),
          storage_.library(),
          reader_,
          &text_renderer_,
          &platform_.refresh()
      ),
      settings_nav_(
          storage_.appState(),
          reader_.library(),
          &text_renderer_,
          &platform_.refresh()
      ),
      reading_settings_(
          storage_.appState(),
          storage_,
          reader_,
          settings_nav_,
          &text_renderer_,
          &platform_.refresh()
      ),
      display_settings_(
          storage_.appState(),
          reader_,
          settings_nav_,
          &text_renderer_,
          &platform_.refresh()
      ),
      locale_settings_(
          storage_.appState(),
          storage_,
          settings_nav_,
          &text_renderer_,
          &platform_.refresh()
      ),
      about_device_(
          storage_.appState(),
          settings_nav_,
          &text_renderer_,
          &platform_.refresh()
      ),
      network_lifecycle_(
          storage_.appState(),
          platform_.network(),
          platform_.network()
      ),
      web_upload_server_(
          storage_.webUpload(),
          storage_.library()
      ),
      sleep_wake_(
          storage_.appState(),
          storage_.library(),
          storage_.checkpoints(),
          storage_.appContext(),
          network_lifecycle_,
          platform_.power(),
          reader_.bootRestore()
      ),
      power_off_(
          storage_.appState(),
          storage_.library(),
          storage_.checkpoints(),
          storage_.appContext(),
          platform_.network(),
          platform_.power()
      ),
      power_off_confirm_(
          storage_.appState(),
          power_off_,
          settings_nav_,
          &text_renderer_,
          &platform_.refresh()
      ),
      wifi_settings_(
          storage_.appState(),
          storage_,
          platform_.network(),
          platform_.network(),
          network_lifecycle_,
          settings_nav_,
          &text_renderer_,
          &platform_.refresh()
      ),
      input_dispatcher_(
          storage_.appState(),
          reader_.library(),
          reader_.reader(),
          sleep_wake_,
          power_off_,
          &reader_overlay_,
          &search_,
          &library_search_,
          &book_details_,
          &book_finished_,
          &contents_bookmarks_,
          &about_book_,
          &settings_nav_,
          &reading_settings_,
          &display_settings_,
          &locale_settings_,
          &about_device_,
          &power_off_confirm_,
          &wifi_settings_
      ) {
    text_renderer_.bindAppState(
        storage_.appState()
    );
}

DeviceRuntimeInitStatus
EspIdfDeviceRuntime::begin() {
    switch (platform_.removableStorageStatus()) {
        case SdMountStatus::Ok:
            storage_.appState().storage.removable =
                RemovableStorageStatus::Ready;
            break;
        case SdMountStatus::DirectorySetupFailed:
            storage_.appState().storage.removable =
                RemovableStorageStatus::SetupError;
            break;
        case SdMountStatus::MountFailed:
        default:
            storage_.appState().storage.removable =
                RemovableStorageStatus::Unavailable;
            break;
    }

    if (!isReaderBoardProfileValid(
            platform_.boardProfile(),
            EspIdfEpaper::kWidth,
            EspIdfEpaper::kHeight
        )) {
        diagnostic_log_.write(
            LogLevel::Critical,
            LogCategory::Core,
            kDiagBoardProfileMismatch,
            "Board profile does not match the active display target"
        );
        diagnostics_.report(
            fatalError(
                ErrorDomain::System,
                kDiagBoardProfileMismatch
            )
        );
        return DeviceRuntimeInitStatus::BoardProfileMismatch;
    }

    const auto font_status =
        text_renderer_.begin(
            storage_.appState().
                typography.font_size_px
        );

    if (font_status ==
        FontInitStatus::FontNotFound) {
        diagnostic_log_.write(
            LogLevel::Critical,
            LogCategory::Ui,
            kDiagFontMissing,
            "Reader font is unavailable"
        );
        diagnostics_.report(
            fatalError(
                ErrorDomain::Localization,
                kDiagFontMissing
            )
        );
        return DeviceRuntimeInitStatus::FontMissing;
    }

    if (font_status != FontInitStatus::Ok) {
        diagnostic_log_.write(
            LogLevel::Critical,
            LogCategory::Ui,
            kDiagFontInitFailed,
            "Reader font initialization failed"
        );
        diagnostics_.report(
            fatalError(
                ErrorDomain::Localization,
                kDiagFontInitFailed
            )
        );
        return DeviceRuntimeInitStatus::FontInitFailed;
    }

    boot_result_ = reader_.bootRestore().run();
    availability_reconciler_.reconcile();

    if (boot_result_.status ==
        BootRestoreStatus::RecoveryRequired) {
        diagnostic_log_.write(
            LogLevel::Critical,
            LogCategory::Persistence,
            kDiagBootRecoveryRequired,
            "Boot restore requires recovery mode"
        );
        diagnostics_.report(
            fatalError(
                ErrorDomain::Persistence,
                kDiagBootRecoveryRequired
            )
        );
        return DeviceRuntimeInitStatus::RecoveryRequired;
    }

    if (platform_.networkAvailable()) {
        network_policy_status_ =
            applyNetworkPolicy();

        if (network_policy_status_ ==
            NetworkPolicyStatus::DriverError) {
            storage_.appState().network.status =
                NetworkRuntimeStatus::Error;
            diagnostic_log_.write(
                LogLevel::Warning,
                LogCategory::Network,
                kDiagNetworkPolicyFailed,
                "Network policy failed; continuing offline"
            );
        }
    } else {
        network_policy_status_ =
            NetworkPolicyStatus::DriverError;
        storage_.appState().network.connected = false;
        storage_.appState().network.status =
            NetworkRuntimeStatus::Error;
        storage_.appState().network.ssid.clear();
        storage_.appState().network.address.clear();
        diagnostic_log_.write(
            LogLevel::Warning,
            LogCategory::Network,
            kDiagNetworkUnavailable,
            "Wi-Fi driver unavailable; continuing offline"
        );
    }

    syncPlatformState();
    syncWebUploadServer();

    return DeviceRuntimeInitStatus::Ok;
}

ApplicationStorageRuntime&
EspIdfDeviceRuntime::storage() {
    return storage_;
}

ApplicationReaderRuntime&
EspIdfDeviceRuntime::reader() {
    return reader_;
}

FreeTypeTextRenderer&
EspIdfDeviceRuntime::textRenderer() {
    return text_renderer_;
}

LibrarySearchRuntime&
EspIdfDeviceRuntime::librarySearch() {
    return library_search_;
}

BookDetailsRuntime&
EspIdfDeviceRuntime::bookDetails() {
    return book_details_;
}

BookFinishedRuntime&
EspIdfDeviceRuntime::bookFinished() {
    return book_finished_;
}

ContentsBookmarksRuntime&
EspIdfDeviceRuntime::contentsBookmarks() {
    return contents_bookmarks_;
}

AboutBookRuntime&
EspIdfDeviceRuntime::aboutBook() {
    return about_book_;
}

SettingsNavigationRuntime&
EspIdfDeviceRuntime::settingsNavigation() {
    return settings_nav_;
}

ReadingSettingsRuntime&
EspIdfDeviceRuntime::readingSettings() {
    return reading_settings_;
}

DisplaySettingsRuntime&
EspIdfDeviceRuntime::displaySettings() {
    return display_settings_;
}

LocaleSettingsRuntime&
EspIdfDeviceRuntime::localeSettings() {
    return locale_settings_;
}

AboutDeviceRuntime&
EspIdfDeviceRuntime::aboutDevice() {
    return about_device_;
}

PowerOffConfirmRuntime&
EspIdfDeviceRuntime::powerOffConfirm() {
    return power_off_confirm_;
}

WiFiSettingsRuntime&
EspIdfDeviceRuntime::wifiSettings() {
    return wifi_settings_;
}

SleepWakeCoordinator&
EspIdfDeviceRuntime::sleepWake() {
    return sleep_wake_;
}

PowerOffCoordinator&
EspIdfDeviceRuntime::powerOff() {
    return power_off_;
}

InputDispatcher&
EspIdfDeviceRuntime::input() {
    return input_dispatcher_;
}

DiagnosticRingLogService&
EspIdfDeviceRuntime::diagnosticLog() {
    return diagnostic_log_;
}

InMemoryDiagnosticsService&
EspIdfDeviceRuntime::diagnostics() {
    return diagnostics_;
}

NetworkPolicyStatus
EspIdfDeviceRuntime::applyNetworkPolicy() {
    network_lifecycle_.applyPolicy();
    network_policy_status_ =
        network_lifecycle_.lastPolicyStatus();
    syncPlatformState();
    return network_policy_status_;
}

DeviceNetworkUpdateStatus
EspIdfDeviceRuntime::setWiFiPolicy(
    WiFiPolicy policy
) {
    auto& app = storage_.appState();
    const auto previous = app.wifi_policy;

    if (storage_.settingsRuntime().handle(
            WiFiPolicyChanged{policy}
        ) != PersistStatus::Ok) {
        return DeviceNetworkUpdateStatus::SettingsSaveFailed;
    }

    const auto lifecycle_result =
        network_lifecycle_.applyPolicy();
    const auto status =
        network_lifecycle_.lastPolicyStatus();

    if (lifecycle_result ==
            NetworkLifecycleResult::Failed ||
        status == NetworkPolicyStatus::DriverError) {
        // Best-effort rollback keeps durable policy aligned with hardware.
        storage_.settingsRuntime().handle(
            WiFiPolicyChanged{previous}
        );
        network_lifecycle_.applyPolicy();
        syncPlatformState();
        return DeviceNetworkUpdateStatus::DriverError;
    }

    syncPlatformState();

    if (status ==
        NetworkPolicyStatus::NoTrustedNetwork) {
        return DeviceNetworkUpdateStatus::NoTrustedNetwork;
    }

    return DeviceNetworkUpdateStatus::Ok;
}

DeviceNetworkUpdateStatus
EspIdfDeviceRuntime::setTrustedNetwork(
    std::string_view ssid,
    std::string_view password
) {
    const auto stored =
        platform_.network().setTrustedNetwork(
            ssid,
            password
        );

    if (stored ==
        NetworkPolicyStatus::InvalidCredentials) {
        return DeviceNetworkUpdateStatus::InvalidCredentials;
    }

    if (stored != NetworkPolicyStatus::Ok) {
        return DeviceNetworkUpdateStatus::DriverError;
    }

    if (storage_.appState().wifi_policy ==
        WiFiPolicy::AutoConnectTrusted) {
        const auto applied =
            network_lifecycle_.applyPolicy();

        if (applied == NetworkLifecycleResult::Failed) {
            return DeviceNetworkUpdateStatus::DriverError;
        }
    }

    syncPlatformState();
    return DeviceNetworkUpdateStatus::Ok;
}

DeviceNetworkUpdateStatus
EspIdfDeviceRuntime::forgetTrustedNetwork() {
    const auto status =
        platform_.network().forgetTrustedNetwork();

    if (status != NetworkPolicyStatus::Ok) {
        return DeviceNetworkUpdateStatus::DriverError;
    }

    network_lifecycle_.sync();
    syncPlatformState();
    return DeviceNetworkUpdateStatus::Ok;
}

void EspIdfDeviceRuntime::syncPlatformState() {
    auto& app = storage_.appState();

    network_lifecycle_.sync();

    const auto battery =
        platform_.power().batteryState();

    app.power.battery_percent =
        battery.percent;
    app.power.charging =
        battery.charging;

    // Snapshot the thread-safe HTTP ingress activity into AppState for UI
    // and sleep policy decisions. The HTTP task never writes AppState.
    app.import_active =
        storage_.webUpload().active();
}

bool EspIdfDeviceRuntime::syncWebUploadServer() {
    const auto& app = storage_.appState();

    const bool online =
        app.network.status ==
            NetworkRuntimeStatus::Connected &&
        app.screen != Screen::Sleep &&
        app.storage.removable ==
            RemovableStorageStatus::Ready;

    return web_upload_server_.sync(online);
}

bool EspIdfDeviceRuntime::syncRemovableStorage(
    std::uint32_t now_ms
) {
    auto& app = storage_.appState();

    constexpr std::uint32_t kRetryIntervalMs = 2000U;

    if (now_ms - last_storage_retry_ms_ <
        kRetryIntervalMs) {
        return false;
    }

    last_storage_retry_ms_ = now_ms;

    const auto previous =
        app.storage.removable;

    if (previous ==
        RemovableStorageStatus::Ready) {
        if (platform_.sdCard().healthy()) {
            return false;
        }

        platform_.sdCard().unmount();
        app.storage.removable =
            RemovableStorageStatus::Unavailable;
        diagnostic_log_.write(
            LogLevel::Warning,
            LogCategory::Storage,
            kDiagStorageLost,
            "Removable storage became unavailable"
        );
        availability_reconciler_.reconcile();

        if (app.current_book.has_value() &&
            app.reading_position.has_value()) {
            const auto reader_result =
                reader_.reader().handle(
                    RemovableStorageLost{}
                );

            // RemovableStorageLost is fail-safe: persistence errors are
            // reported by the reader result, but the reader still tears down
            // its live session and returns to Library. Refresh based on the
            // resulting screen state so a dead SD never leaves stale reader
            // pixels visible after recovery.
            if (app.screen == Screen::Library) {
                const auto library_result =
                    reader_.library().handle(
                        LibraryRefreshRequested{}
                    );

                return library_result ==
                           LibraryRuntimeResult::Applied ||
                       library_result ==
                           LibraryRuntimeResult::Empty;
            }

            (void)reader_result;
        }

        library_refresh_pending_ = true;
        return true;
    }

    const auto status =
        platform_.retryRemovableStorage();

    switch (status) {
        case SdMountStatus::Ok:
            app.storage.removable =
                RemovableStorageStatus::Ready;
            diagnostic_log_.write(
                LogLevel::Info,
                LogCategory::Storage,
                kDiagStorageRecovered,
                "Removable storage recovered; verification started"
            );
            availability_reconciler_.beginIncremental();
            break;
        case SdMountStatus::DirectorySetupFailed:
            app.storage.removable =
                RemovableStorageStatus::SetupError;
            break;
        case SdMountStatus::MountFailed:
        default:
            app.storage.removable =
                RemovableStorageStatus::Unavailable;
            break;
    }

    if (previous != app.storage.removable) {
        library_refresh_pending_ = true;
        return true;
    }

    return false;
}


void EspIdfDeviceRuntime::processWebDeleteRequests() {
    std::string book_id;
    if (!web_upload_server_.takeDeleteRequest(
            book_id
        )) {
        return;
    }

    const auto& app = storage_.appState();

    // Never remove the source of the book currently open in the reader.
    // The browser can retry once the user returns to Library.
    if (app.screen == Screen::Reading &&
        app.current_book ==
            std::optional<BookId>{book_id}) {
        web_upload_server_.completeDelete(
            book_id,
            "active_book"
        );
        return;
    }

    const auto status =
        storage_.deleteService().remove(
            book_id
        );

    if (status == BookDeleteStatus::Ok) {
        library_refresh_pending_ = true;
        web_upload_server_.completeDelete(
            book_id,
            "ok"
        );
        return;
    }

    if (status == BookDeleteStatus::NotFound) {
        web_upload_server_.completeDelete(
            book_id,
            "not_found"
        );
        return;
    }

    web_upload_server_.completeDelete(
        book_id,
        "failed_" +
            std::to_string(
                static_cast<unsigned>(status)
            )
    );
}

void EspIdfDeviceRuntime::refreshLibraryAfterUploadIfNeeded() {
    if (web_upload_server_.takeUploadCompleted()) {
        library_refresh_pending_ = true;
    }

    if (!library_refresh_pending_ ||
        storage_.appState().screen != Screen::Library) {
        return;
    }

    const auto result =
        reader_.library().handle(
            LibraryRefreshRequested{}
        );

    if (result == LibraryRuntimeResult::Applied ||
        result == LibraryRuntimeResult::Empty) {
        library_refresh_pending_ = false;
    }
}

bool EspIdfDeviceRuntime::refreshStatusBarIfNeeded() {
    auto& app = storage_.appState();

    if (app.screen == Screen::Sleep) {
        return true;
    }

    const bool changed =
        !status_snapshot_valid_ ||
        rendered_network_status_ !=
            app.network.status ||
        rendered_battery_percent_ !=
            app.power.battery_percent ||
        rendered_charging_ !=
            app.power.charging ||
        rendered_orientation_ !=
            app.orientation;

    if (!changed) {
        return true;
    }

    if (!text_renderer_.renderStatusBar(app)) {
        return false;
    }

    RefreshRequest request;
    request.refresh_class =
        RefreshClass::Region;
    request.reason =
        RefreshReason::StatusChanged;
    request.generation = 0;
    request.may_coalesce = false;
    request.may_defer = false;

    if (app.orientation == Orientation::Landscape) {
        request.dirty_region =
            Rect{
                0,
                0,
                EspIdfEpaper::kWidth,
                24,
            };
    } else {
        request.dirty_region =
            Rect{
                static_cast<std::uint16_t>(
                    EspIdfEpaper::kWidth - 24
                ),
                0,
                24,
                EspIdfEpaper::kHeight,
            };
    }

    if (!platform_.refresh().submit(request)) {
        return false;
    }

    rendered_network_status_ =
        app.network.status;
    rendered_battery_percent_ =
        app.power.battery_percent;
    rendered_charging_ =
        app.power.charging;
    rendered_orientation_ =
        app.orientation;
    status_snapshot_valid_ = true;

    return true;
}

InputDispatchResult EspIdfDeviceRuntime::pollInput(
    std::uint32_t now_ms
) {
    syncRemovableStorage(now_ms);

    // Verify at most one library record per poll after a hot remount. Books
    // stay fail-closed (unavailable) until their content fingerprint passes.
    // Boot keeps the synchronous path so initial UI state is deterministic.
    if (availability_reconciler_.active()) {
        availability_reconciler_.step(1U);
        library_refresh_pending_ = true;
    }

    syncPlatformState();

    // Network services follow the same authoritative lifecycle state as
    // the UI. The uploader exists only while the reader is online and awake.
    syncWebUploadServer();
    processWebDeleteRequests();
    refreshLibraryAfterUploadIfNeeded();

    // Status changes are independent of user input. Keep the e-ink update
    // constrained to the compact top bar instead of refreshing the screen.
    // A persistent renderer/refresh failure must propagate to the outer
    // application loop instead of being silently ignored.
    if (!refreshStatusBarIfNeeded()) {
        diagnostic_log_.write(
            LogLevel::Error,
            LogCategory::Display,
            kDiagRuntimeFailed,
            "Status-bar render or refresh failed"
        );
        return InputDispatchResult::RuntimeFailed;
    }

    const auto event =
        platform_.buttons().poll(now_ms);

    if (!event.has_value()) {
        return InputDispatchResult::Ignored;
    }

    const auto result =
        input_dispatcher_.handle(*event);

    // Sleep/wake and Wi-Fi settings can change network availability while
    // dispatching this very input. Reconcile the HTTP service immediately
    // instead of waiting for the next poll cycle.
    syncPlatformState();
    syncWebUploadServer();
    processWebDeleteRequests();
    refreshLibraryAfterUploadIfNeeded();

    if (result == InputDispatchResult::RuntimeFailed) {
        diagnostic_log_.write(
            LogLevel::Error,
            LogCategory::Ui,
            kDiagRuntimeFailed,
            "Input dispatch reported a runtime failure"
        );
    } else if (result == InputDispatchResult::Failed) {
        diagnostic_log_.write(
            LogLevel::Warning,
            LogCategory::Input,
            kDiagInputActionFailed,
            "Input action failed"
        );
    }

    return result;
}

const BoardProfile&
EspIdfDeviceRuntime::boardProfile() const {
    return platform_.boardProfile();
}

bool EspIdfDeviceRuntime::supports(
    BoardFeature feature
) const {
    return supportsFeature(
        platform_.boardProfile().capabilities,
        feature
    );
}

const BootRestoreResult&
EspIdfDeviceRuntime::bootResult() const {
    return boot_result_;
}

} // namespace enku::platform::esp_idf
