raznoglaz1y/enku/firmware/platform/esp_idf/src/esp_idf_platform.cpp

#include "enku/platform/esp_idf/esp_idf_platform.hpp"

#include "enku/platform/esp_idf/board.hpp"
#include "enku/platform/esp_idf/board_profiles.hpp"

namespace enku::platform::esp_idf {

EspIdfPlatform::EspIdfPlatform()
    : state_filesystem_(
          EspIdfInternalStateStorage::kMountPoint
      ),
      book_filesystem_(board::kSdMountPoint),
      state_files_(state_filesystem_),
      book_files_(book_filesystem_),
      framebuffer_(
          EspIdfEpaper::kWidth,
          EspIdfEpaper::kHeight
      ),
      refresh_(display_, framebuffer_) {}

PlatformInitStatus EspIdfPlatform::begin() {
    // Bring up the user-visible/control path before removable storage.
    // If the SD card is missing or unreadable, app_main can still render a
    // deterministic recovery screen instead of failing before the display
    // and controls exist.
    if (!refresh_.begin()) {
        return PlatformInitStatus::DisplayInitFailed;
    }

    if (internal_state_storage_.begin() !=
        InternalStateMountStatus::Ok) {
        return PlatformInitStatus::StateStorageFailed;
    }

    // PMU telemetry/suspend is valuable but not required for basic
    // offline reading on an already powered device.
    power_available_ = power_.begin();

    // Networking is optional for an offline-first reader. Preserve the
    // failure state for UI/diagnostics, but do not block Library/Reading.
    network_available_ = network_.begin();

    if (!buttons_.begin()) {
        return PlatformInitStatus::ButtonsInitFailed;
    }

    removable_storage_status_ =
        sd_card_.mount();

    // System state now lives in internal flash. Removable storage contains
    // books and large user data, so an unavailable/unusable card must not
    // prevent the core application from reaching Library.
    return PlatformInitStatus::Ok;
}

EspIdfSdCard& EspIdfPlatform::sdCard() {
    return sd_card_;
}

EspIdfFilesystem& EspIdfPlatform::filesystem() {
    return book_filesystem_;
}

EspIdfStateFileStore& EspIdfPlatform::stateFiles() {
    return state_files_;
}

EspIdfBookFileStore& EspIdfPlatform::bookFiles() {
    return book_files_;
}

EspIdfEpaper& EspIdfPlatform::display() {
    return display_;
}

OwnedMonoFramebuffer& EspIdfPlatform::framebuffer() {
    return framebuffer_;
}

EpaperRefreshService& EspIdfPlatform::refresh() {
    return refresh_;
}

EspIdfPowerService& EspIdfPlatform::power() {
    return power_;
}

EspIdfNetworkService& EspIdfPlatform::network() {
    return network_;
}

bool EspIdfPlatform::powerAvailable() const {
    return power_available_;
}

EspIdfButtons& EspIdfPlatform::buttons() {
    return buttons_;
}

bool EspIdfPlatform::networkAvailable() const {
    return network_available_;
}

SdMountStatus EspIdfPlatform::removableStorageStatus() const {
    return removable_storage_status_;
}

SdMountStatus EspIdfPlatform::retryRemovableStorage() {
    removable_storage_status_ =
        sd_card_.mount();
    return removable_storage_status_;
}

const BoardProfile& EspIdfPlatform::boardProfile() const {
    return board_profiles::kWaveshareEsp32S3Epaper397;
}

} // namespace enku::platform::esp_idf
