raznoglaz1y/enku/firmware/tests/book_availability_reconciler_tests.cpp

#include "enku/runtime/book_availability_reconciler.hpp"
#include "enku/storage/posix_book_file_store.hpp"
#include "enku/storage/posix_state_file_store.hpp"
#include "enku/storage/book_fingerprint.hpp"

#include <cassert>
#include <filesystem>

using namespace enku;

int main() {
    const auto root =
        std::filesystem::temp_directory_path() /
        "enku-book-availability-reconciler-test";

    std::error_code ec;
    std::filesystem::remove_all(root, ec);

    PosixStateFileStore state_files(root);
    PosixBookFileStore book_files(root);
    CborLibraryService library(state_files);

    BookRecord first;
    first.book_id = "first";
    first.format = BookFormat::Txt;
    first.source_path = "/books/first.txt";
    first.source_filename = "first.txt";
    first.file_size = 5;
    first.fingerprint = fingerprintBookBytes("12345");

    BookRecord second;
    second.book_id = "second";
    second.format = BookFormat::Txt;
    second.source_path = "/books/second.txt";
    second.source_filename = "second.txt";
    second.file_size = 6;
    second.fingerprint = fingerprintBookBytes("123456");

    assert(library.upsert(first) == LibraryStatus::Ok);
    assert(library.upsert(second) == LibraryStatus::Ok);

    AppState app;
    BookAvailabilityReconciler reconciler(
        app,
        library,
        book_files
    );

    app.storage.removable =
        RemovableStorageStatus::Unavailable;
    reconciler.reconcile();

    assert(!app.library.bookAvailable("first"));
    assert(!app.library.bookAvailable("second"));
    assert(app.library.unavailable_books.size() == 2U);
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
